wsilverio/tcc/cad/arquivos-maristela/mesa bolinhas_final1.pdf

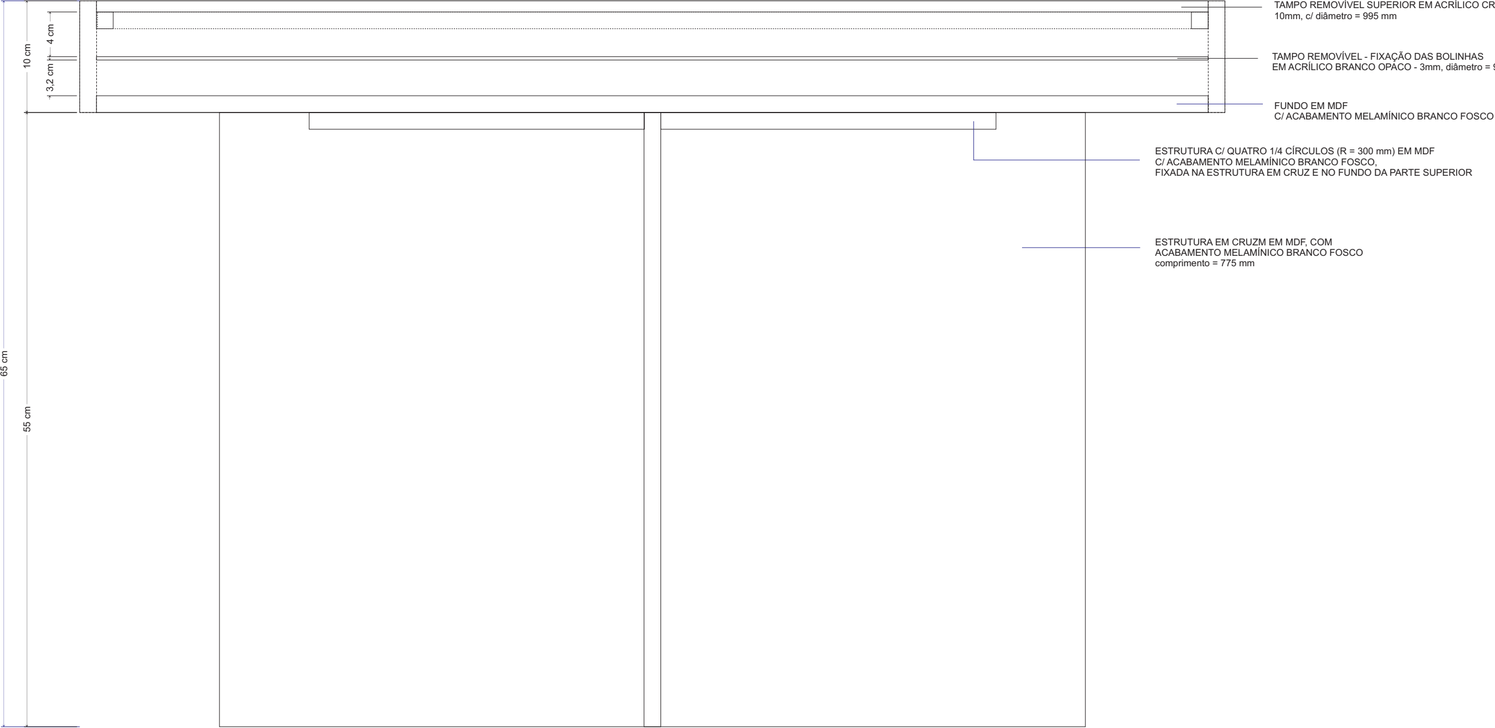
[picture p51: figure]
FUNDO EM MDF C/ ACABAMENTO MELAMÍNICO BRANCO FOSCO; C/ ACABAMENTO MELAMÍNICO BRANCO FOSCO,; ESTRUTURA EM CRUZM EM MDF, COM ACABAMENTO MELAMÍNICO BRANCO FOSCO comprimento = 775 mm; 10mm, c/ diâmetro = 995 mm; TAMPO REMOVÍVEL - FIXAÇÃO DAS BOLINHAS
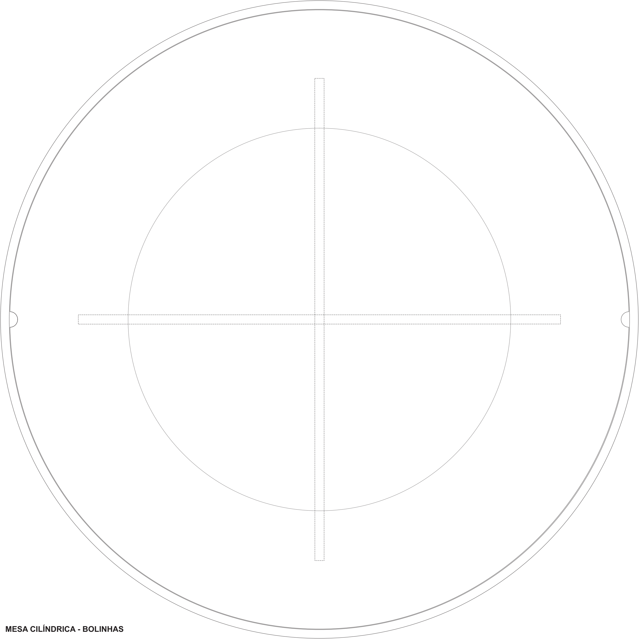
[picture p52: figure]
MESA CILÍNDRICA - BOLINHAS

quantidade = 1

Obs.:
1) Sem cantos vivos (raios não especificados = 1mm)
2) Desenho esquemático. VERIFICAR ESTRUTURA E DETALHES DE ENCAIXES E FIXAÇÕES.

ESTRUTURA C/ QUATRO 1/4 CÍRCULOS (R = 300 mm) EM MDF

FIXADA NA ESTRUTURA EM CRUZ E NO FUNDO DA PARTE SUPERIOR

TAMPO REMOVÍVEL SUPERIOR EM ACRÍLICO CRISTAL

EM ACRÍLICO BRANCO OPACO - 3mm, diâmetro = 995 mm
