wsilverio/tcc/cad/arquivos-maristela/mesa bolinhas_final2.pdf

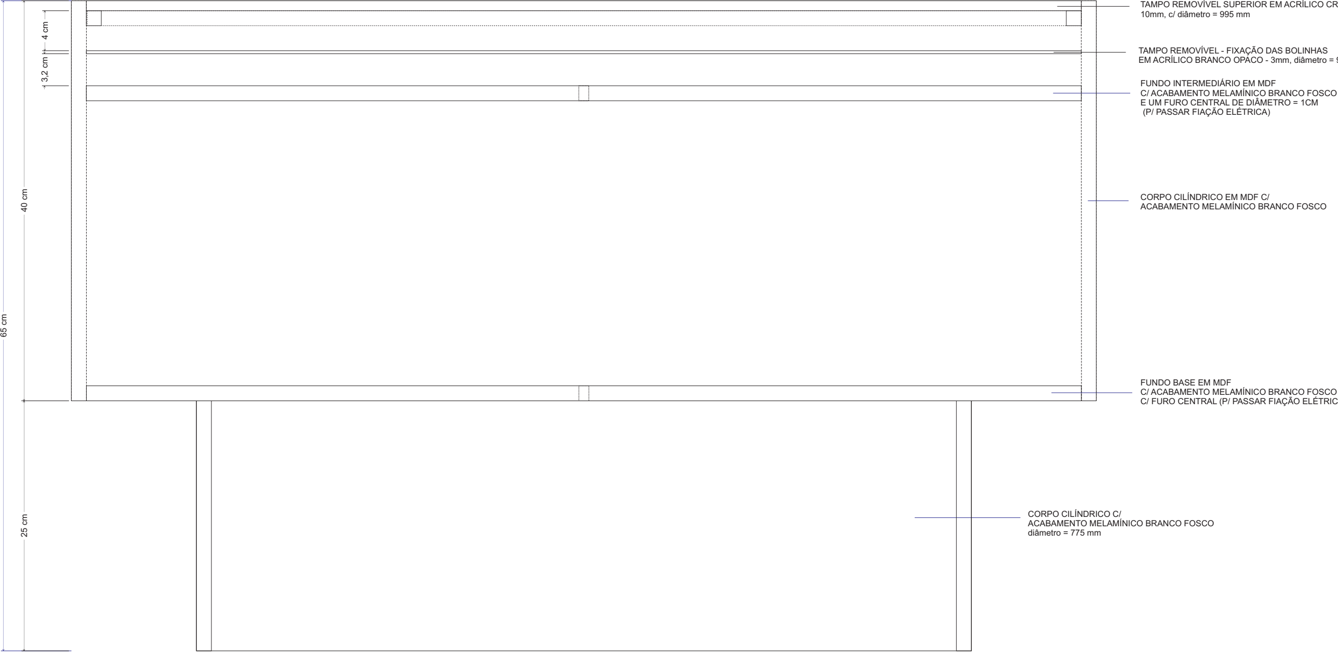
[picture p53: figure]
FUNDO INTERMEDIÁRIO EM MDF C/ ACABAMENTO MELAMÍNICO BRANCO FOSCO E UM FURO CENTRAL DE DIÂMETRO = 1CM (P/ PASSAR FIAÇÃO ELÉTRICA); 10mm, c/ diâmetro = 995 mm; TAMPO REMOVÍVEL - FIXAÇÃO DAS BOLINHAS; FUNDO BASE EM MDF C/ ACABAMENTO MELAMÍNICO BRANCO FOSCO; CORPO CILÍNDRICO EM MDF C/ ACABAMENTO MELAMÍNICO BRANCO FOSCO; CORPO CILÍNDRICO C/ ACABAMENTO MELAMÍNICO BRANCO FOSCO diâmetro = 775 mm
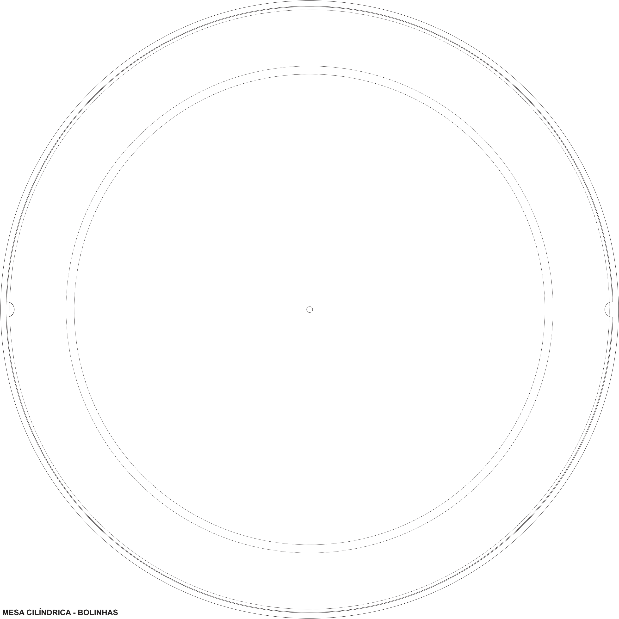
[picture p54: figure]
MESA CILÍNDRICA - BOLINHAS

quantidade = 1

Obs.:
1) Sem cantos vivos (raios não especificados = 1mm)
2) Desenho esquemático. VERIFICAR ESTRUTURA E DETALHES DE ENCAIXES E FIXAÇÕES.

TAMPO REMOVÍVEL SUPERIOR EM ACRÍLICO CRISTAL

EM ACRÍLICO BRANCO OPACO - 3mm, diâmetro = 995 mm

C/ FURO CENTRAL (P/ PASSAR FIAÇÃO ELÉTRICA)
