wsilverio/tcc/cad/arquivos-maristela/mesa-de-luz-cilindrica_final.pdf

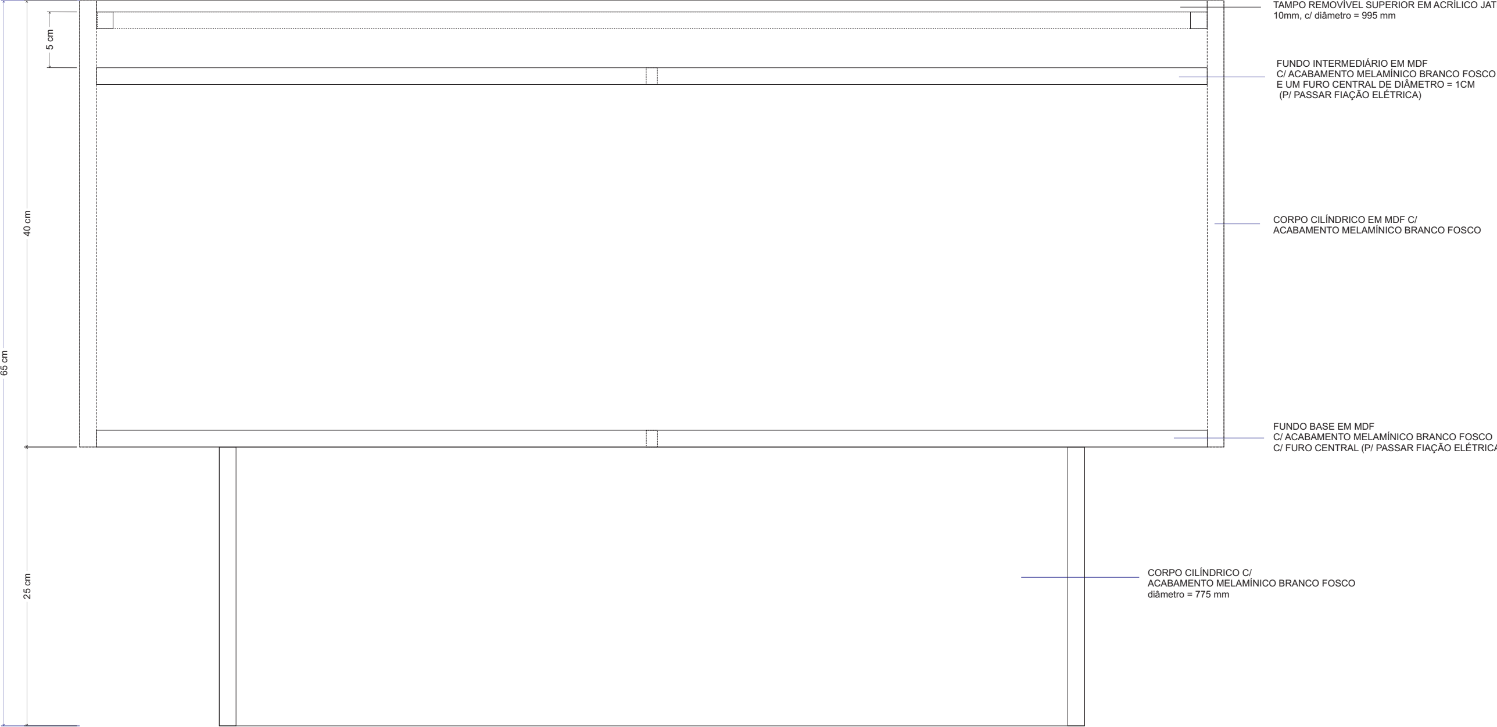
[picture p55: figure]
FUNDO INTERMEDIÁRIO EM MDF C/ ACABAMENTO MELAMÍNICO BRANCO FOSCO E UM FURO CENTRAL DE DIÂMETRO = 1CM (P/ PASSAR FIAÇÃO ELÉTRICA); 10mm, c/ diâmetro = 995 mm; FUNDO BASE EM MDF C/ ACABAMENTO MELAMÍNICO BRANCO FOSCO; CORPO CILÍNDRICO EM MDF C/ ACABAMENTO MELAMÍNICO BRANCO FOSCO; CORPO CILÍNDRICO C/ ACABAMENTO MELAMÍNICO BRANCO FOSCO diâmetro = 775 mm
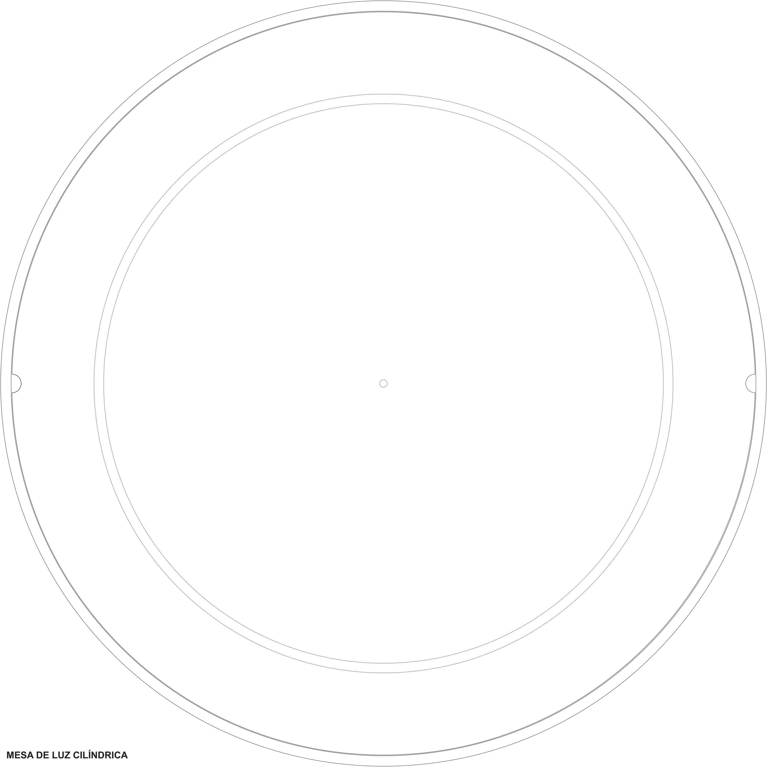
[picture p56: figure]
MESA DE LUZ CILÍNDRICA

quantidade = 1

Obs.:
1) Sem cantos vivos (raios não especificados = 1mm)
2) Desenho esquemático. VERIFICAR ESTRUTURA E DETALHES DE ENCAIXES E FIXAÇÕES.

TAMPO REMOVÍVEL SUPERIOR EM ACRÍLICO JATEADO

C/ FURO CENTRAL (P/ PASSAR FIAÇÃO ELÉTRICA)
