wsilverio/tcc/cad/arquivos-maristela/mesa-de-luz-cruz_final.pdf

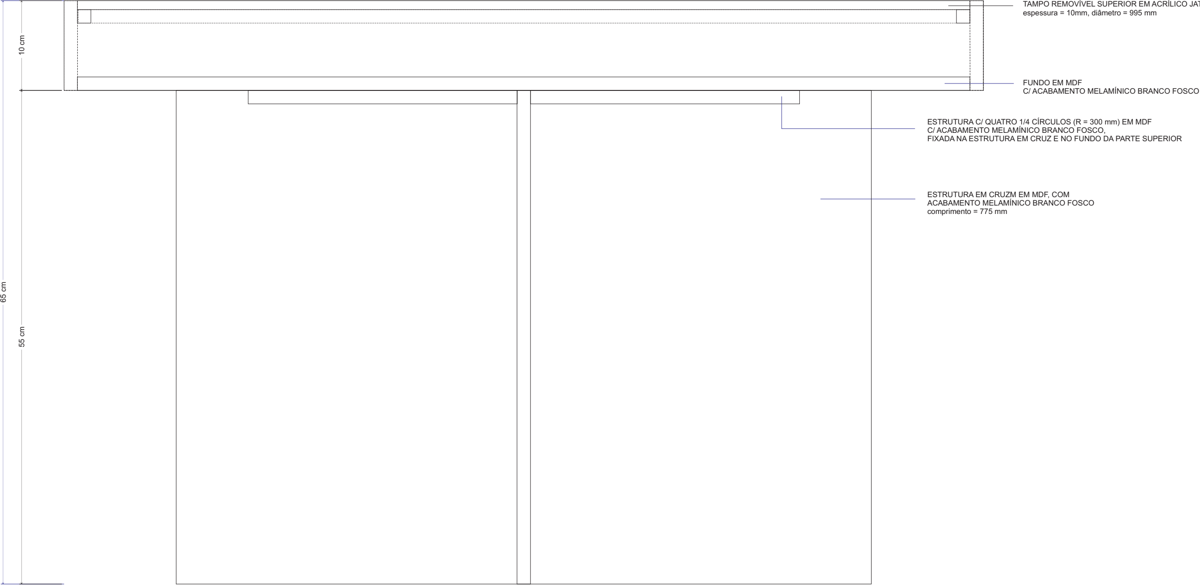
[picture p57: figure]
FUNDO EM MDF C/ ACABAMENTO MELAMÍNICO BRANCO FOSCO; espessura = 10mm, diâmetro = 995 mm; C/ ACABAMENTO MELAMÍNICO BRANCO FOSCO,; ESTRUTURA EM CRUZM EM MDF, COM ACABAMENTO MELAMÍNICO BRANCO FOSCO comprimento = 775 mm
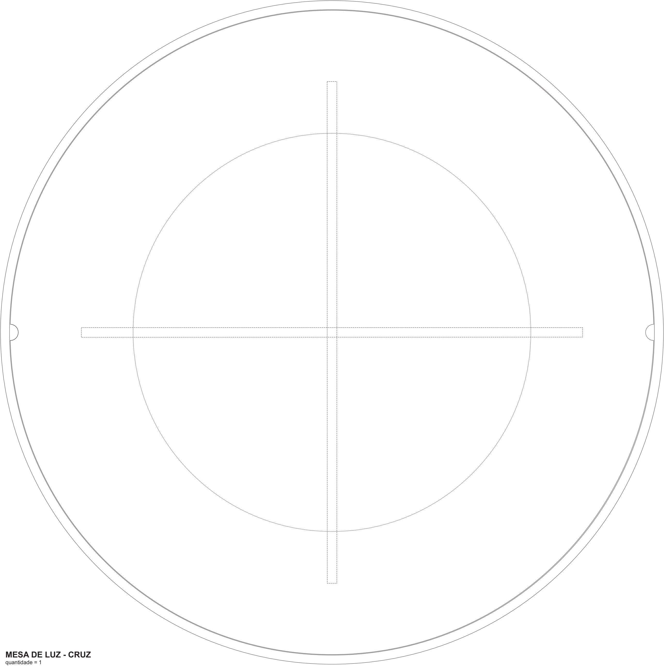
[picture p58: figure]
MESA DE LUZ - CRUZ; quantidade = 1

Obs.:
1) Sem cantos vivos (raios não especificados = 1mm)
2) Desenho esquemático. VERIFICAR ESTRUTURA E DETALHES DE ENCAIXES E FIXAÇÕES.

TAMPO REMOVÍVEL SUPERIOR EM ACRÍLICO JATEADO

ESTRUTURA C/ QUATRO 1/4 CÍRCULOS (R = 300 mm) EM MDF

FIXADA NA ESTRUTURA EM CRUZ E NO FUNDO DA PARTE SUPERIOR
