wsilverio/tcc/cad/arquivos-maristela/tampos_final.pdf

## TAMPO REMOVÍVEL DA MESA DE LUZ

Acrílico jateado - espessura = 10 mm - diâmetro 995 mm

quantidade = 1

Obs.:
1) Sem cantos vivos (raios não especificados = 1mm)

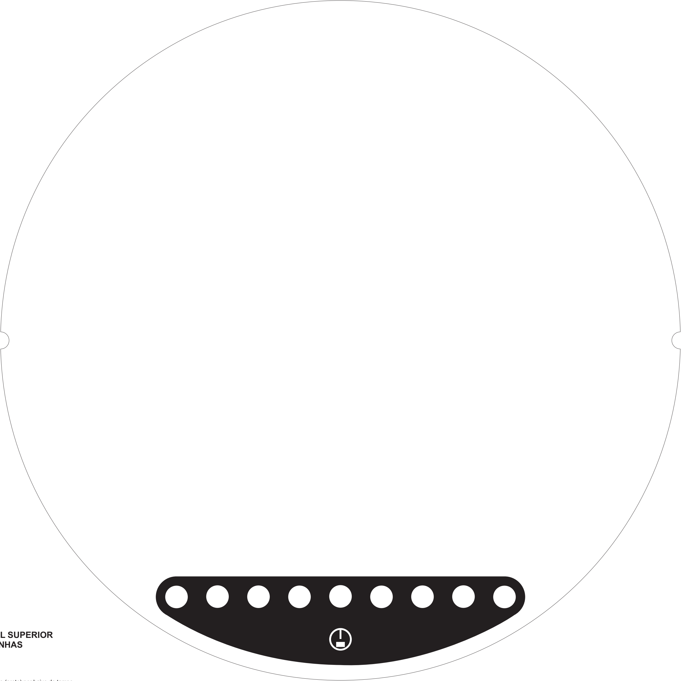
[picture p59: figure]

## TAMPO REMOVÍVEL SUPERIOR DA MESA DE BOLINHAS

acrílico cristal - 10 mm
diâmetro do tampo = 995 mm

Aplicação localizada de adesivo (preto) por baixo do tampo,
com recortes (áreas transparentes, indicadas em branco no desenho)

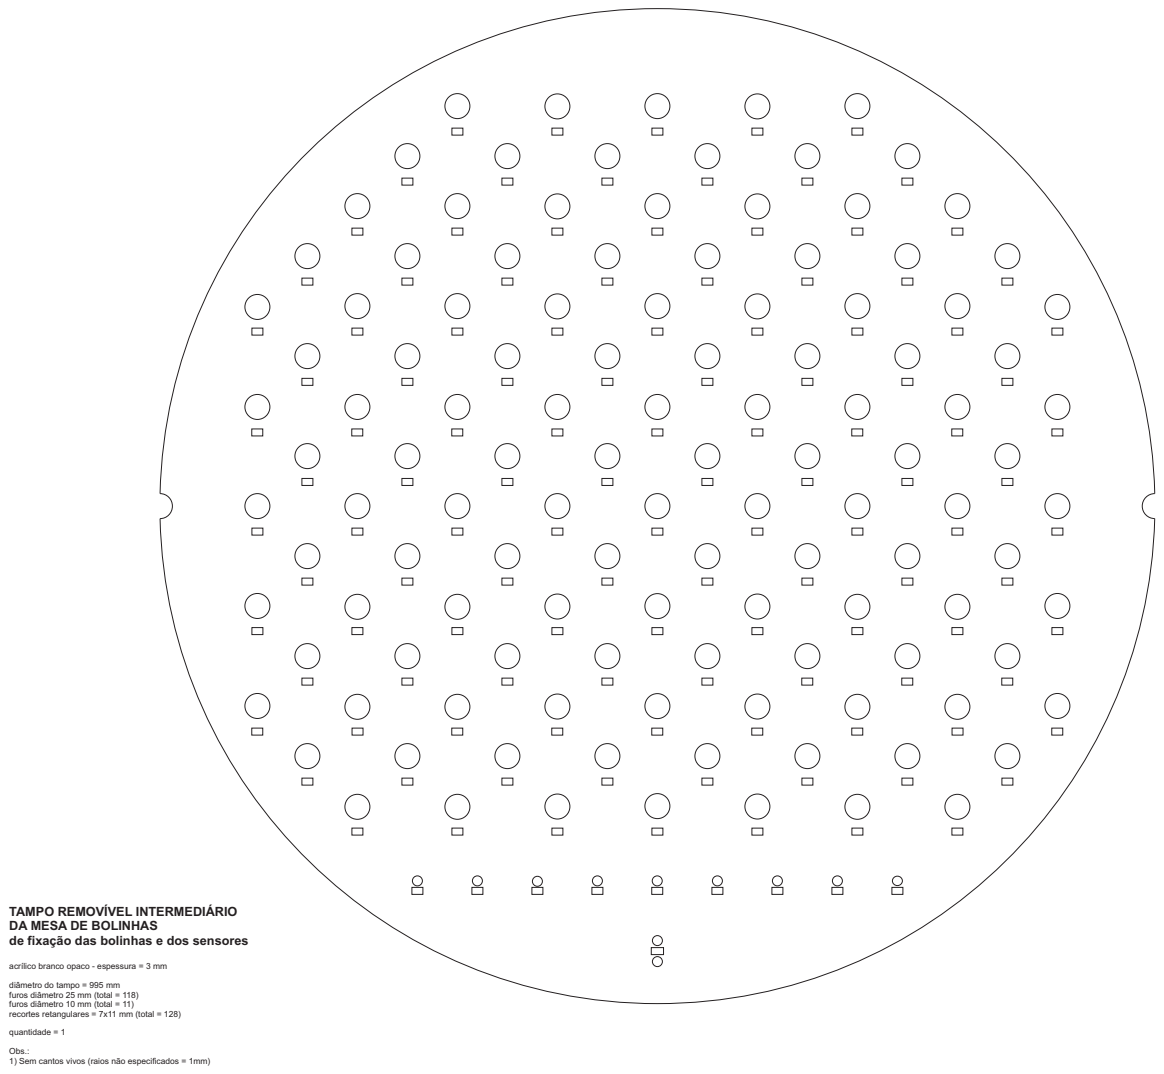
[picture p60: page 3]

TAMPO REMOVÍVEL INTERMEDIÁRIO
DA MESA DE BOLINHAS
de fixação das bolinhas e dos sensores

acrílico branco opaco - espessura = 3 mm

diâmetro do tampo = 995 mm
furos diâmetro 25 mm (total = 118)
furos diâmetro 10 mm (total = 11)
recortes retangulares = 7x11 mm (total = 128)
