wsilverio/tcc/documentos/proposta/build/relatorio-parcial.pdf

MINISTERIO DA EDUCAÇ ´ | AÕ
UNIVERSIDADE FEDERAL DO PARANÁ
PRO-REITORIA DE PESQUISA E P ´ | OS-GRADUAÇ ´ | AÕ
COORDENADORIA DE INICIAÇ AO CIENT ˜ | ÍFICA E INTEGRAÇ AO ACAD ˜ | EMICA ˆ
PROGRAMA DE INICIAÇ AO CIENT ˜ | ÍFICA E EM DESENVOLVIMENTO
TECNOLOGICO E INOVAÇ ´ | AÕ

## Wendeurick Emerick Silverio

### RELATORIO PARCIAL ´

INICIAÇ AO CIENT ˜ | ÍFICA:
PIBIC CNPq ( ), PIBIC CNPq Açoes Afirmativas ( ), PIBIC UFPR TN (x), PIBIC Fundaç ˜ | aõ
Araucaria ( ), PIBIC Volunt ´ | aria ( ), PIBIC Aç ´ | oes Afirmativas Volunt ˜ | aria ( ) ou PIBIC EM. ´

08/2015 a 07/2016

Simulaçao e projeto de amplificadores de pot ˜ | encia RF em ˆ

## tecnologia CMOS

Relatorio apresentado ´ | a Coordenado- `
| | ria de Iniciaçao Cient ˜ | ífica e Integraçaõ

### Academica da Universidade Federal ˆ

do Parana por ocasi ´ | ao da conclus ˜ | aõ
das atividades de Iniciaçao Cient ˜ | ífica
- Edital 2015/2016.

Orientador: Bernardo Rego Barros de Almeida Leite / Departamento de Engenharia Eletrica ´

Projeto de pesquisa: Projeto de circuitos integrados e componentes passivos para sistemas de comunicaçao sem fio / 2012006108 ˜

CURITIBA
2017

## Sumario ´

1 RESUMO | | 2
2 INTRODUÇ AO | 3 ˜
3 REVISAO DA LITERATURA | 4 ˜
3.1 Metricas para amplificadores de pot ´ | encia | ˆ | 4
3.2 Amplificadores de potencia program ˆ | aveis | ´ | 4
4 MATERIAIS E METODOS | 7 ´
5 REFERENCIAS | 8 ˆ

## 1 RESUMO

O projeto de pesquisa tem por objetivo uma compreensao e concepç ˜ | ao de sistemas ˜
de circuitos integrados de radiofrequencia, aprendizagem do uso de ferramentas compu- ˆ
tacionais de circuitos integrados e a utilizaçao desses conhecimentos em simulaç ˜ | oes e ˜
projetos de amplificadores de potencia (PAs). As etapas seguintes ter ˆ | ao como base dois ˜
circuitos previamente projetados e testados, ambos apresentados para o Programa de Pos- ´
Graduaçao em Engenharia El ˜ | etrica da UFPR na dissertaç ´ | ao de mestrado de Edson Leo- ˜
nardo dos Santos e Favero Guilherme Santos. Os dois apresentam est ´ | agios com reconfi- ´
gurabilidade, sendo um no estagio de ganho e outro no estagio de pot ´ | encia. ˆ
O projeto de iniciaçao cient ˜ | ífica começou com um estudo bibliografico e em seguida ´
teve um período de familiarizaçao e adaptaç ˜ | ao com as ferramentas necess ˜ | arias para o ini- ´
cio da fase de simulaçoes. Foram utilizados o ambiente ADE XL e o simulador Spectre RF ˜
na plataforma de Cadence Virtuoso. O proximo passo foi realizar simulaç ´ | oes com fontes ˜
de sinal modulado na entrada do amplificador. Foram consideradas para os sinais modulados normas de redes WPAN (Zigbee), WLAN (IEEE 802.11n - WiFi), e telefonia celular
(LTE). Nesta analise, traçaram-se o espectro de sa ´ | ída do PA, permitindo a obtençao da ˜
razao de pot ˜ | encia no canal adjacente (ACPR), e tamb ˆ | em a constelaç ´ | ao de sa ˜ | ída, permi-
tindo a obtençao da magnitude do erro vetorial (EVM) associada a cada uma das normas. ˜
Com base nestes resultados, foi elaborada documentaçao descrevendo a configuraç ˜ | ao re- ˜
comendada do simulador para estas analises na simulaç ´ | ao de amplificadores de pot ˜ | encia ˆ
de radiofrequencia. ˆ

## 2 INTRODUÇ AÕ

O mundo de hoje e conectado por um grande n ´ | umero de sistemas de comunicaç ´ | ao, ˜
em sua grande maioria sem fio. Muitas deles operam na regiao de 2.4 GHz, como IEEE ˜ 802.15.4, IEEE 802.11n e LTE.
Zigbee (IEEE 802.15.4) define um conjunto de protocolos de comunicaçao adaptado a ˜
redes de sensores com baixa taxa de transmissao de dados, dist ˜ | ancias curtas de trans- ˆ
missao e baixo consumo de energia. Dispositivos baseados em Zigbee operam nas bandas ˜
de 868 MHz, 915 MHz e 2,4 GHz. A taxa maxima de transmiss ´ | aõ e de 250 kbit/s. Zigbee ´ | é
usado principalmente para aplicaçoes alimentadas por bateria onde baixa transfer ˜ | encia de ˆ
dados, baixo custo e longa duraçao de bateria s ˜ | ao caracter ˜ | ísticas desejadas. Em muitas
aplicaçoes, o tempo total do dispositivo usado para efetivamente fazer alguma transmiss ˜ | aõ
ou recepçaõ e muito curto, gastando a maior parte do tempo em modo de espera. Como ´ resultado, a bateria de dispositivos que utilizam esse protocolo podem durar anos [z]. Como a camada de controle de acesso ao meio (MAC) e a camada física (PHY) sao definida pelas ˜
normas IEEE 802.15.4, a modulaçao em 2,4 GHz ˜ | e definida como QPSK. ´
Uma rede local sem fio baseada nas normas da IEEE 802.11 leva o nome de Wi-Fi. As
normas da IEEE 802.11 sao um conjunto de especificaç ˜ | oes para as camadas MAC e PHY ˜
para implementaçao de WLANs para comunicaç ˜ | ao em frequ ˜ | encias de 2,4 GHz, 3,6 GHz, 5 ˆ
GHz e 60 GHz. Umas das atualizaçoes da norma, a qual recebeu o nome de IEEE 802.11n, ˜
trabalha com frequencias de 2,4 GHz e 5 GHz, tem como principal caracter ˆ | ística um pro-
cesso que permite uso de mais de uma antena para transmitir e receber dados (MIMO) o
que aumenta a taxa de transmissao. O padr ˜ | ao 802.11n ˜ | e capaz de fazer transmiss ´ | oes na ˜
faixa de 300 Mb/s e, teoricamente, pode atingir taxas de ate 600 Mb/s. No modo de trans- ´
missao mais simples, com uma via de transmiss ˜ | ao, o 802.11n pode chegar ˜ | a casa dos 150 `
Mb/s. Os modos de modulaçao definido pela norma s ˜ | ao BPSK, QPSK,16-QAM e 64-QAM ˜
[wlan].
Long Term Evolution (LTE), e uma norma de comunicaç ´ | ao m ˜ | ovel de alta taxa de trans- ´
missao de dados. As frequ ˜ | encias de operaç ˆ | ao v ˜ | ao de 700 MHz at ˜ | e 2600 MHz. Um dos ´
objetivos para a criaçao de tal norma foi para recriar e simplificar a arquitetura de redes para ˜
sistemas baseados em IP, com notavel reduç ´ | ao de lat ˜ | encia comparada a arquitetura 3G. O ˆ
esquema de modulaçao para transmiss ˜ | oes de terminais m ˜ | oveis para estaç ´ | oes r ˜ | adio-base ´
sao QPSK e 16QAM, enquanto que para transmiss ˜ | oes a partir das estaç ˜ | oes r ˜ | adio-base ´
tambem´ | e inclu ´ | ído 64QAM[lte].
Um fator determinante para um dispositivo movel ´ | e a duraç ´ | ao de sua bateria. Esta ca- ˜
racterística e determinada pelos seus componentes que mais consomem pot ´ | encia e afetam ˆ
diretamente a satisfaçao dos consumidores [ ˜ | fav]. Em um receptor de radiofrequencia, um ˆ
dos componentes mais importantes e um dos que consomem mais potencia ˆ | e o amplifica- ´
dor de potencia (PA). A funç ˆ | ao de um PA ˜ | e tornar um sinal fraco em forte, sem acrescentar ´
distorçoes significativas para uma larga faixa de valores de pot ˜ | encias [ ˆ | leo]. Para que ele
tenha um comportamento adequado deve-se manter um compromisso entre a linearidade,
ganho de potencia, estabilidade e efici ˆ | encia. Um circuito amplificador ˆ | e constitu ´ | ído prin-
cipalmente por um estagio de ganho, um est ´ | agio de pot ´ | encia e redes de casamento de ˆ
impedancia. ˆ
Para conseguir um menor consumo em um PA e poss ´ | ível faze-lo program ˆ | avel, com ´
diversos modos de funcionamento. Assim, quando naõ e necess ´ | ario transmitir a m ´ | axima ´
potencia de sa ˆ | ída, o circuito pode operar em um modo de menor consumo de potencia. A ˆ
reconfigurabilidade pode estar presente em varias partes do circuito, incluindo o est ´ | agio de ´
ganho ou no estagio de pot ´ | encia ˆ

## 3 REVISAO DA LITERATURA ˜

3.1 Metricas para amplificadores de pot ´ | encia ˆ
Para um amplificador de potencia proposto para comunicaç ˆ | ao m ˜ | ovel ou sem fio, pot ´ | encia ˆ
de saída, eficiencia, ganho e linearidade s ˆ | ao algumas das mais importantes caracter ˜ | ísticas,
e estas podem ser facilmente quantificadas. Por outro lado custo e confiabilidade nao s ˜ | aõ
tao simples de se quantificar embora suas import ˜ | ancias n ˆ | ao devam ser subestimadas [ ˜ | pat].
A potencia de sa ˆ | ída, definida como a potencia ativa entregue pelo PA ˆ | a antena, ne- `
cessaria para um amplificador ´ | e determinada inteiramente pelas aplicaç ´ | oes a que se des- ˜
tinam. Estabilidade e um fator cr ´ | ítico em amplificadores de potencia RF, uma vez que os ˆ
dispositivos modernos RF sao potencialmente inst ˜ | aveis [ ´ | cripps]. O PA nao deve oscilar ˜
independente de qual fonte e carga estejam ligadas na entrada e na saída. A instabilidade
pode ocorrer devido a realimentaç ` | ao do sinal ou ganho excessivo em frequ ˜ | encias fora da ˆ
banda.
Usualmente os amplificadores de potencia s ˆ | ao divididos em v ˜ | arias classes. Em RF, es- ´
sas diferentes classes sao divididas basicamente em dois grupos: amplificadores lineares e ˜
nao-lineares. Os amplificadores lineares s ˜ | ao classificados em A, AB, B e C, no entanto, es- ˜
ses amplificadores apresentam uma eficiencia mais baixa. Os amplificadores n ˆ | ao-lineares ˜
sao classificados em D, E e F, entre outras, sendo capazes de alcançar efici ˜ | encias mais ˆ
altas. Nos amplificadores lineares, o transistor do PA opera como uma fonte de corrente controlada, enquanto que nos amplificadores nao-lineares, o transistor do PA opera como ˜ uma chave.
Um grande numero de m ´ | etricas s ´ | ao relevantes quando se quer avaliar a linearidade de ˜
um PA. Por exemplo, analise linear de pequenos sinais ´ | e feita utilizando par ´ | ametros-S a fim ˆ
de avaliar o coeficiente de reflexao, ganho direto, isolaç ˜ | ao e estabilidade. Caracterizaç ˜ | aõ
de grande sinais e tamb ´ | em muito ´ | util, pois permite observar o comportamento na sa ´ | ída do
PA conforme ocorre uma variaçao na entrada. Quando observado o m ˜ | odulo da pot ´ | encia ˆ
da saída em funçao da pot ˜ | encia de entrada (curva AM-AM), podemos tirar informaç ˆ | oes ˜
como ponto de compressao de 1dB e a pot ˜ | encia de sa ˆ | ída saturada. Entretanto, quando
avaliado a variaçao de fase de sa ˜ | ída conforme a entrada e variada (cuva AM-PM), podemos ´
observar que mesmo sendo um sinal de formato constante aplicado a entrada e observado ´
distorçoes na sa ˜ | ída. Para avaliar a eficiencia do circu ˆ | íto usa-se a metrica de efici ´ | encia de ˆ
potencia adicionada (PAE), que ˆ | e uma relaç ´ | ao entre a diferença da pot ˜ | encia de sa ˆ | ída com
a entrada em relaçao a pot ˜ | encia DC adicionada ao circu ˆ | íto.
Outra parte crucial na analise da linearidade de um PA ´ | e sua avaliaç ´ | ao com um sinal ˜
modulado na entrada. Como o PA introduz distorçoes, a constelaç ˜ | ao de sa ˜ | ída naõ e a ´
mesma que a constelaçao de entrada. Uma m ˜ | etrica para a medida deste tipo de distorç ´ | aõ
e a magnitude do vetor de erro (EVM). Essa m ´ | etrica consiste em fazer a raiz da m ´ | edia ´
da distancia entre o ponto da constelaç ˆ | ao em sua entrada e sa ˜ | ída. O impacto da nao- ˜
linearidade naõ e visto somente no canal de transmiss ´ | ao, ˜ | e necess ´ | ario ent ´ | ao quantizar o ˜
valor de potencia que ˆ | e dissipado nas bandas adjacentes, e isso ´ | e feito pela m ´ | etrica raz ´ | aõ
de potencia do canal adjacente (ACPR), esta ˆ | e uma relaç ´ | ao da pot ˜ | encia dissipada na banda ˆ
de transmissao pela pot ˜ | encia nas bandas laterais, tanto superior quanto inferior. ˆ
3.2 Amplificadores de potencia program ˆ | aveis ´

A transcondutancia de um MOSFET depende diretamente do seu comprimento de canal. ˆ
Entao, transistores com maiores tamanhos de canal alcançam maiores valores de pot ˜ | encia ˆ

de saída a um custo maior de potencia DC. Ent ˆ | aõ e poss ´ | ível habilitar ou desabilitar transis-
tores de diferentes tamanhos dentro do circuito visando a potencia de sa ˆ | ída desejada[fav].
Este trabalho tera como base dois amplificadores de pot ´ | | encia que utilizam essa arquite- ˆ
tura, sendo que em um a reconfigurabilidade se encontra no estagio de potencia e o outro ˆ se encontra no estagio de ganho.
Primeiramente o amplificador de [leo] com controle de ganho e apresentado para aplicaç ´ | oes ˜
em 2,4 GHz, o esquematico do circuito pode ser vista na figura 1 juntamente com uma mi- ´ crografia do chip fabricado.

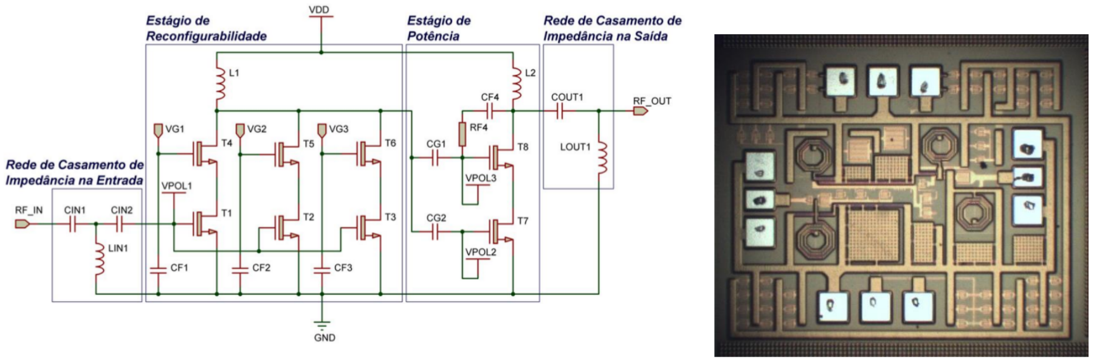
[picture p64: figure]

Figura 1: (a) Esquematico e (b) micrografia de [ ´ | leo].
O ganho de potencia pode ser controlado digitalmente em seis modos atrav ˆ | es da combi- ´
naçao de tr ˜ | es bits. Esta t ˆ | ecnica foi utilizada para alcançar uma melhora na efici ´ | encia em ˆ
potencias de recuo. O projeto foi implementado usando uma tecnologia CMOS 0,13 µm ˆ
e e capaz de fornecer um ganho de pot ´ | encia vari ˆ | avel entre 22,4 dB e 31 dB, os modos ´
intermediarios podem ser vistos na figura 2, uma efici ´ | encia m ˆ | axima de 19%, com uma fonte ´
de alimentaçao de 1,8 V. A pot ˜ | encia consumida pelo amplificador ˆ | e reduzida de 196,2 mW ´
no modo de maior ganho para 171 mW no modo de menor ganho, permitindo uma eficiencia ˆ
melhor quando o ganho maximo n ´ | aõ e necess ´ | ario para a transmiss ´ | ao[ ˜ leo].

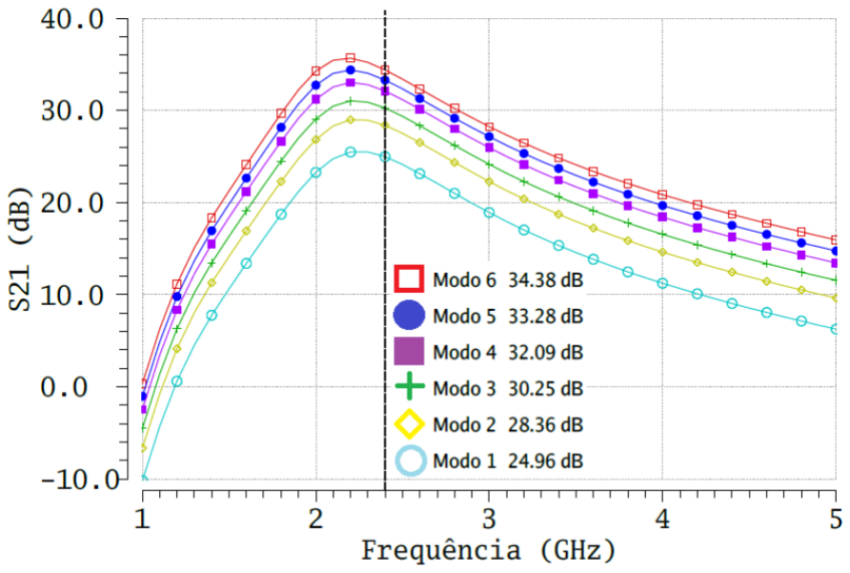
[picture p65: figure]

Figura 2: Ganhos de [leo].

O proximo circuito ´ | e apresentado em [ ´ | fav], o qual o PA apresentado possui o estagio de

potencia reconfigur ˆ | avel o seu esquem ´ | atico pode ser visto na figura 3 juntamente com o seu ´
leiaute.

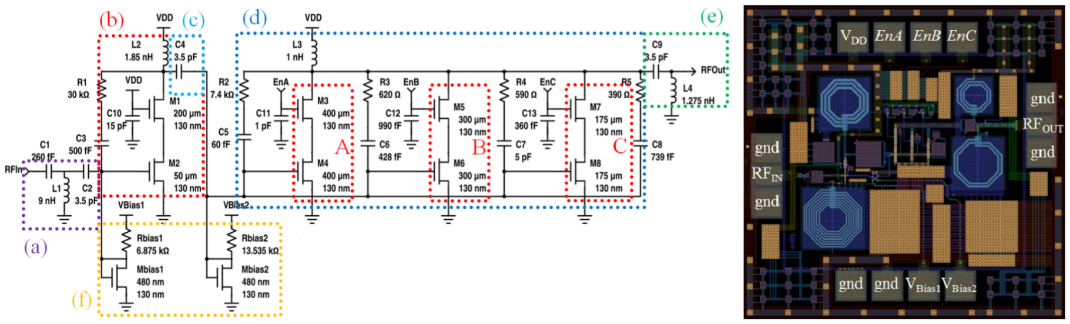
[picture p66: figure]

Figura 3: Esquematico: casamento de imped ´ | ancia de entrada (a), est ˆ | agio de ganho (b), ´
componente de casamento (c), estagio de ganho reconfigur ´ | avel (d), casamento de im- ´
pedancia de sa ˆ | ída (e), e circuitos de referencia de tens ˆ | ao para polarizaç ˜ | ao. A figura ao ˜
lado e o leiaute de [ ´ | leo].
Este PA tem 7 modos de operaçao para alcançar uma grande faixa de pot ˜ | encia de sa ˆ | ída
e reduzir a potencia DC.O PA foi implementado usando tecnologia CMOS 0,13 µm. Trabalha ˆ na faixa de 2,4GHz com alimentaçao de 1,8V. O modo de menor ganho possui 8.1 dBm de ˜
potencia saturada, 13.5 dB de ganho de pot ˆ | encia e consome 171 mW de pot ˆ | encia DC. No ˆ
modo de maior ganho a potencia saturada de sa ˆ | ída e de 18.9 dBm com ganho de pot ´ | encia ˆ
de 21.1 dB consumindo 415 mW de potencia DC. Um gr ˆ | afico dos ganhos apresentados nos ´
outros modos pode ser visto na figura 4.

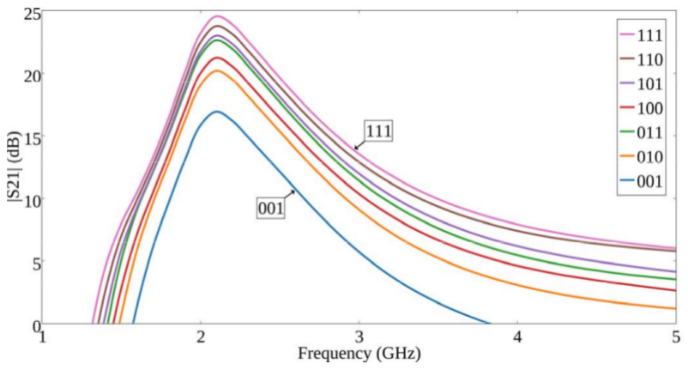
[picture p67: figure]

Figura 4: Ganhos de [leo].

## 4 MATERIAIS E METODOS ´

As simulaçoes ser ˜ | ao todas realizadas no software Cadence Virtuoso, sendo utilizado o ˜
ambiente ADE XL e o simulador Spectre RF. Para as analises de linearidade com sinais ´
modulados, sera utilizada uma an ´ | alise do tipo Envelope pois esta an ´ | alise tem um melhor ´
desempenho do que uma simulaçao transiente quando processos r ˜ | apidos e lentos ocorrem ´
ao mesmo tempo no circuito. O termo para este tipo de simulaçaõ e simulaç ´ | ao multitaxa. ˜
Na simulaçao transiente, um grande n ˜ | umero de ciclos de um sinal r ´ | apido deve ser simulado ´
para adquirir um comportamento lento do circuito. Logo, ao inves de se simular todo o ´
processo,a analise envelope pula v ´ | arios ciclos do sinal r ´ | apido para avaliar as mudanças ´
lentas. Todavia, mesmo pulando varios ciclos, o resultado ´ | e quase t ´ | ao preciso quanto ˜
analise de transiente.
Os dados procurados nessa simulaçao s ˜ | ao basicamente vetor de magnitude de erro ˜
(EVM - Error Vector Magnitude), que e uma indicaç ´ | ao da qualidade de transmiss ˜ | ao. Devido ˜
as n ` | ao-linearidades do amplificador, a posiç ˜ | ao dos s ˜ | ímbolos no diagrama I-Q pode ser
deslocada da posiçao ideal. Cada protocolo tem um valor m ˜ | aximo para EVM [ ´ | z]. Outra
informaçao desejada ˜ | e a relaç ´ | ao de pot ˜ | encia do canal adjacente. ˆ
Sera projetado um circuito combinando os PAs com reconfigurabilidade, o est ´ | agio de ´
ganho do PA em [leo] e o estagio de pot ´ | encia do PA em [ ˆ | fav] afim de ter um PA com dois
estagios de reconfigurabilidade podendo ter um controle ainda maior na pot ´ | encia de sa ˆ | ída
e eficiencia do PA. ˆ

## 5 REFERENCIAS ˆ
