wsilverio/tcc/cad/anotacoes_distancia.pdf

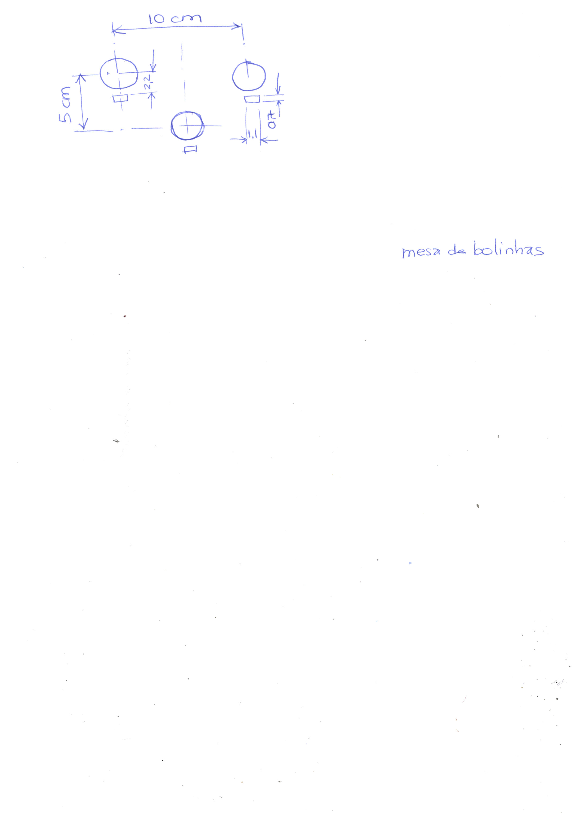
[picture p68: page 1]
