wsilverio/tcc/documentos/proposta/proposta-tcc.pdf

UNIVERSIDADE FEDERAL DO PARANÁ SETOR DE TECNOLOGIA
DEPARTAMENTO DE ENGENHARIA ELETRICA ´

WENDEURICK EMERICK SILVERIO GRR20134722

## Proposta do Projeto de Graduaçaõ

## Desenvolvimento de Mesa de Luz Interativa para Experimento de Ciencias para Crianç as ˆ

Plano do Trabalho de Conclusao de Curso, ˜ apresentado como requisito parcial para a obtençao do grau de Engenheiro Ele- ˜ tricista, no programa de graduaçao em ˜
Engenharia Eletrica ( ´ | enfase em Eletr ˆ | onica e ˆ
Telecomunicaçoes) da Universidade Federal ˜ do Parana.´
Orientador: Prof. | Dr. | James Alexandre
Baraniuk

CURITIBA
2018

## Sumario ´

1 Contextualizaçao e Resumo | 2 ˜
2 Proposta de Trabalho | 3
2.3 Publico Alvo | ´ | 3
2.6 Recursos necessarios | ´ | | 4
2.8 Contribuiçao esperada para a ˜ | enfase | ˆ | 4
2.9 Cronograma a ser seguido indicando os marcos para avaliaçao, seguindo o ˜
cronograma divulgado pela Comissao Permanente do TCC | ˜ | 4
2.10 Importancia do Projeto para a formaç ˆ | ao dos autores | ˜ | 5
3 Referencias | 6 ˆ

## 1 Contextualizaçao e Resumo ˜

A luz exerce um papel essencial no nosso cotidiano e esta presente das mais diversas ´
formas: iluminaçao, medicina, pesquisas cient ˜ | íficas, geraçao de energia, telecomunicaç ˜ | oes, ˜
educaçao, arte, cultura e etc. A Assembleia Geral das Naç ˜ | oes Unidas proclamou o ano de ˜
2015 como o Ano Internacional da Luz e das Tecnologias Baseadas na Luz [1], a fim de
reconhecer tal importancia para a vida dos cidad ˆ | aos e para o desenvolvimento futuro da ˜
sociedade mundial. No ano da celebraçao, a UNESCO promoveu uma s ˜ | erie de eventos ´
por varios pa ´ | íses [2], com o intuito de destacar que o aumento da consciencia mundial e ˆ
o fortalecimento do ensino da ciencia e das tecnologias da luz s ˆ | ao essenciais para abor- ˜
dar os desafios futuros e atuais, tais como o desenvolvimento sustentavel, a energia e as ´
comunicaçoes, assim como para melhorar a qualidade de vida dos pa ˜ | íses menos desenvol-
vidos e dos em desenvolvimento.
Baseada em tal iniciativa, a exposiçao “Luz, Ci ˜ | encia e Emoç ˆ | ao”, idealizada pela arqui- ˜
teta Dra. Maristela Mitsuko Ono e pelo engenheiro Dr. James Alexandre Baraniuk, traz experimentos envolvendo os conceitos de luz trabalhados nos ensinos pre-escolar e fun- ´
damental, cada um com seu grau de impressao aos sentidos. A exposiç ˜ | ao proporciona ˜
uma experiencia tang ˆ | ível-visual impactante aos observadores, causando deslumbramento
e entusiasmo atraves da arte e interaç ´ | ao. ˜
O trabalho aqui proposto trata-se do desenvolvimento do hardware e firmware embar-
cado de um dos mais de 20 experimentos dessa exposiçao. A ˜ | Mesa de Bolinhas, que
se enquadra na area art ´ | ística da mostra, e uma matriz de ´ | LEDs interativa, elaborada pela
arquiteta Dra. Maristela Mitsuko Ono, composta por mais de 100 bolinhas de ping-pong, cada uma correspondente a um par LED-sensor reflexivo. Ela permite que o visitante “pinte
com luz” ao passar a mao sobre a mesa. Sua vista superior do projeto ˜ | e apresentada na ´
Figura 1.

Figura 1: Vista superior da mesa

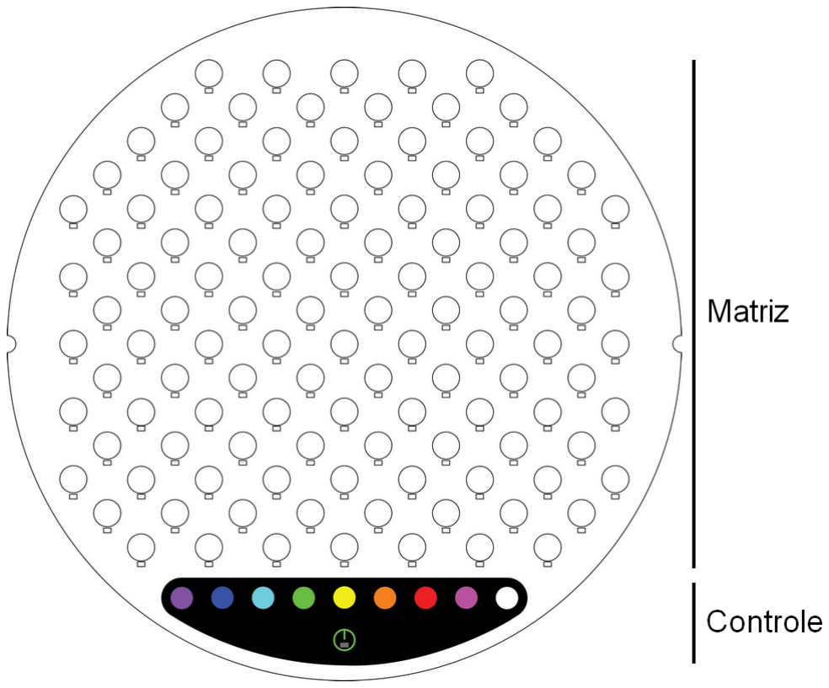
[picture p69: figure]

Fonte: (MITSUKO, 2016)

## 2 Proposta de Trabalho

### 2.1 Título

Desenvolvimento de Mesa de Luz Interativa para Experimento de Ciencias para Crianças ˆ | .

### 2.2 Objetivos

### 2.2.1 Objetivo Geral

Desenvolver o hardware e o firmware embarcado da “Mesa de Bolinhas”, apresentando
o prototipo funcional do projeto. Ser ´ | ao 128 LEDs program ˜ | aveis, controlados por seus res- ´
pectivos sensores de presença.

### 2.2.2 Objetivos Específicos

- Desenvolvimento de uma matriz mapeavel, onde cada ´ | LED possa ser controlado indi-
vidualmente;
- Desenvolvimento de uma matriz de entrada, onde cada sensor reflexivo possa ser lido individualmente;
- Software microcontrolado que gerencie a interface humano-maquina; ´
- Leiaute e montagem das Placas de Circuito Impresso (PCI);
- Integraçao da eletr ˜ | onica com a mec ˆ | anica do projeto. ˆ

### 2.3 P úblico Alvo

A serventia do projeto e destinada ao mesmo p ´ | ublico alvo da exposiç ´ | ao: crianças e ado- ˜
lescentes dos ensinos fundamental e medio. Al ´ | em disso, o projeto pode ser de interesse de ´
designers e artistas, uma vez que abrange areas de tecnologia, interaç ´ | ao e arte generativa. ˜

### 2.4 Diferencial do Projeto

Alem de ser uma matriz interativa aut ´ | onoma, a Mesa de Bolinhas ter ˆ | a uma interface ´
que possibilitara o controle atrav ´ | es de outros dispositivos (computador, por exemplo). Isso ´
possibilitara a integraç ´ | ao com programas de ˜ | led-mapping e geradores de visuais.
Tratando-se de uma proposta inovadora, pretende-se solicitar a patente do projeto.

### 2.5 Metodologia de desenvolvimento do estudo

A metodologia se dara por meio de prot ´ | otipos, servindo de prova de conceito. Logo ´
apos, passa-se ´ | a implementaç ` | ao e execuç ˜ | ao do projeto. ˜

### 2.6 Recursos necessarios ´

Os materiais (mesa, tampa acrílica e demais partes mecanicas) j ˆ | a foram adquiridos ´
pelo curso de Engenharia Eletrica, atrav ´ | es do prof. James Baraniuk, e est ´ | ao no Labo- ˜
ratorio de Efici ´ | encia Energ ˆ | etica. O projeto encontra-se sem o dispositivo eletr ´ | onico, cuja ˆ
proposta deste trabalho e de desenvolv ´ | e-lo e integr ˆ | a-lo ´ | a parte mec ` | anica. Para isso, ser ˆ | aõ
necessarios: ´
- Software CAD para o leiaute das placas;
- Material para fabricaçao dos prot ˜ | otipos (PCIs, LEDs program ´ | aveis (WS2812) e demais ´
componentes eletronicos); ˆ
- Plataforma de desenvolvimento (microcontrolador da família ESP8266);

### 2.7 Resultados fundamentais a serem atingidos

Prototipo funcional da Mesa de Bolinhas, montagem das PCIs e integraç ´ | ao com a mec ˜ | anica ˆ
do projeto.
2.8 Contribuiçao esperada para a ˜ | enfase ˆ
A nível geral, o projeto contribui no quesito integraçao com a ˜ | area art ´ | ística e de de-
sign. A nível tecnico, o projeto trar ´ | a recursos/implementaç ´ | oes de mapeamento de ˜ | pixels,
sistema de debouncing para varios sensores, implementaç ´ | ao de ˜ | software desenvolvido em
topologia de Maquina de Estados Finita e etc. ´

### 2.9 Cronograma a ser seguido indicando os marcos para avaliaçao, ˜ seguindo o cronograma divulgado pela Comissao Permanente do ˜ TCC

Atividade/Mesˆ | Agosto | Setembo | Outubro | Novembro
Atividade 1 | X | X
1ª Avaliaçaõ | | X
Atividade 2 | | X | X
Banca | | | X
Atividade 3 | | | X | X
Entrega do Relatorio ´ | | | | X
Apresentaçao Final ˜ | | | | X
- Atividade 1: desenvolvimento da seçao “Matriz” ˜
- Atividade 2: desenvolvimento da seçao “Controle” ˜
- Atividade 3: finalizaçao e integraç ˜ | ao com a mec ˜ | anica ˆ

2.10 Importancia do Projeto para a formaç ˆ | ao dos autores ˜
Para o aluno, o conhecimento aqui adquirido e de fundamental import ´ | | | ancia para sua ˆ
formaçao e interdisciplinaridade, uma vez que abrange resoluç ˜ | ao de problemas no campo ˜
da engenharia eletronica / sistemas embarcados e o interc ˆ | ambio com outras ˆ | areas. ´
Para os idealizadores, o projeto passara a ser parte da exposiç ´ | ao “Luz, Ci ˜ | encia e ˆ
Emoçao”, proporcionando uma experi ˜ | encia tang ˆ | ível-visual impactante aos observadores,
causando deslumbramento e entusiasmo atraves da arte e interaç ´ | ao, n ˜ | ao s ˜ | o das crianças e ´
adolescente, mas tambem de pessoas que se interessem pela integraç ´ | | ao entre tecnologia, ˜
arte e design.

### 2.11 Bibliografia a ser utilizada

- GAMMA, Erich et al. Design Patterns: Elements of Reusable Object-Oriented Software. 10. ed. Mountain View: Addison-Wesley Professional, 1994. 416 p.
- WAGNER, Ferdinand et al. Modeling Software with Finite State Machines. 1. ed. Boston: Auerbach Publications, 2006. 390 p.

## 3 Referencias ˆ

## Referencias ˆ

[1] United Nations. 68/221. International Year of Light and Light-based Technologies, 2015.
2014. URL: http://www.light2015.org/dam/About/Resources/Resolution/
Resolution_EN.pdf (acesso em 18/02/2017).
[2] UNESCO. International Year of Light. 2015. URL: http://www.light2015.org/
Home/Event-Programme.html (acesso em 18/02/2017).
