wsilverio/tcc/documentos/proposta/img/mesa-bloco-2.jpg

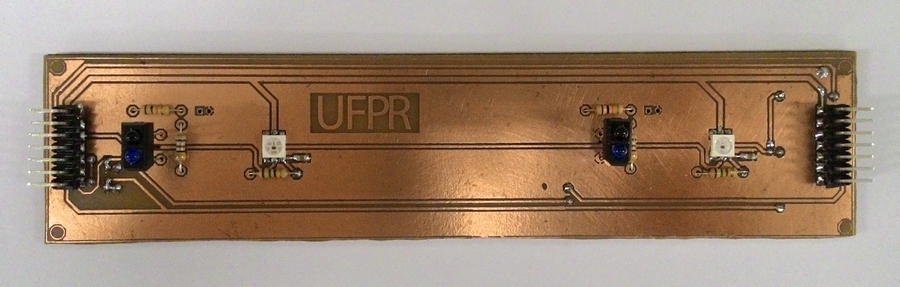
documentos/proposta/img/mesa-bloco-2.jpg
