wsilverio/tcc/documentos/proposta/img/mesa-blocos.jpg

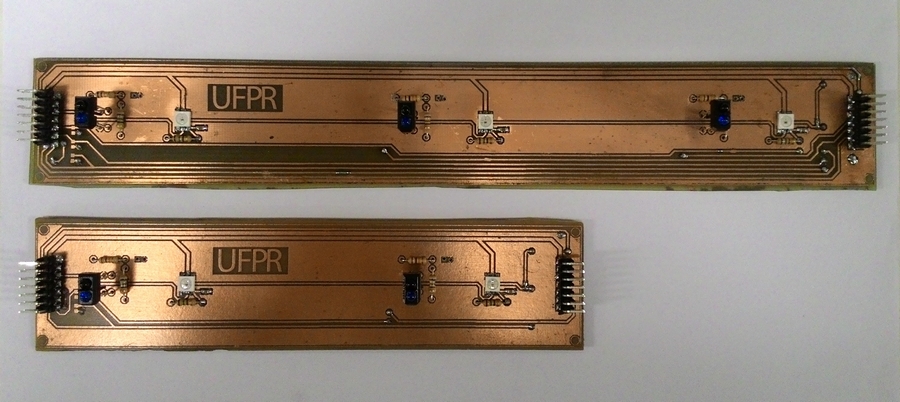
documentos/proposta/img/mesa-blocos.jpg
