wsilverio/tcc/documentos/proposta/img/mesa-conexao.jpg

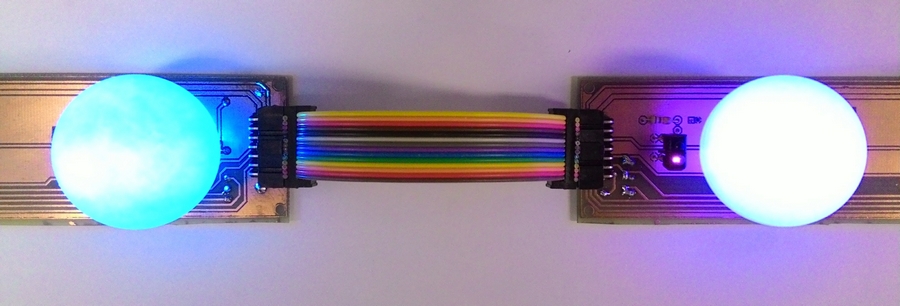
documentos/proposta/img/mesa-conexao.jpg
