wsilverio/tcc/documentos/tcc/dados/figuras/controlador-dir.jpeg

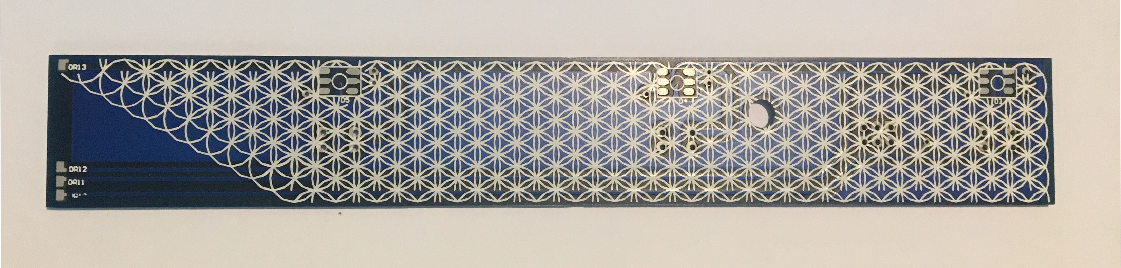
documentos/tcc/dados/figuras/controlador-dir.jpeg
