wsilverio/tcc/documentos/tcc/dados/figuras/controlador-esq.jpeg

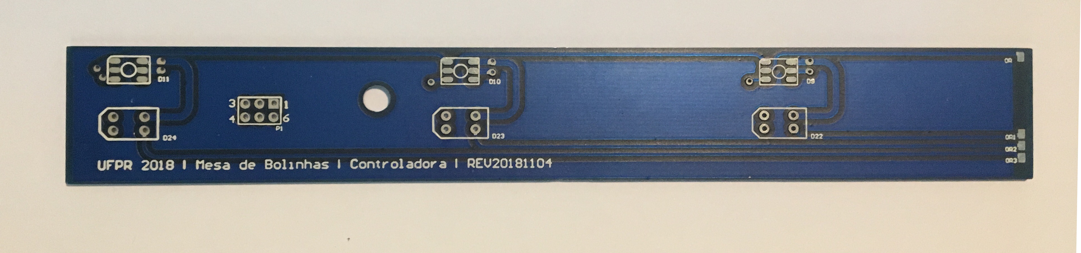
documentos/tcc/dados/figuras/controlador-esq.jpeg
