wsilverio/tcc/documentos/tcc/dados/figuras/pci-interface.jpeg

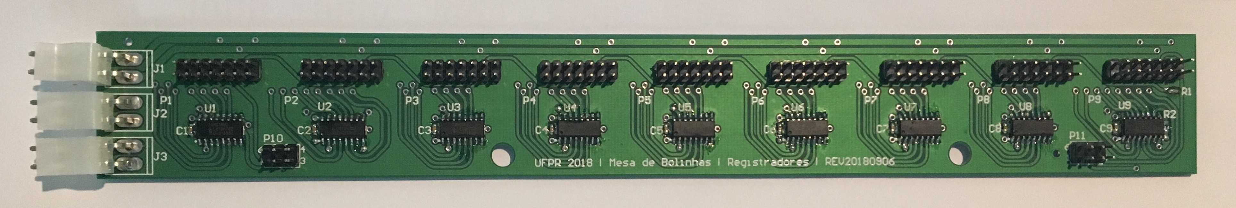
documentos/tcc/dados/figuras/pci-interface.jpeg
