wsilverio/tcc/hardware/registradores/docs/prints/conferencia-netlist.png

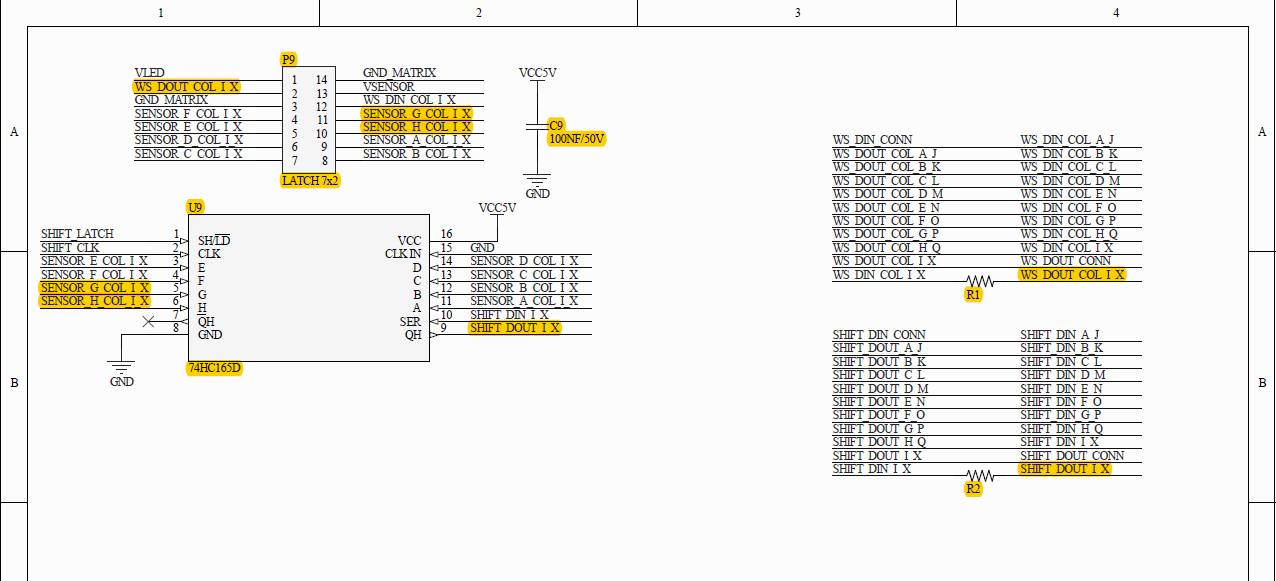
hardware/registradores/docs/prints/conferencia-netlist.png
