wsilverio/tcc/hardware/registradores/antigo/pdf/prototipo-eagle.pdf

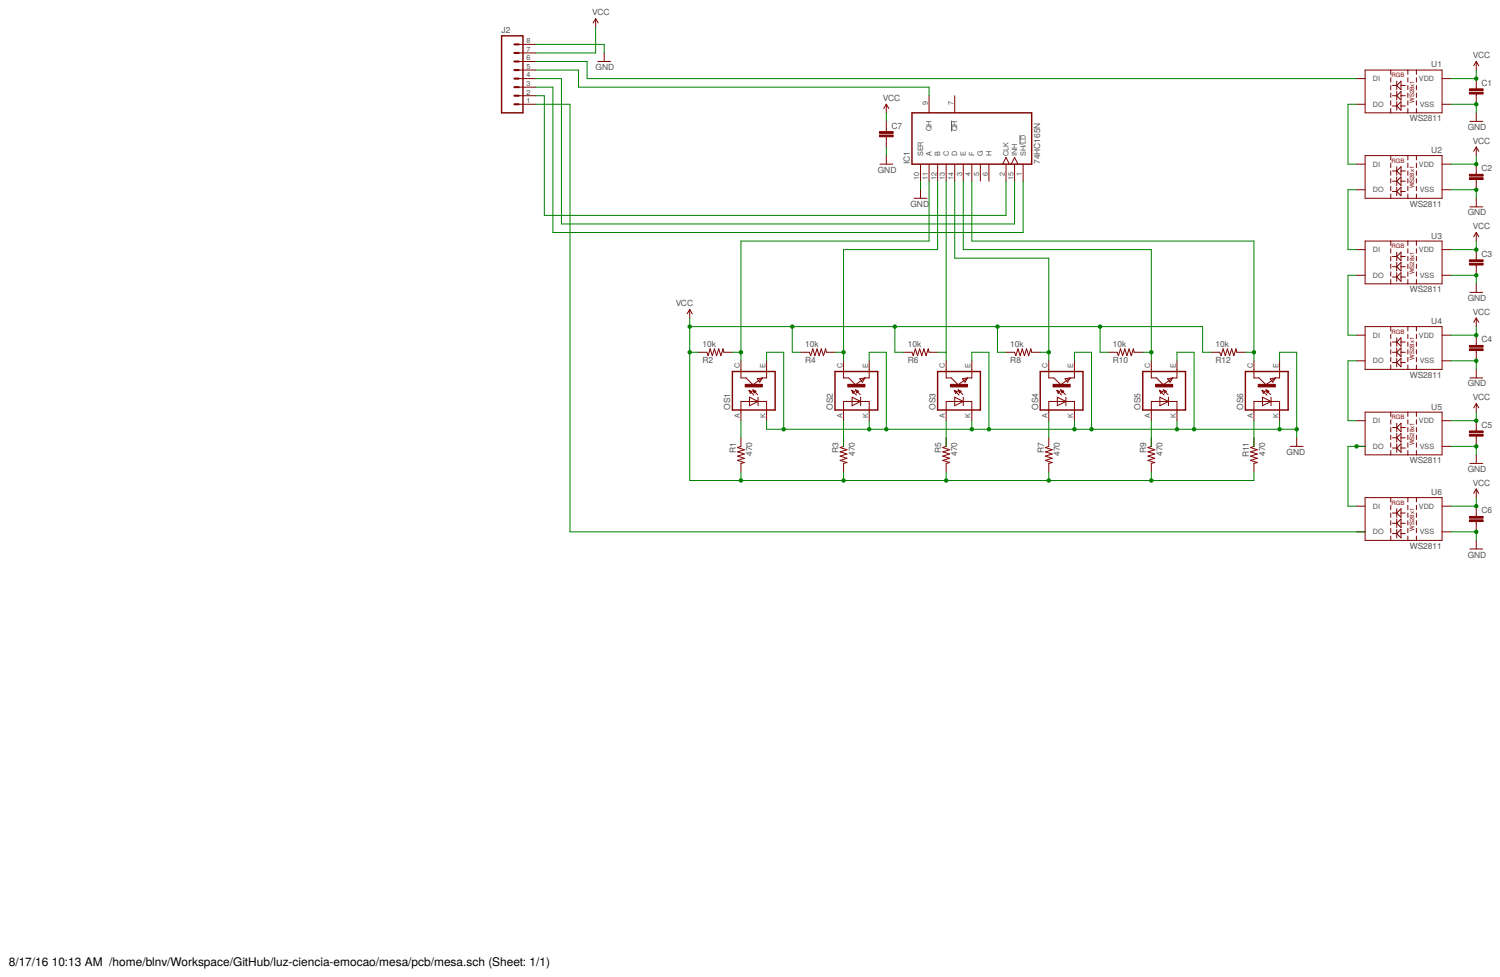
[picture p83: page 1]

RGB WS28x1 RGB WS28x1 RGB WS28x1
VDD

8/17/16 10:13 AM /home/blnv/Workspace/GitHub/luz-ciencia-emocao/mesa/pcb/mesa.sch (Sheet: 1/1)
