wsilverio/tcc/cad/mesa_placas.pdf

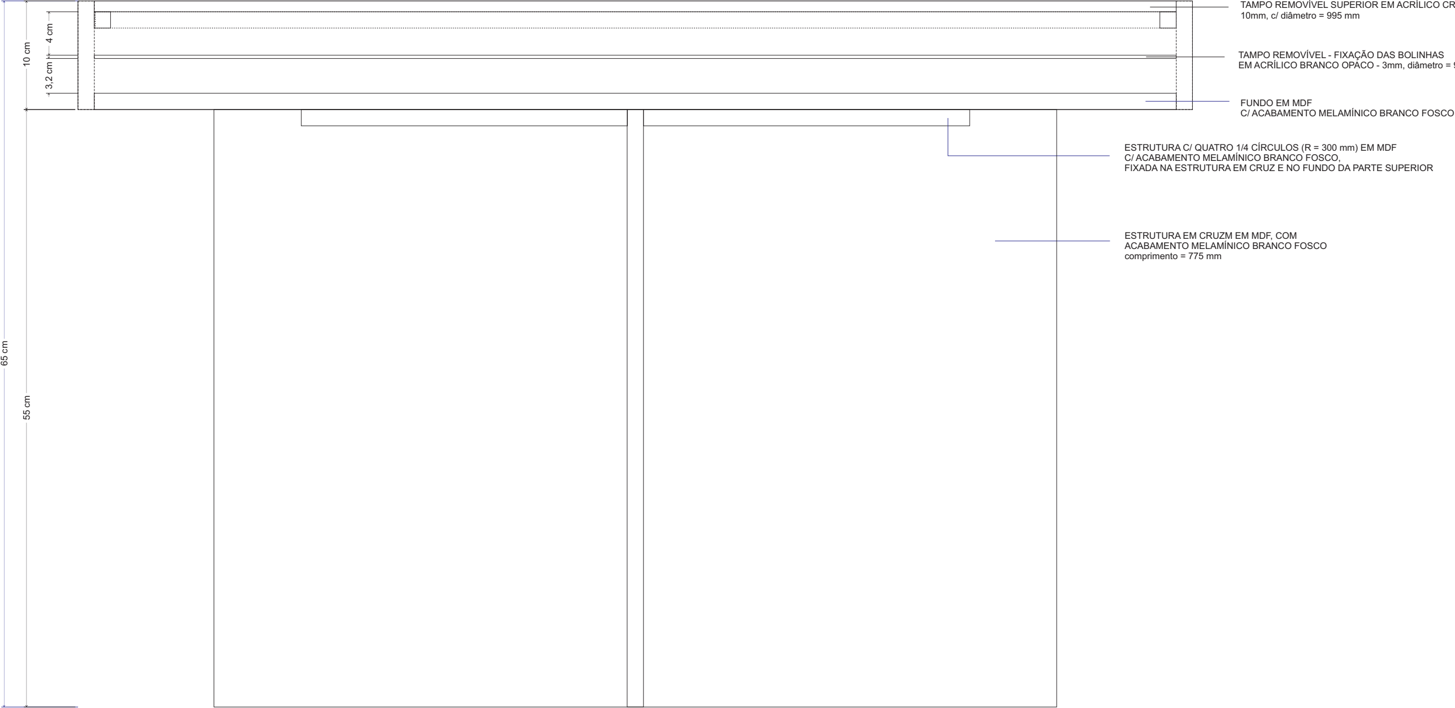
[picture p84: figure]
FUNDO EM MDF C/ ACABAMENTO MELAMÍNICO BRANCO FOSCO; C/ ACABAMENTO MELAMÍNICO BRANCO FOSCO,; ESTRUTURA EM CRUZM EM MDF, COM ACABAMENTO MELAMÍNICO BRANCO FOSCO comprimento = 775 mm; 10mm, c/ diâmetro = 995 mm; TAMPO REMOVÍVEL - FIXAÇÃO DAS BOLINHAS
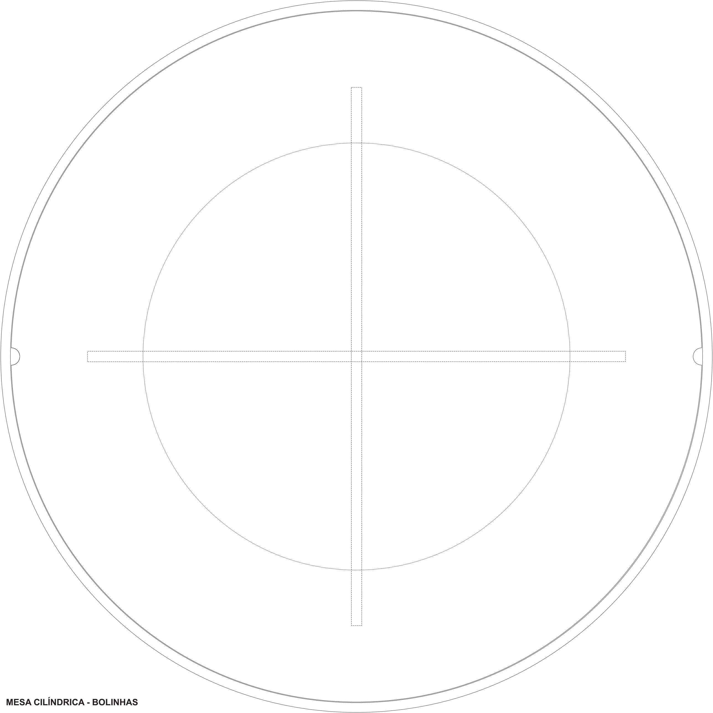
[picture p85: figure]
MESA CILÍNDRICA - BOLINHAS

quantidade = 1

Obs.:
1) Sem cantos vivos (raios não especificados = 1mm)
2) Desenho esquemático. VERIFICAR ESTRUTURA E DETALHES DE ENCAIXES E FIXAÇÕES.

ESTRUTURA C/ QUATRO 1/4 CÍRCULOS (R = 300 mm) EM MDF

FIXADA NA ESTRUTURA EM CRUZ E NO FUNDO DA PARTE SUPERIOR

TAMPO REMOVÍVEL SUPERIOR EM ACRÍLICO CRISTAL

EM ACRÍLICO BRANCO OPACO - 3mm, diâmetro = 995 mm

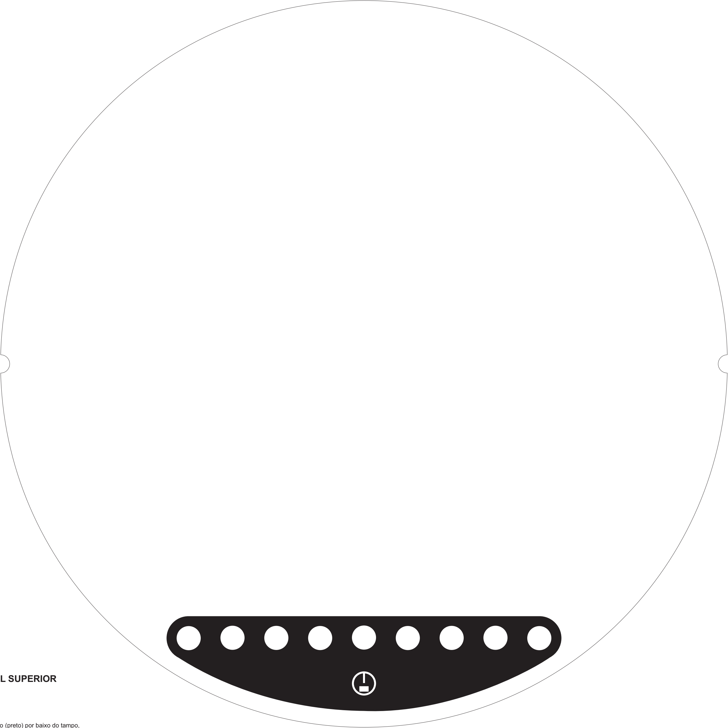
[picture p86: figure]

## TAMPO REMOVÍVEL SUPERIOR

escala = 1:1
acrílico cristal - 10 mm
diâmetro do tampo = 99,5 cm

Aplicação localizada de adesivo (preto) por baixo do tampo,
com recortes (áreas transparentes, indicadas em branco no desenho)

quantidade = 1

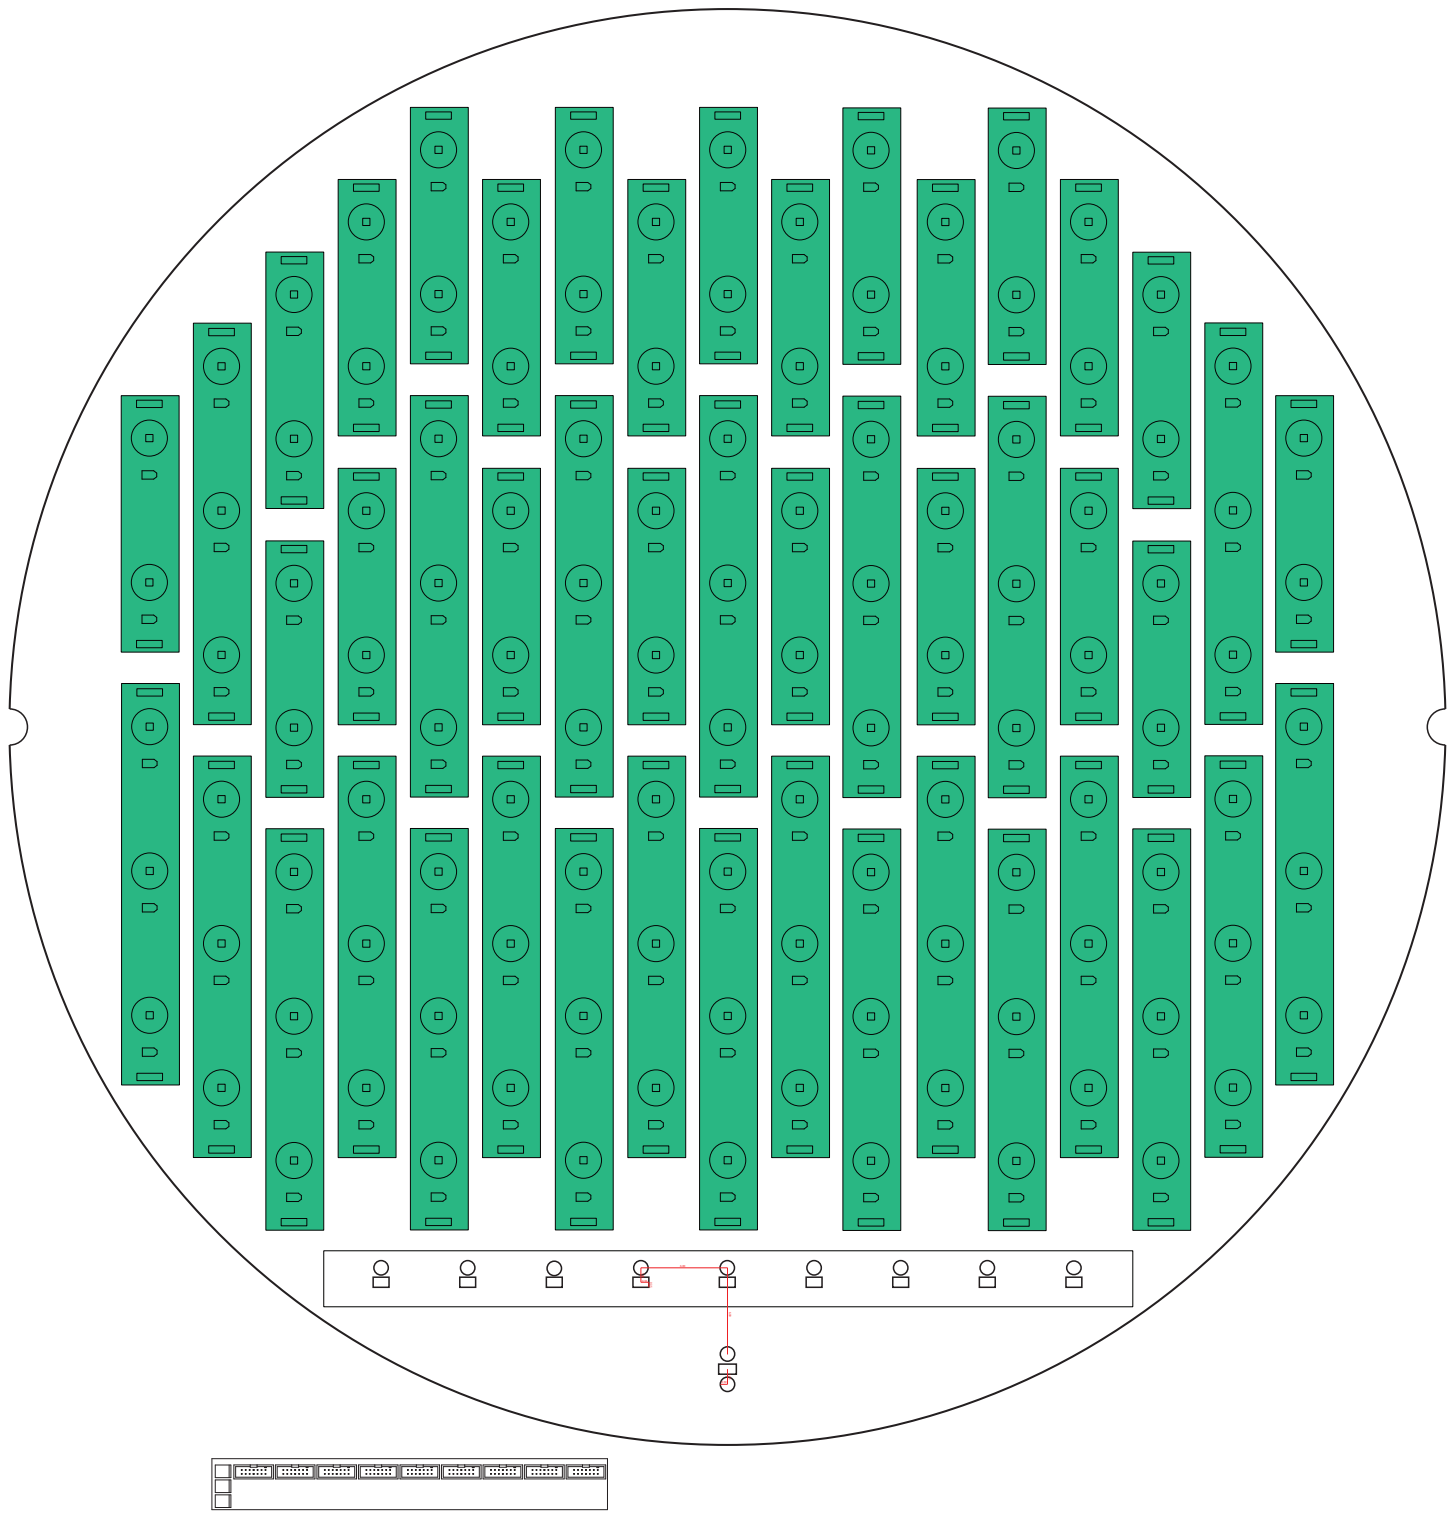
[picture p87: page 3]

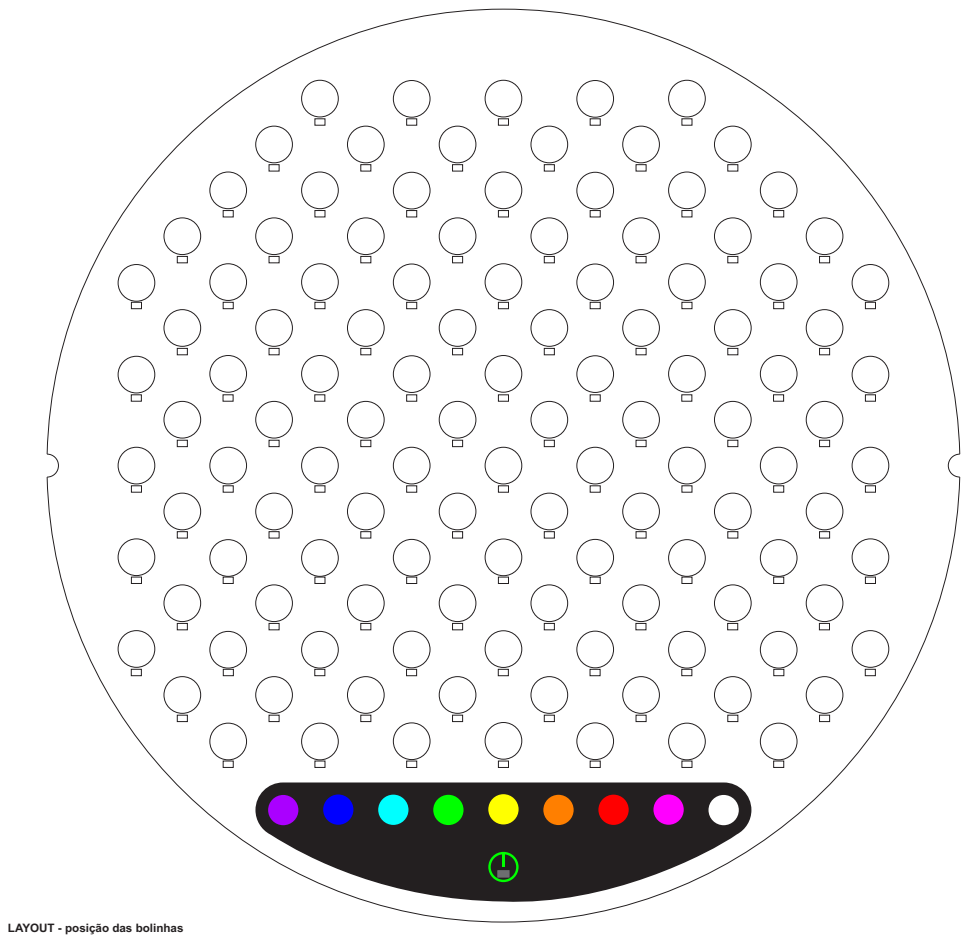
[picture p88: page 4]

LAYOUT - posição das bolinhas
