wsilverio/tcc/cad/mesa_de_bolinhas_final.pdf

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
MESA CILÍNDRICA - BOLINHAS

quantidade = 1

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

ESTRUTURA C/ QUATRO 1/4 CÍRCULOS (R = 300 mm) EM MDF

FIXADA NA ESTRUTURA EM CRUZ E NO FUNDO DA PARTE SUPERIOR

TAMPO REMOVÍVEL SUPERIOR EM ACRÍLICO CRISTAL

EM ACRÍLICO BRANCO OPACO - 3mm, diâmetro = 995 mm


## TAMPO REMOVÍVEL SUPERIOR

escala = 1:1
acrílico cristal - 10 mm
diâmetro do tampo = 99,5 cm

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

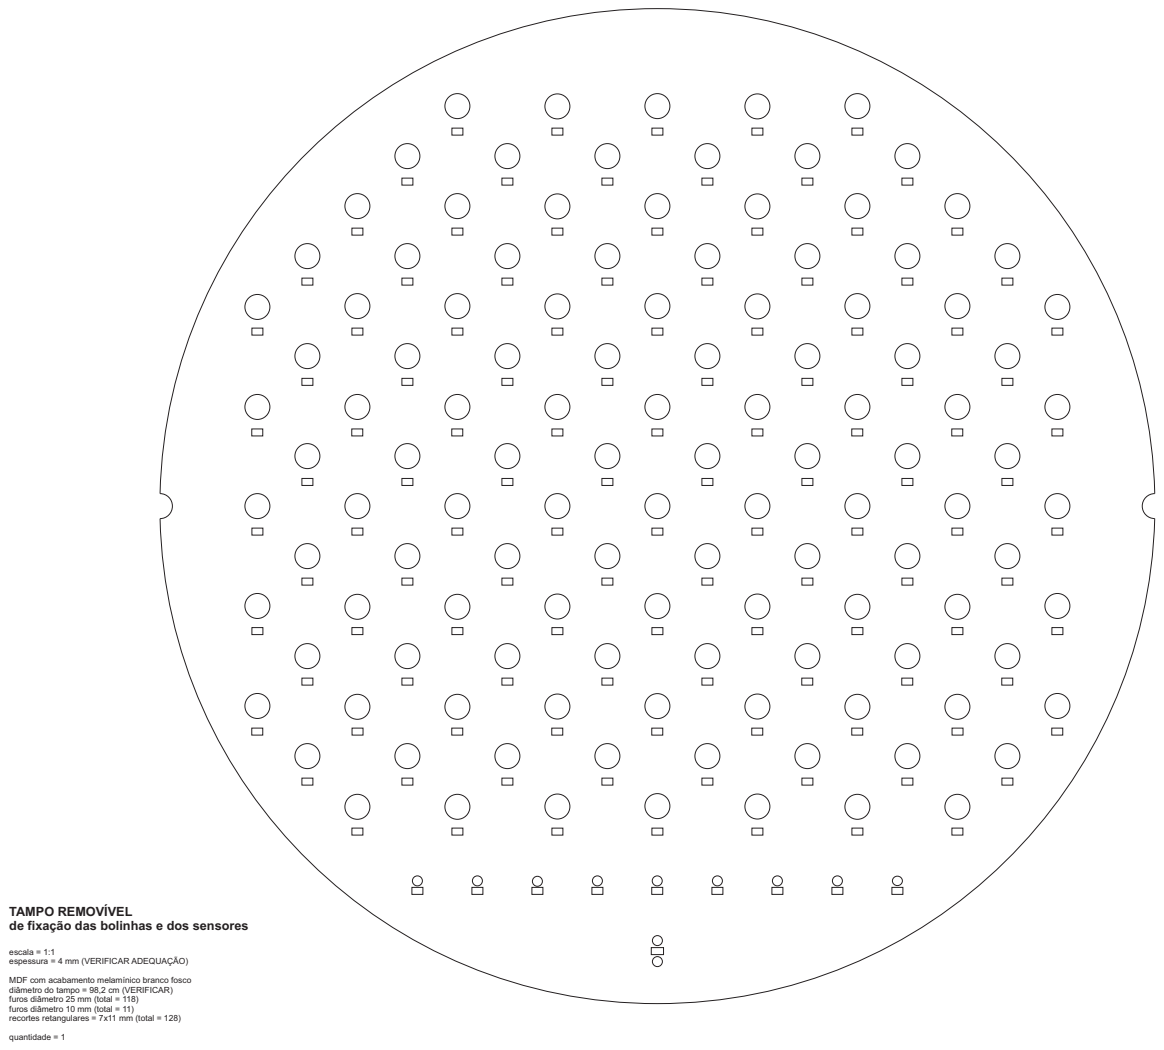
[picture p89: page 3]

TAMPO REMOVÍVEL
de fixação das bolinhas e dos sensores

escala = 1:1
espessura = 4 mm (VERIFICAR ADEQUAÇÃO)

MDF com acabamento melamínico branco fosco
diâmetro do tampo = 98,2 cm (VERIFICAR)
furos diâmetro 25 mm (total = 118)
furos diâmetro 10 mm (total = 11)
recortes retangulares = 7x11 mm (total = 128)


LAYOUT - posição das bolinhas
