wsilverio/tcc/hardware/mesa-bloco-2/pdf/pcb-mesa-2-top-prototipo.PDF

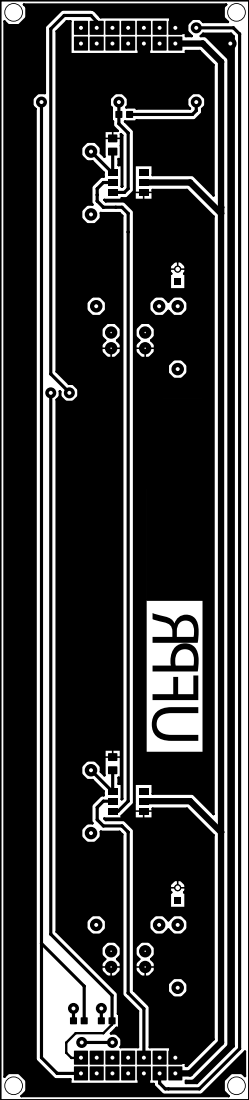
[picture p111: page 1]
