wsilverio/tcc/hardware/mesa-bloco-2/pdf/pcb-mesa-bloco-2-layers.PDF

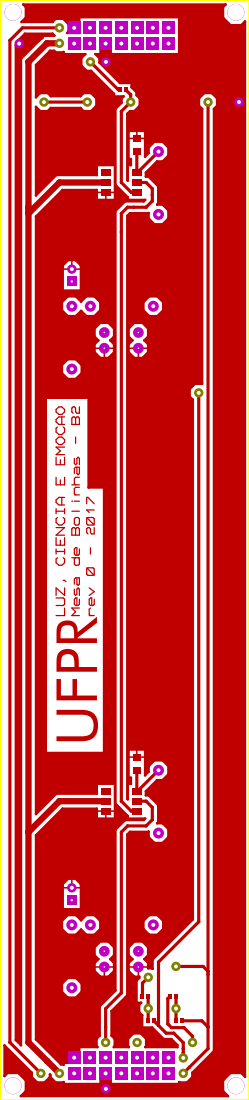
[picture p112: page 1]

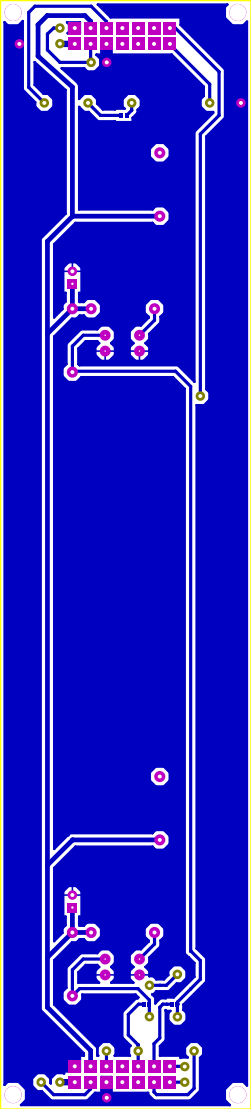
[picture p113: page 2]

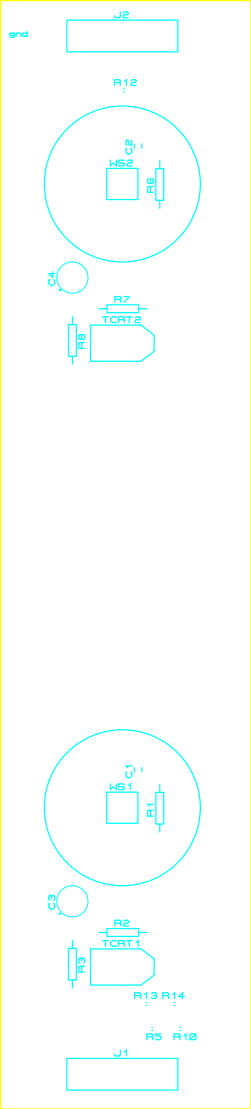
[picture p114: page 3]

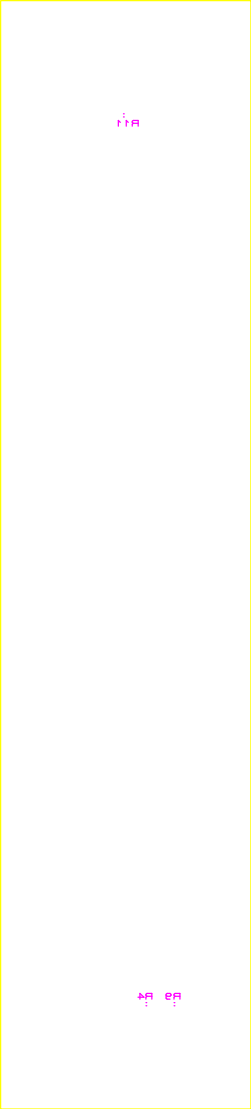
[picture p115: page 4]

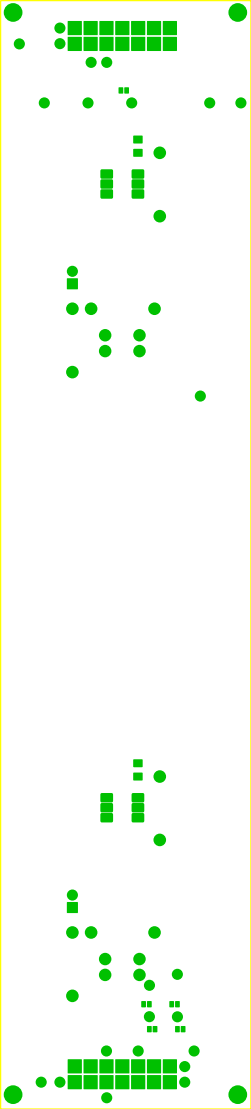
[picture p116: page 5]

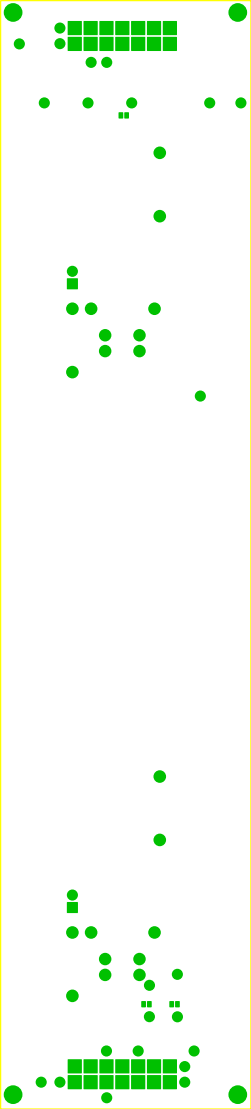
[picture p117: page 6]

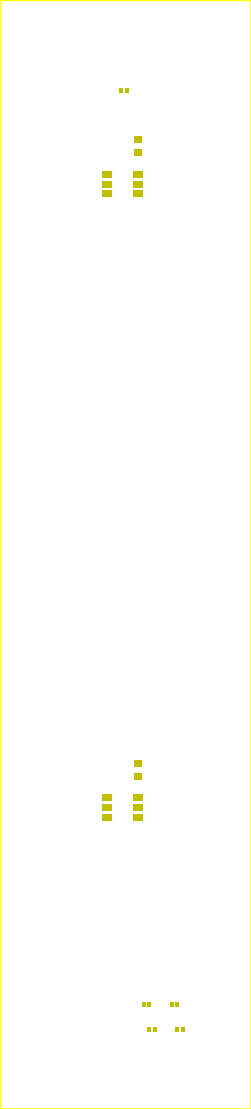
[picture p118: page 7]

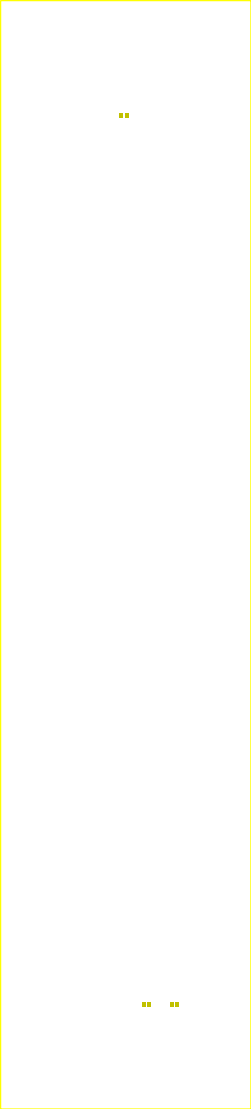
[picture p119: page 8]
