wsilverio/tcc/hardware/mesa-bloco-2/pdf/print-mesa-2.pdf

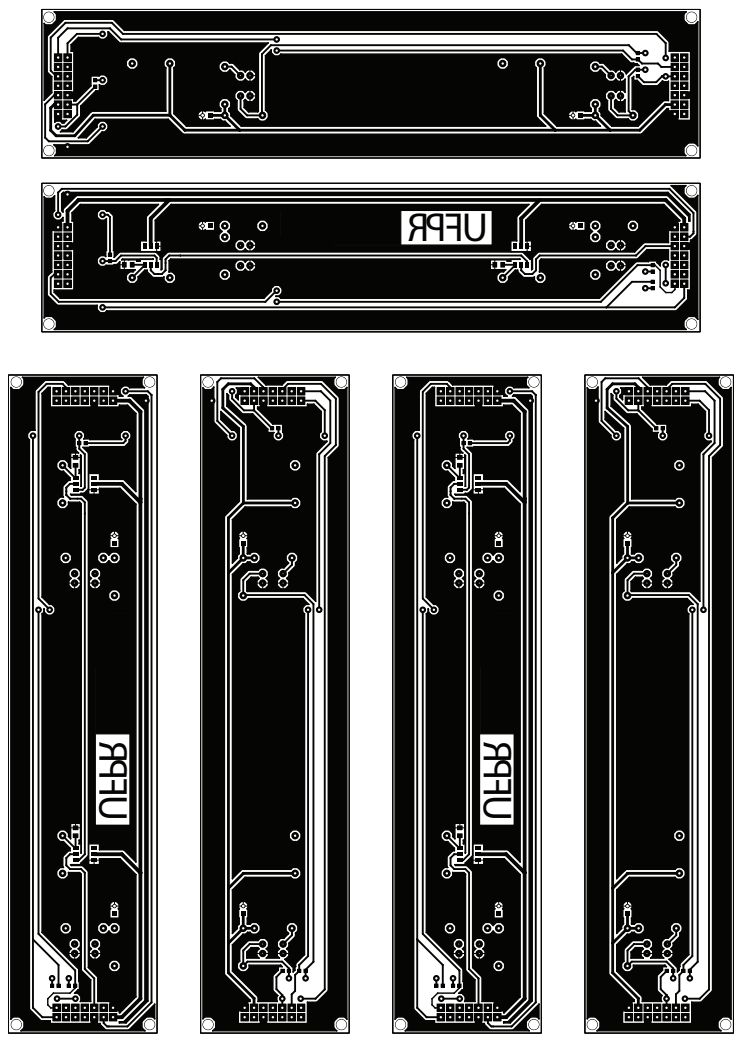
[picture p120: page 1]
