wsilverio/tcc/hardware/mesa-bloco-2/pdf/sch-mesa-bloco-2.PDF

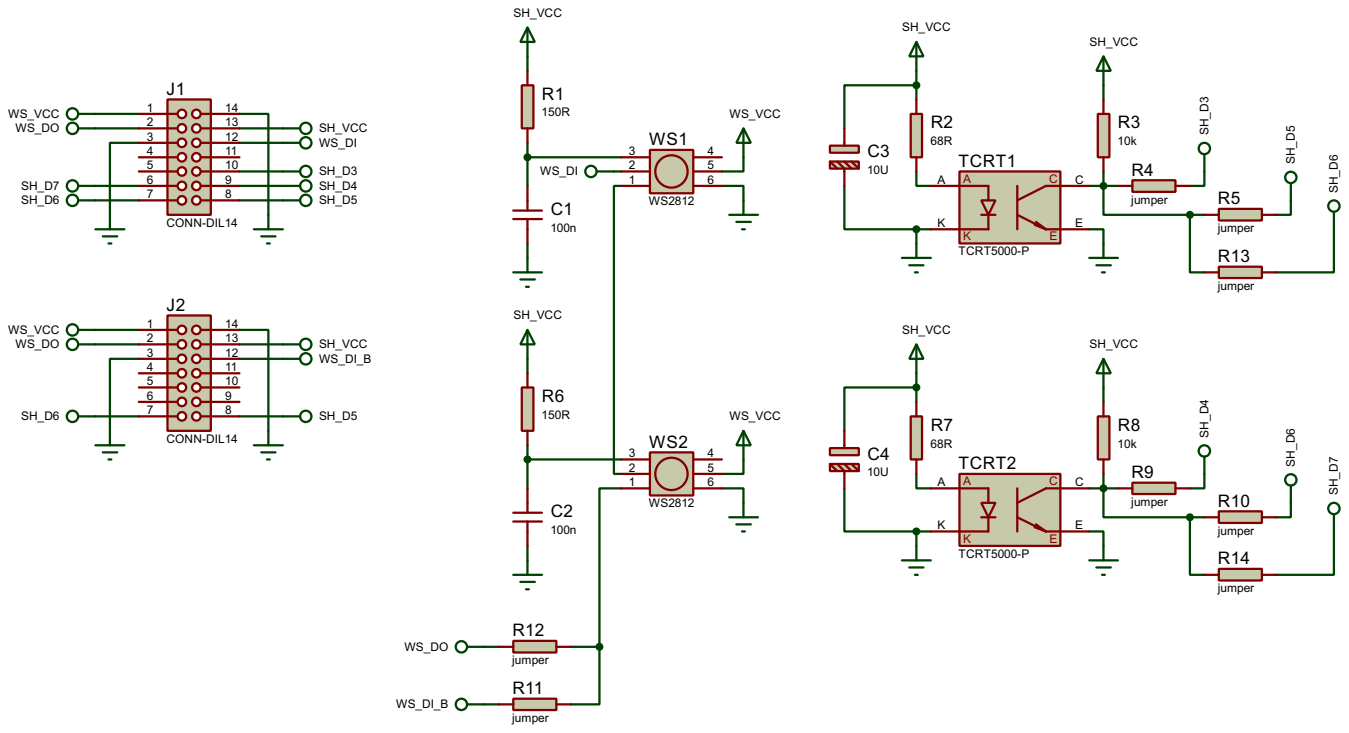
[picture p121: page 1]
