wsilverio/tcc/hardware/mesa-bloco-3/pdf/pcb-mesa-3-bottom-prototipo.PDF

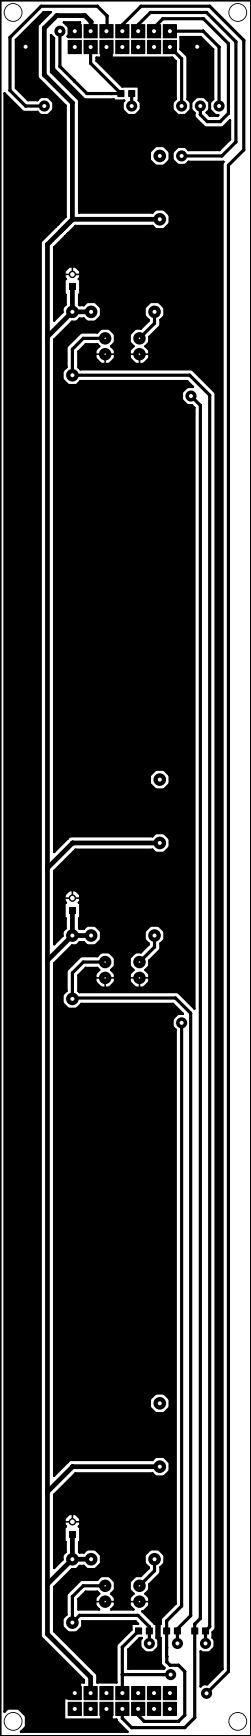
[picture p122: page 1]
