wsilverio/tcc/hardware/mesa-bloco-3/pdf/pcb-mesa-bloco-3-com-borda-tcr-distancias.pdf

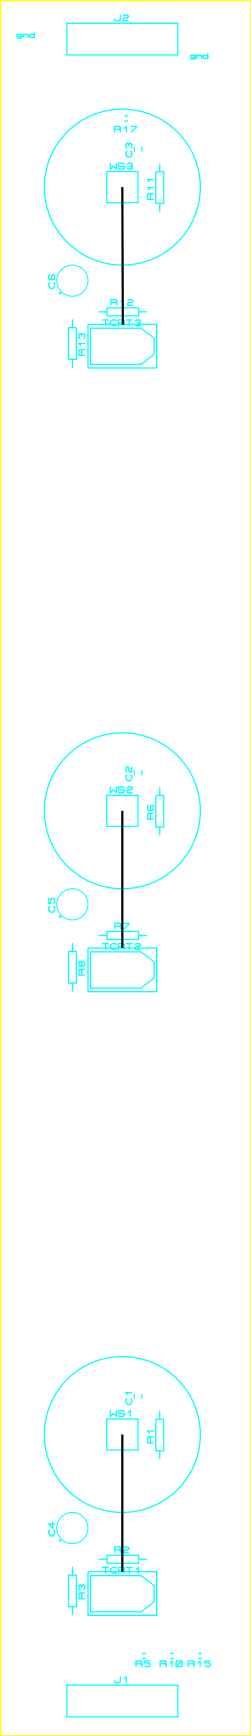
[picture p123: page 1]
