wsilverio/tcc/hardware/mesa-bloco-3/pdf/pcb-mesa-bloco-3-com-borda-tcr.PDF

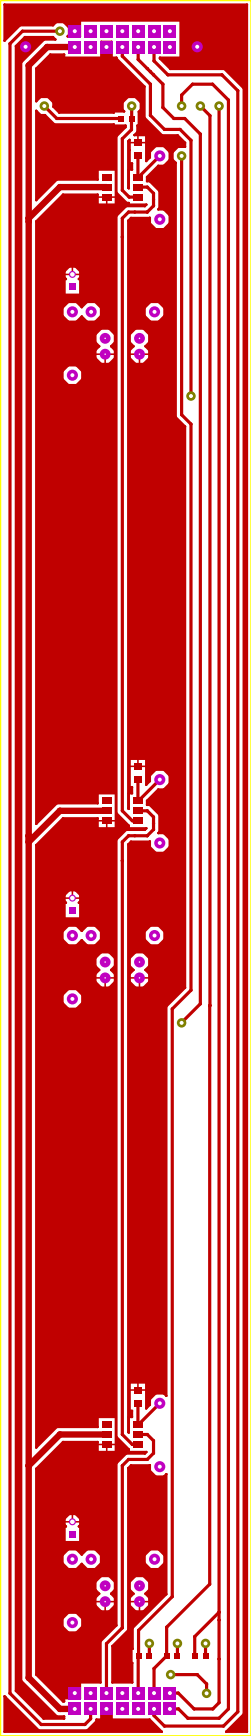
[picture p124: page 1]

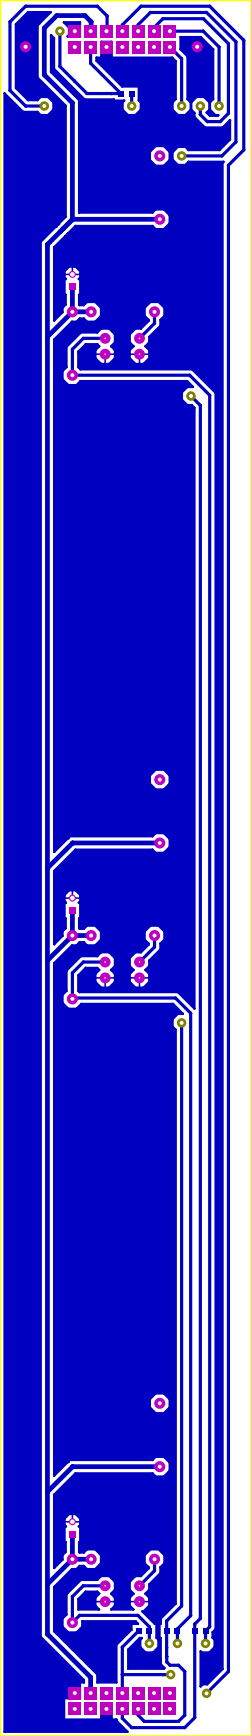
[picture p125: page 2]

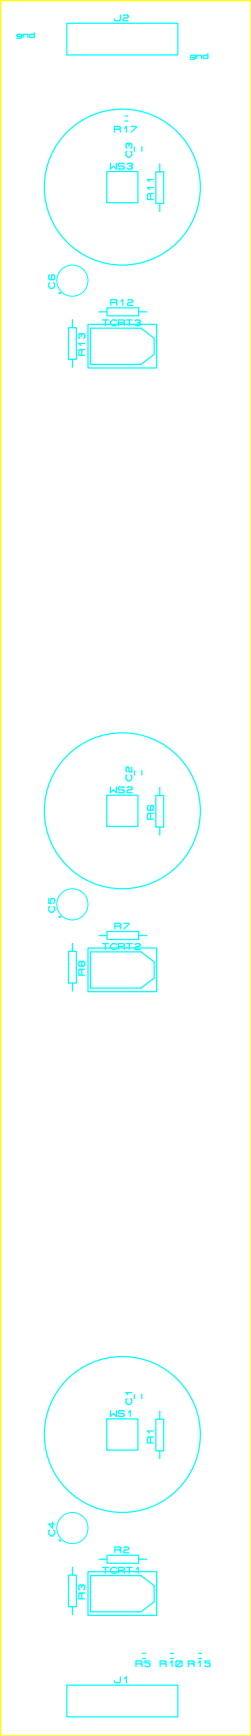
[picture p126: page 3]

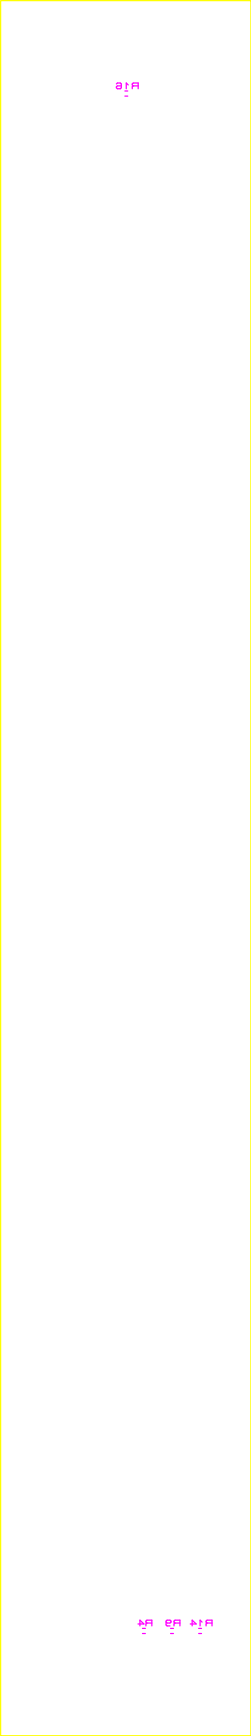
[picture p127: page 4]

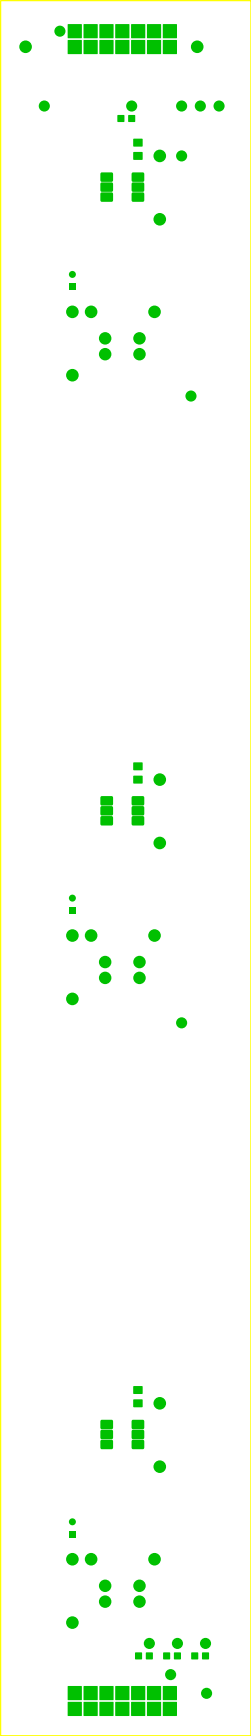
[picture p128: page 5]

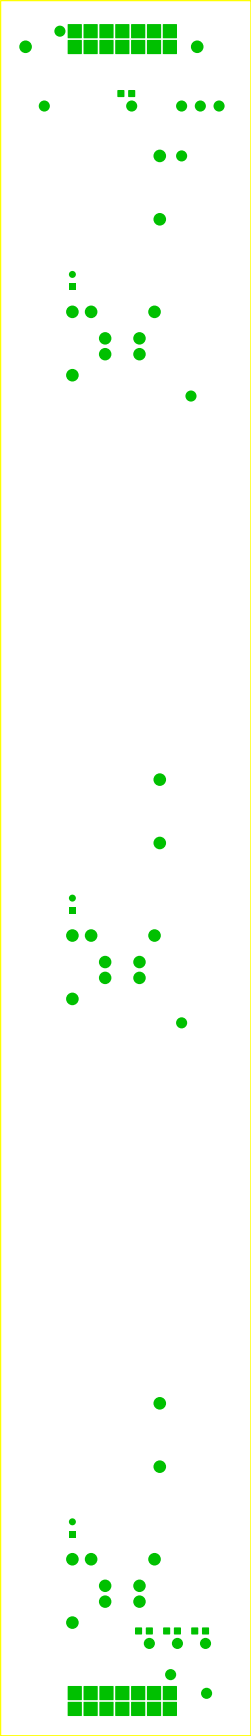
[picture p129: page 6]

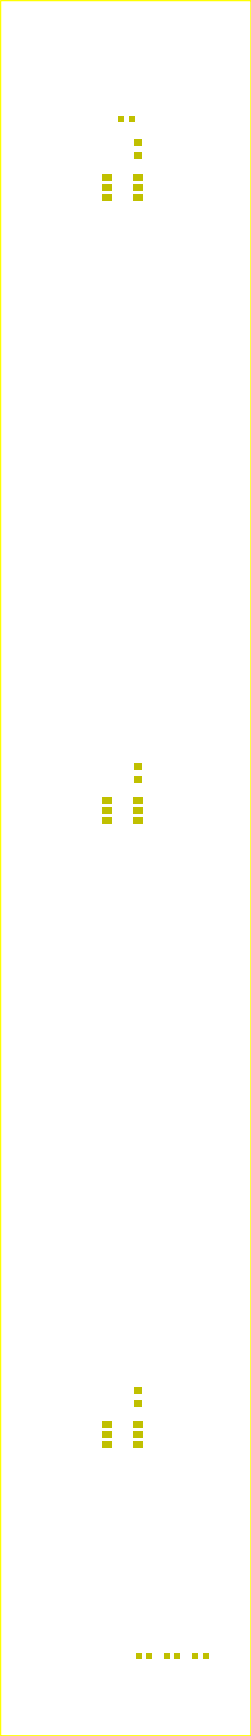
[picture p130: page 7]

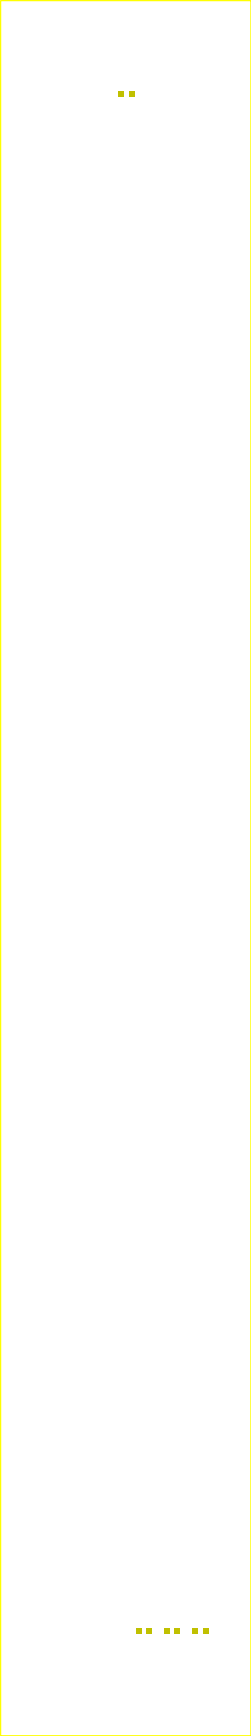
[picture p131: page 8]
