wsilverio/tcc/hardware/mesa-bloco-3/pdf/pcb-mesa-bloco-3-layers.PDF

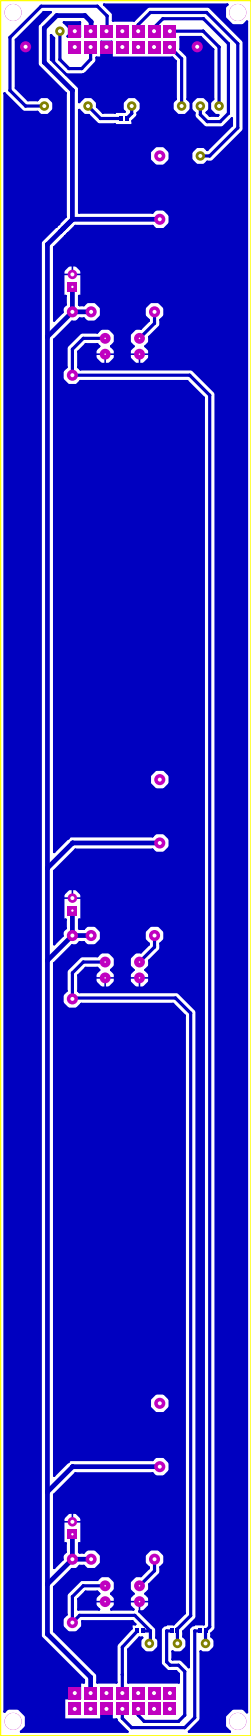
[picture p132: page 2]

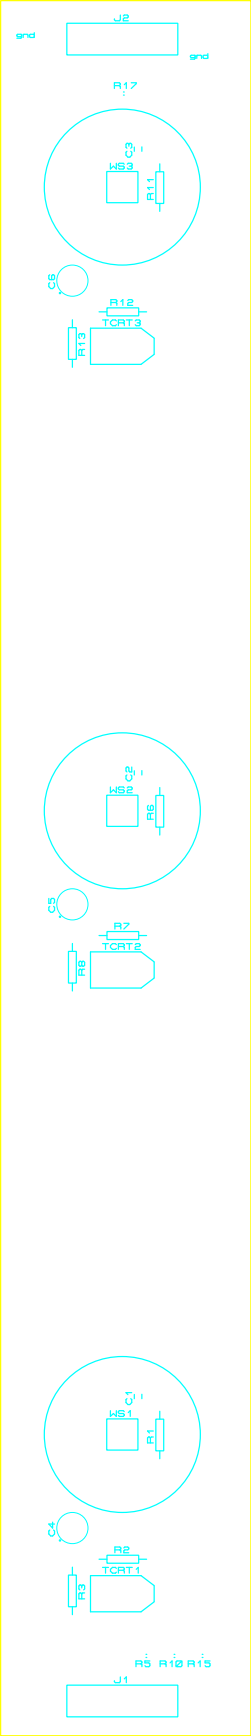
[picture p133: page 3]

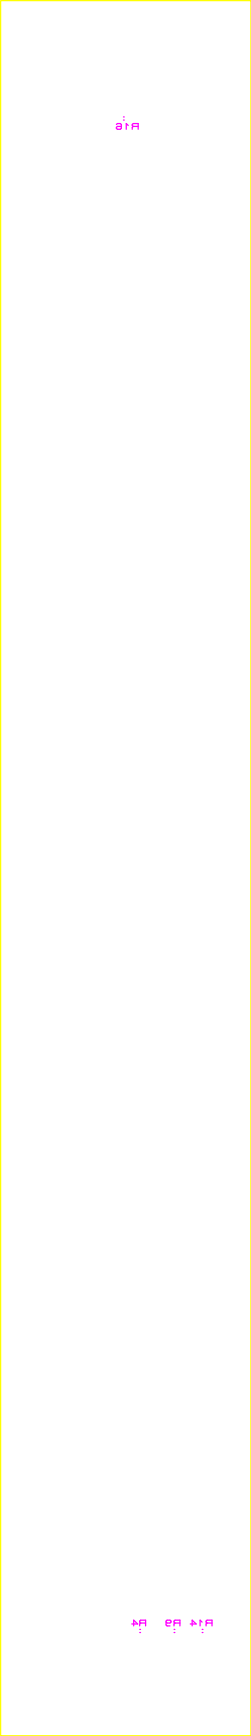
[picture p134: page 4]

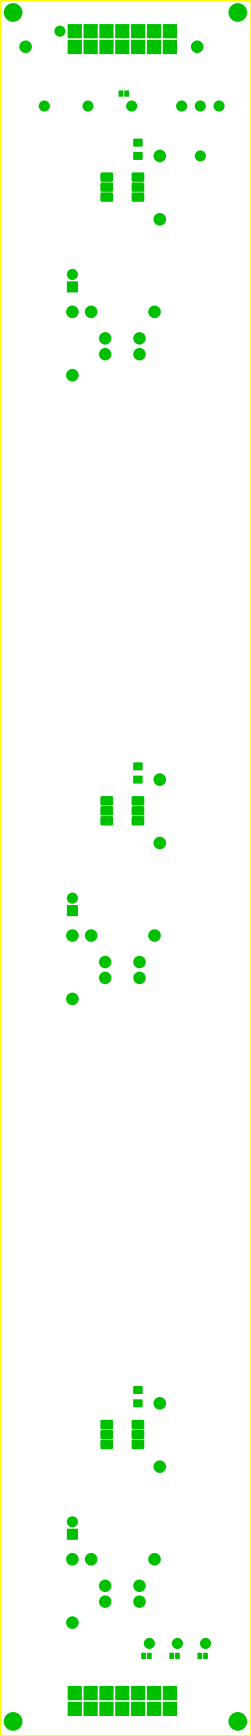
[picture p135: page 5]

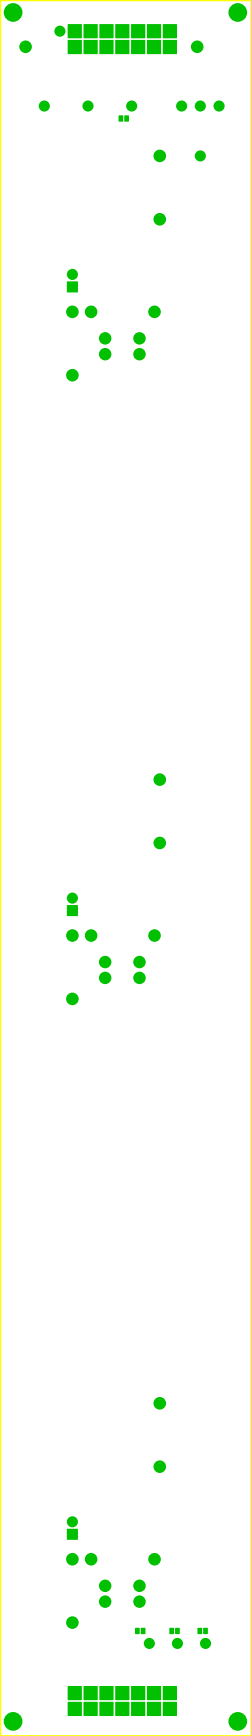
[picture p136: page 6]

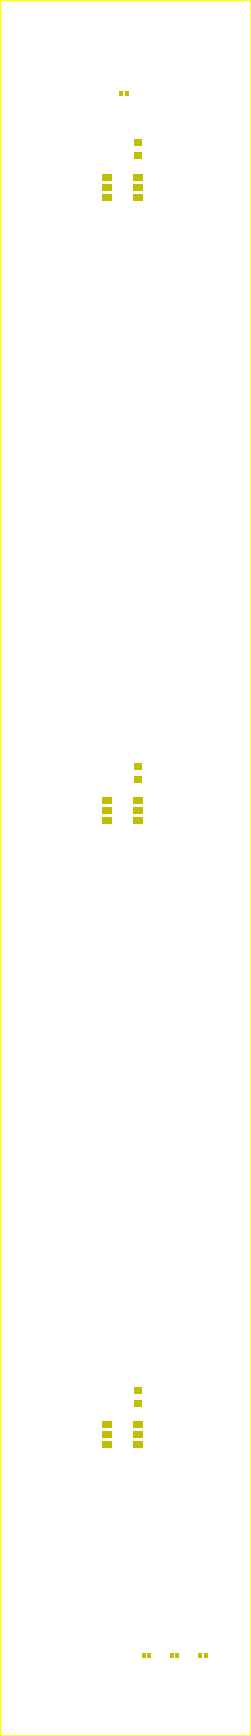
[picture p137: page 7]

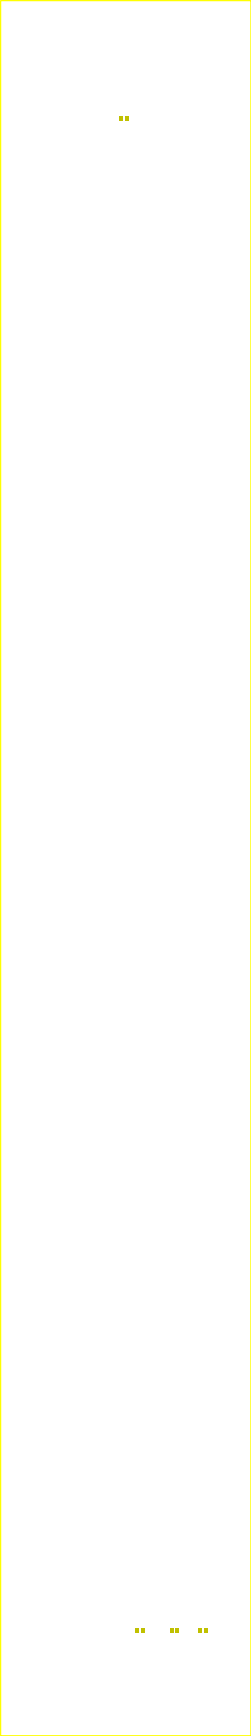
[picture p138: page 8]
