wsilverio/tcc/hardware/mesa-bloco-3/pdf/print-mesa-3-prototipo.pdf

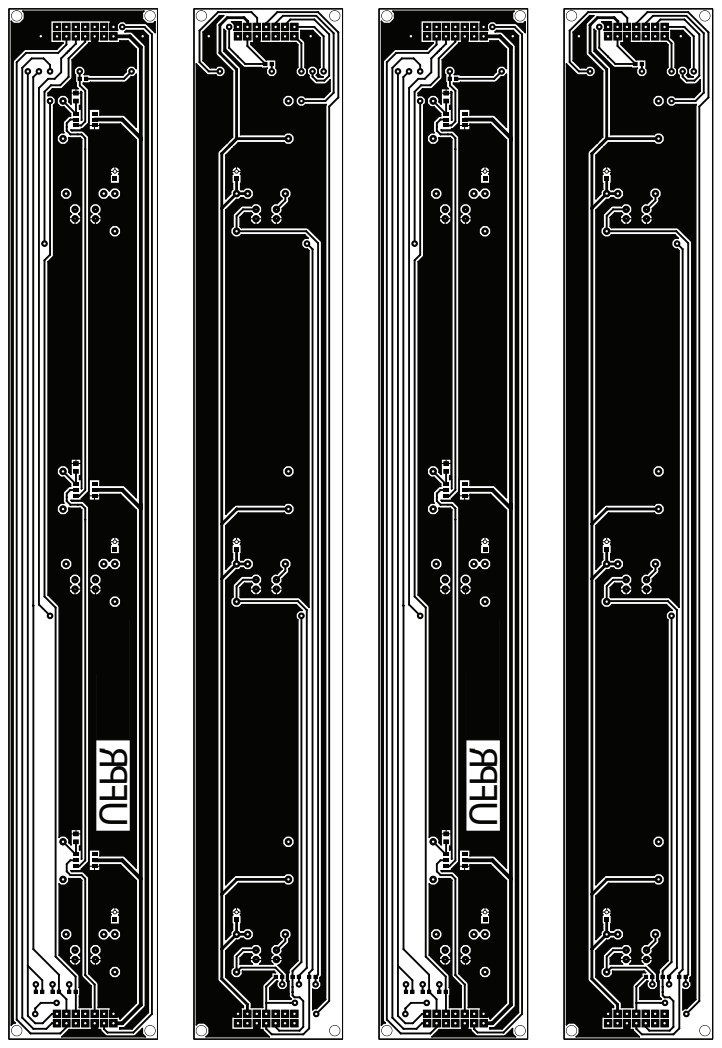
[picture p139: page 1]
UFPR
