wsilverio/tcc/hardware/mesa-bloco-3/pdf/sch-mesa-bloco-3.PDF

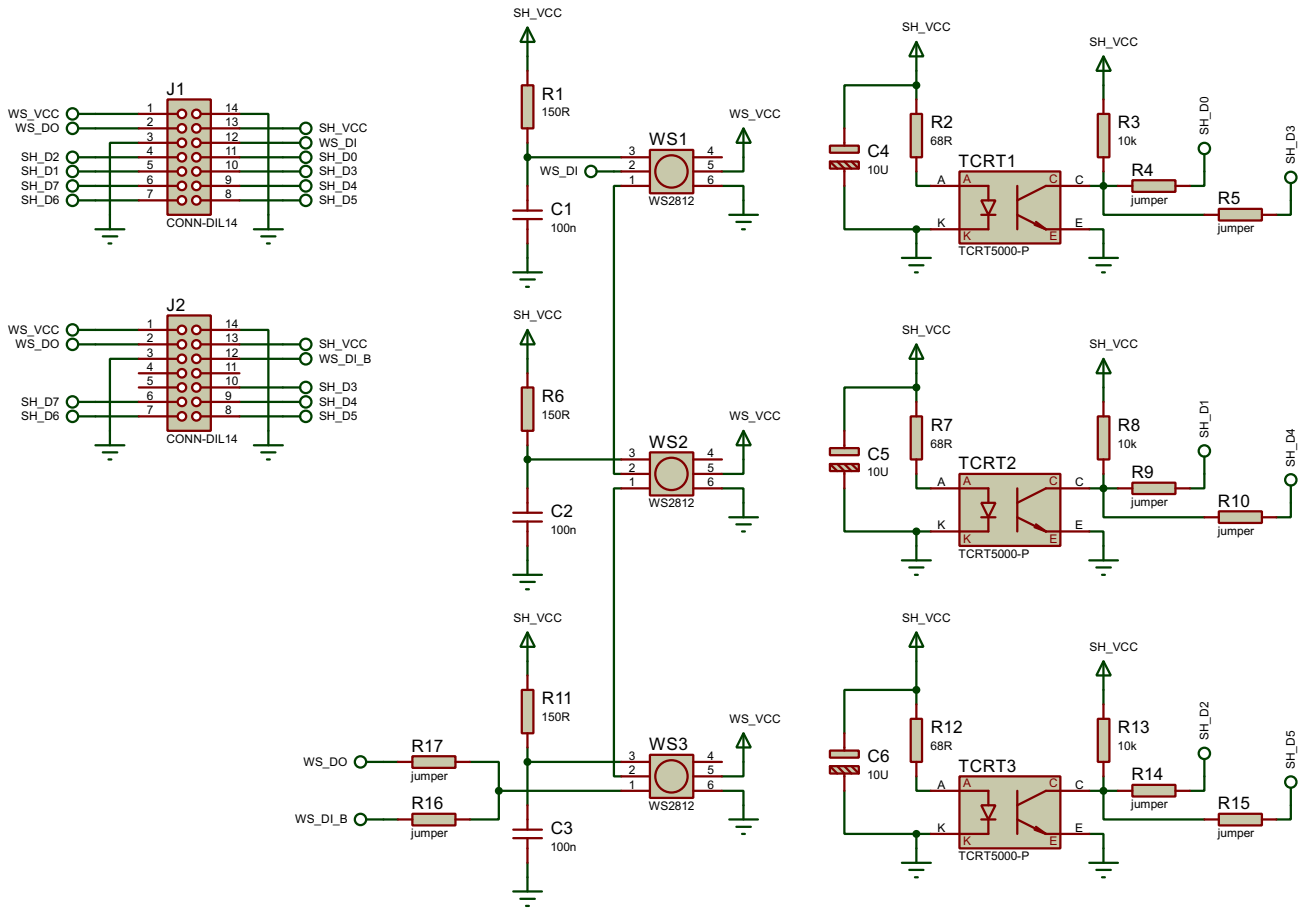
[picture p140: page 1]
