wsilverio/tcc/hardware/registradores/docs/netlist/registradores.pdf

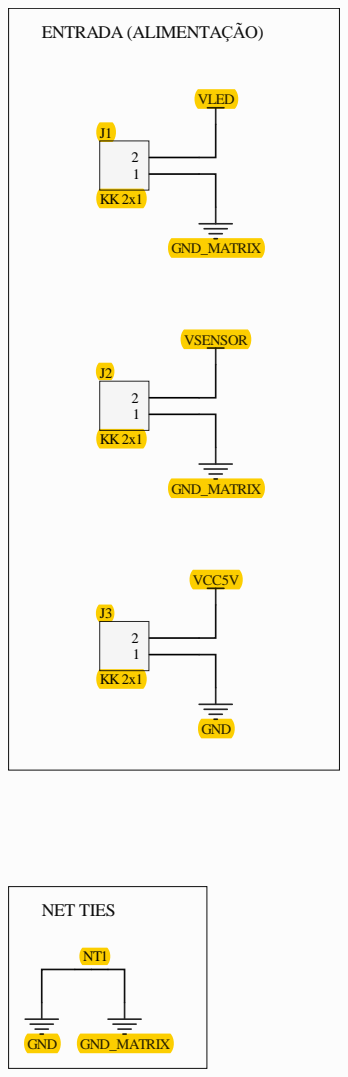
[picture p141: page 1]

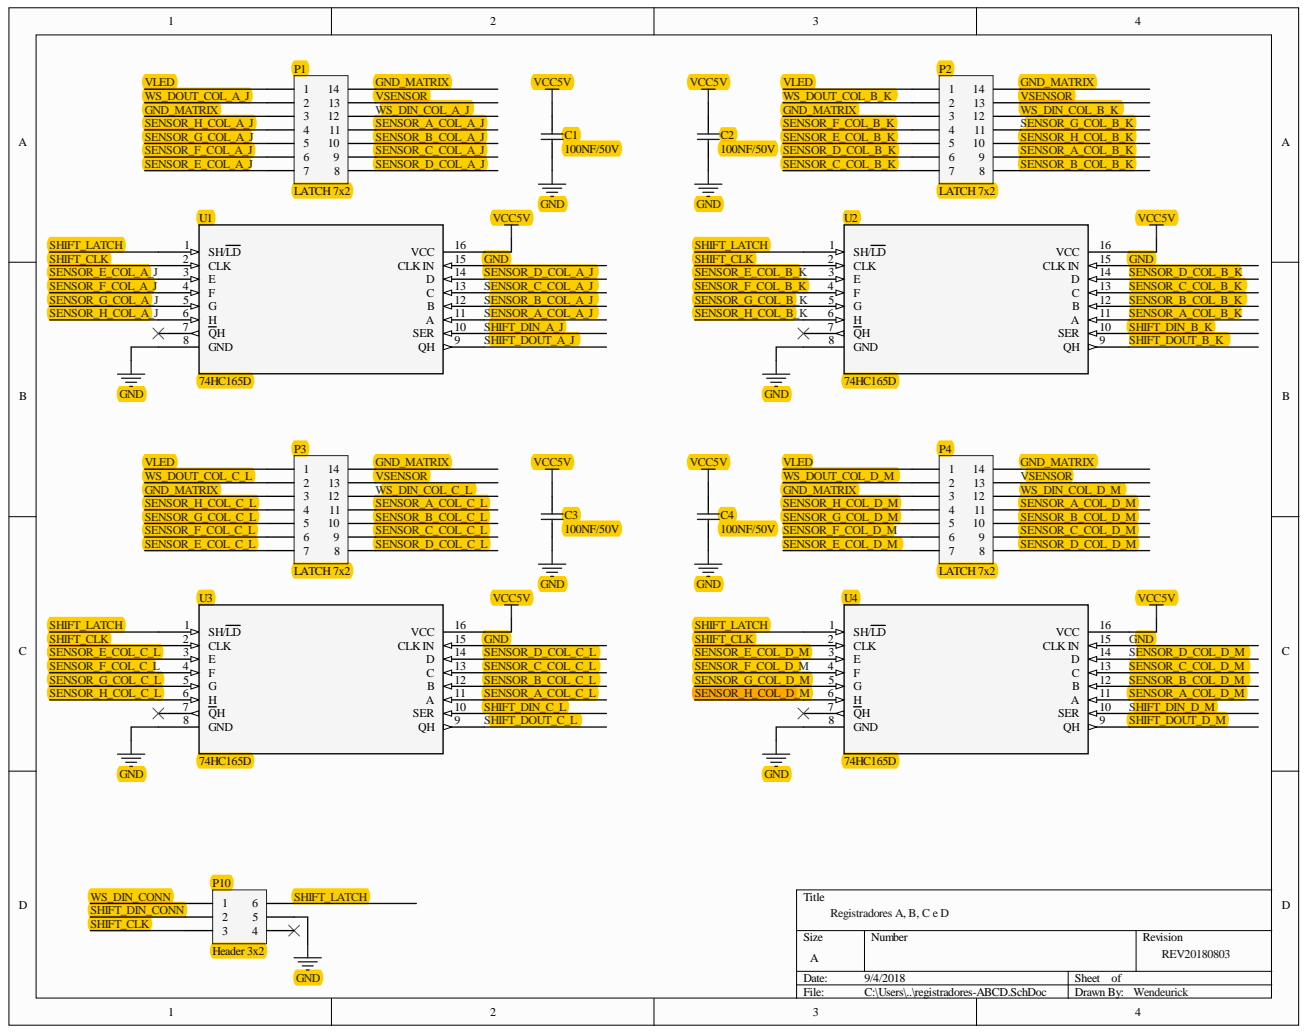
[picture p142: page 2]

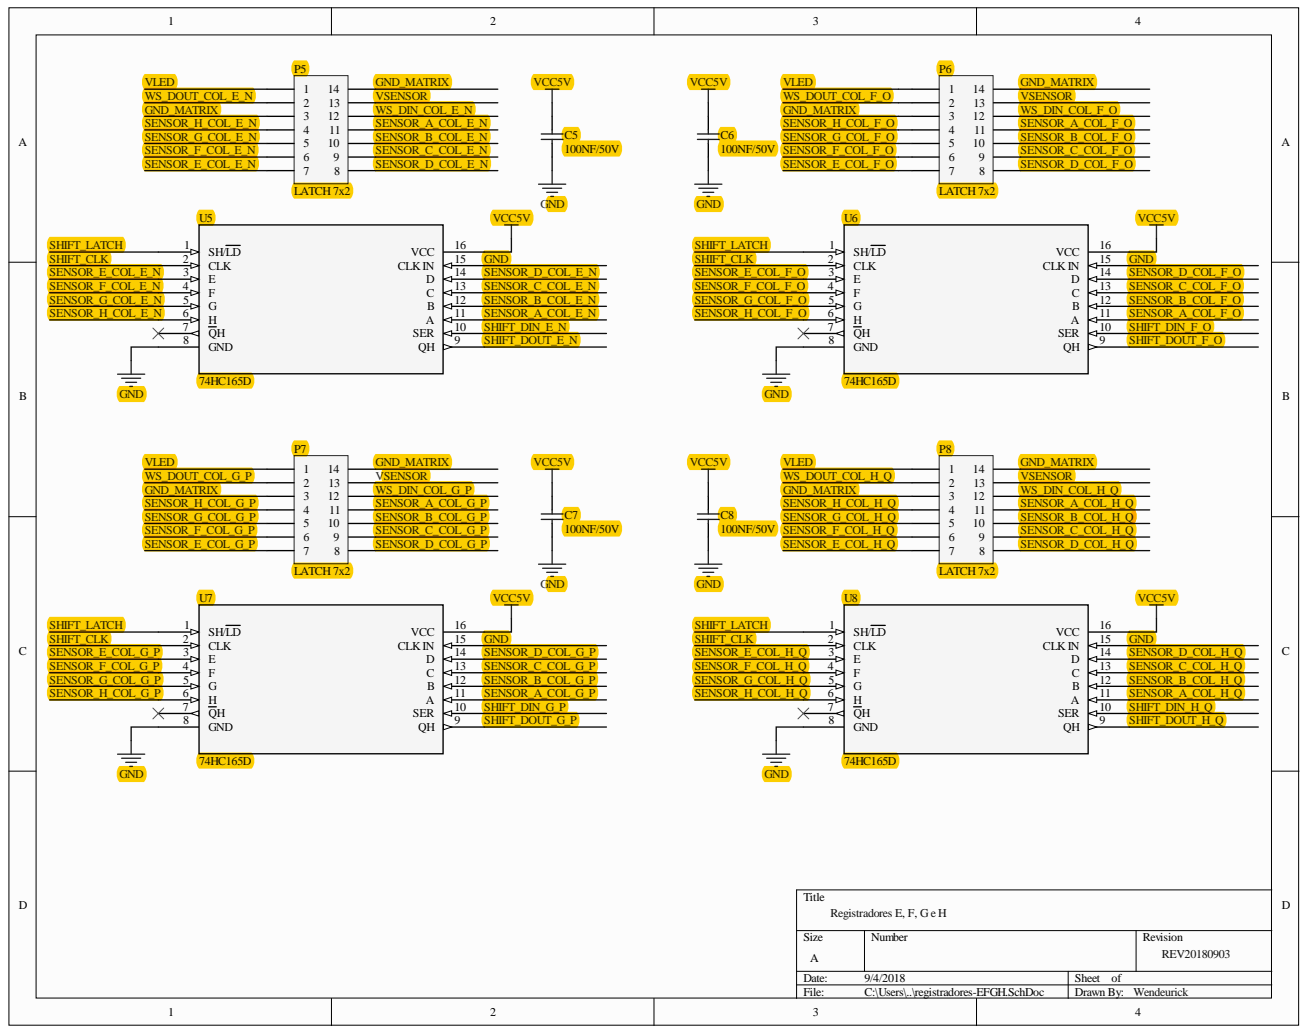
[picture p143: page 3]

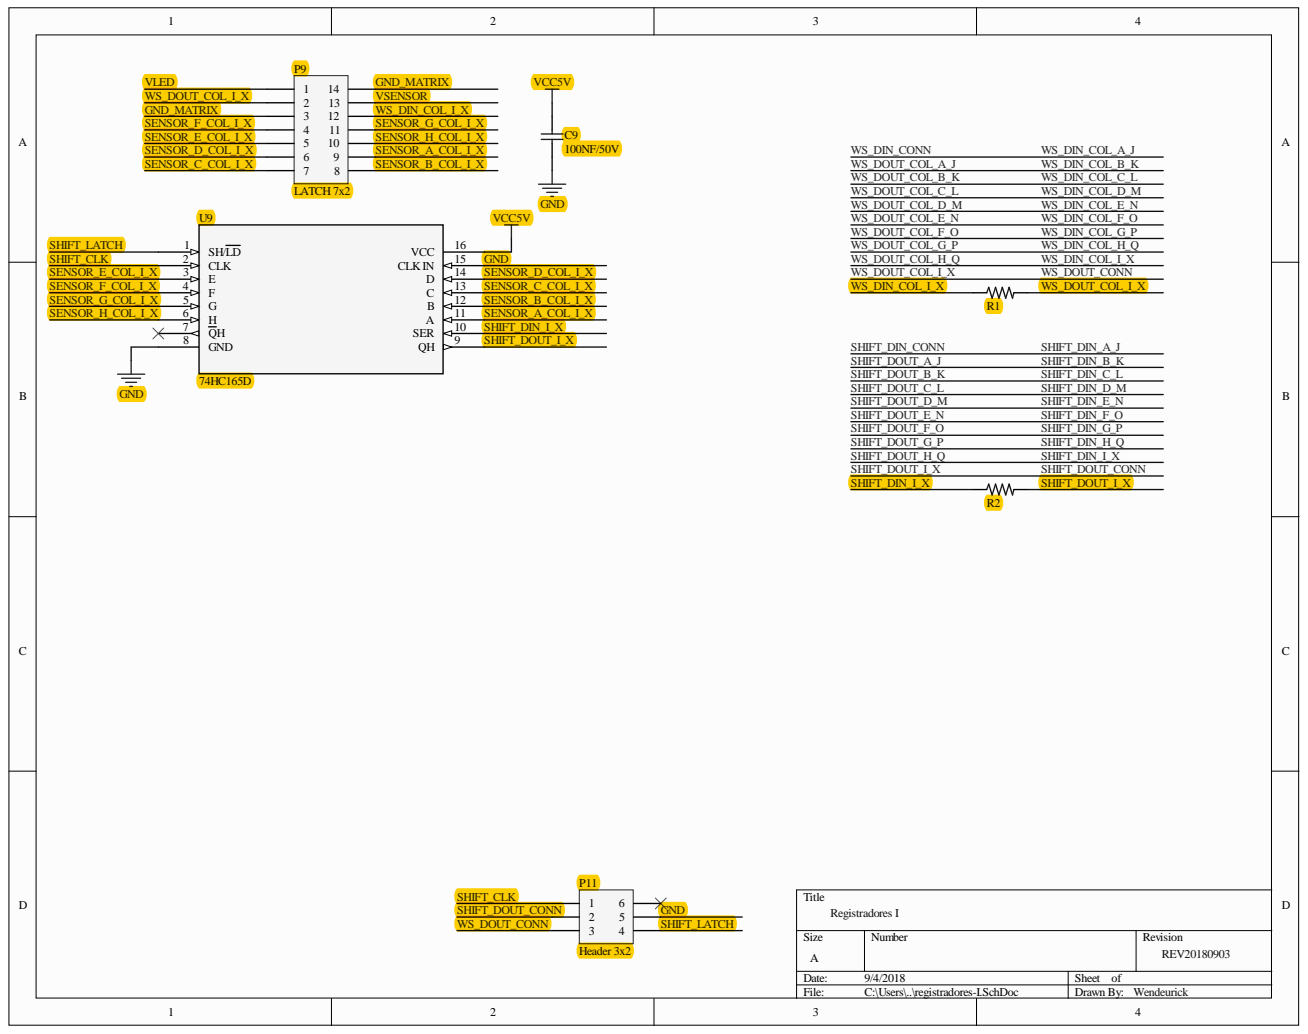
[picture p144: page 4]
