wsilverio/tcc/hardware/registradores/antigo/pdf/pcb-mesa.PDF

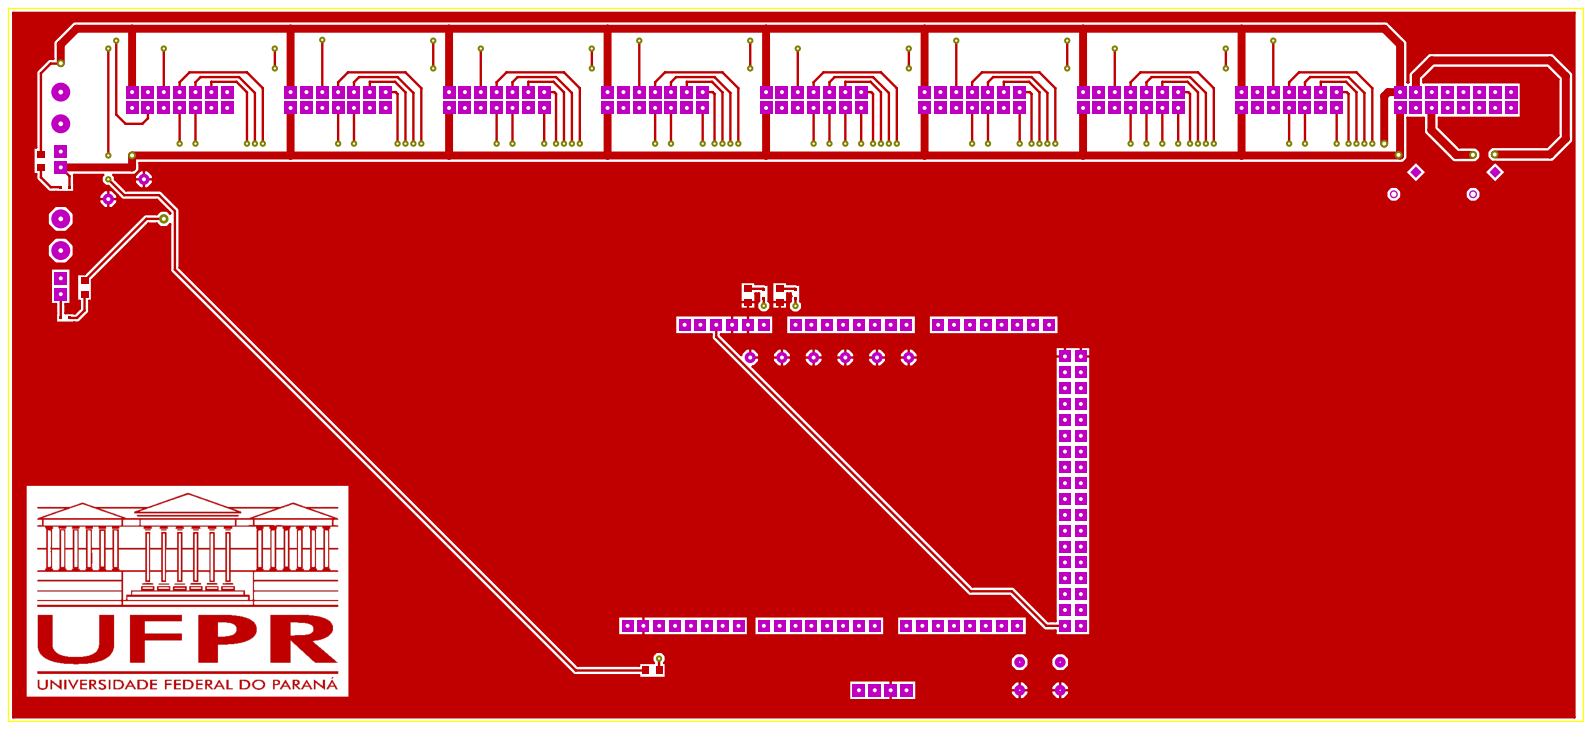
[picture p145: page 1]

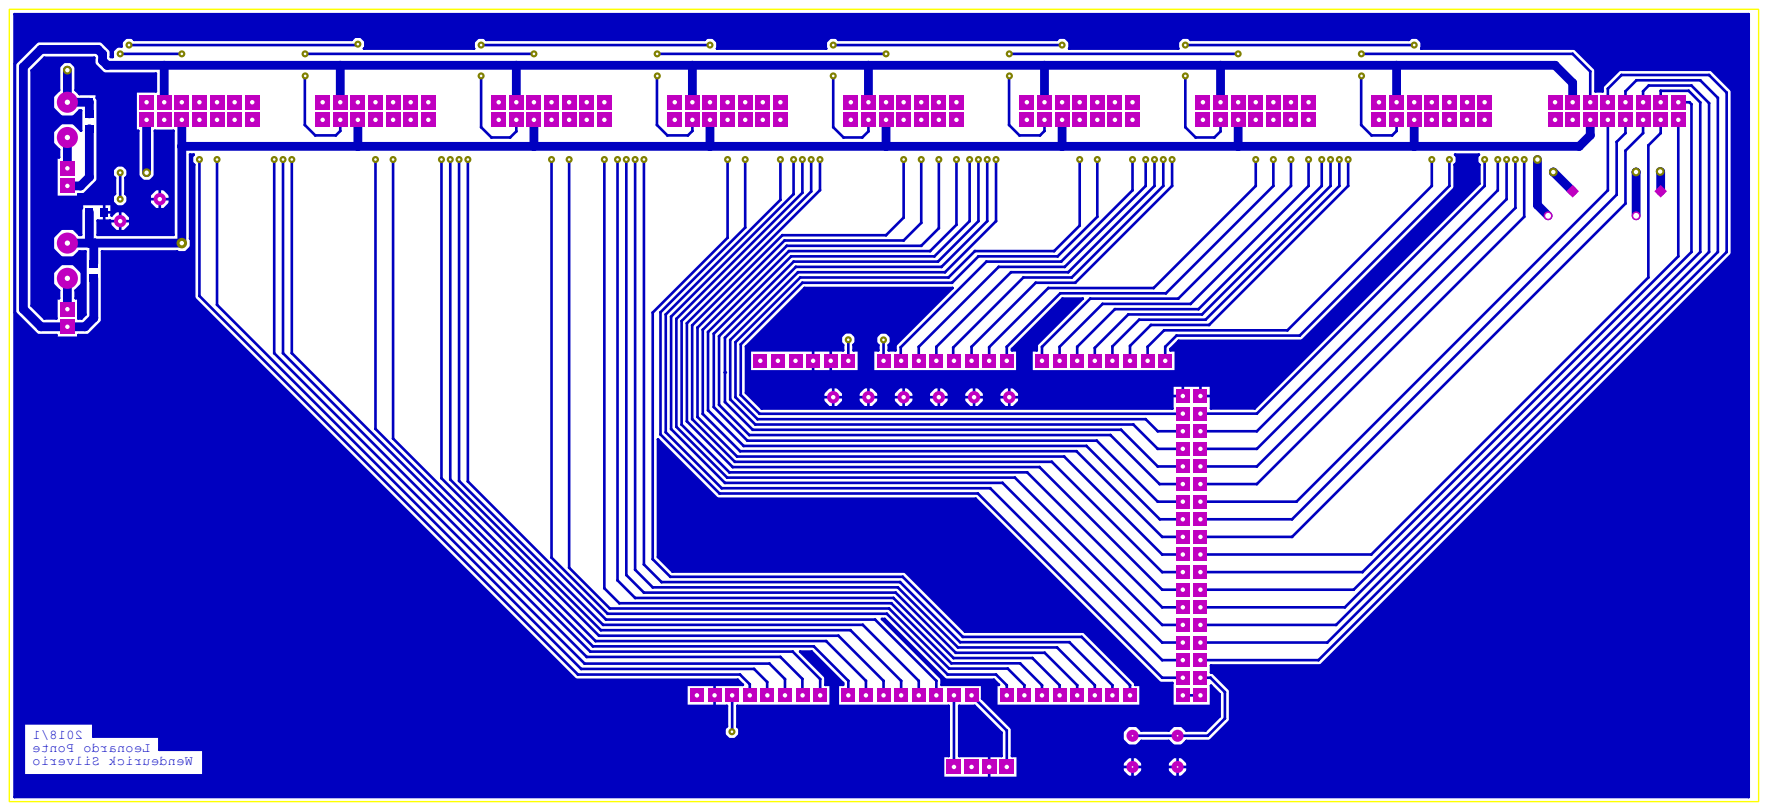
[picture p146: page 2]

etnoP odranoeL oirevliS kciruedneW 1/8102

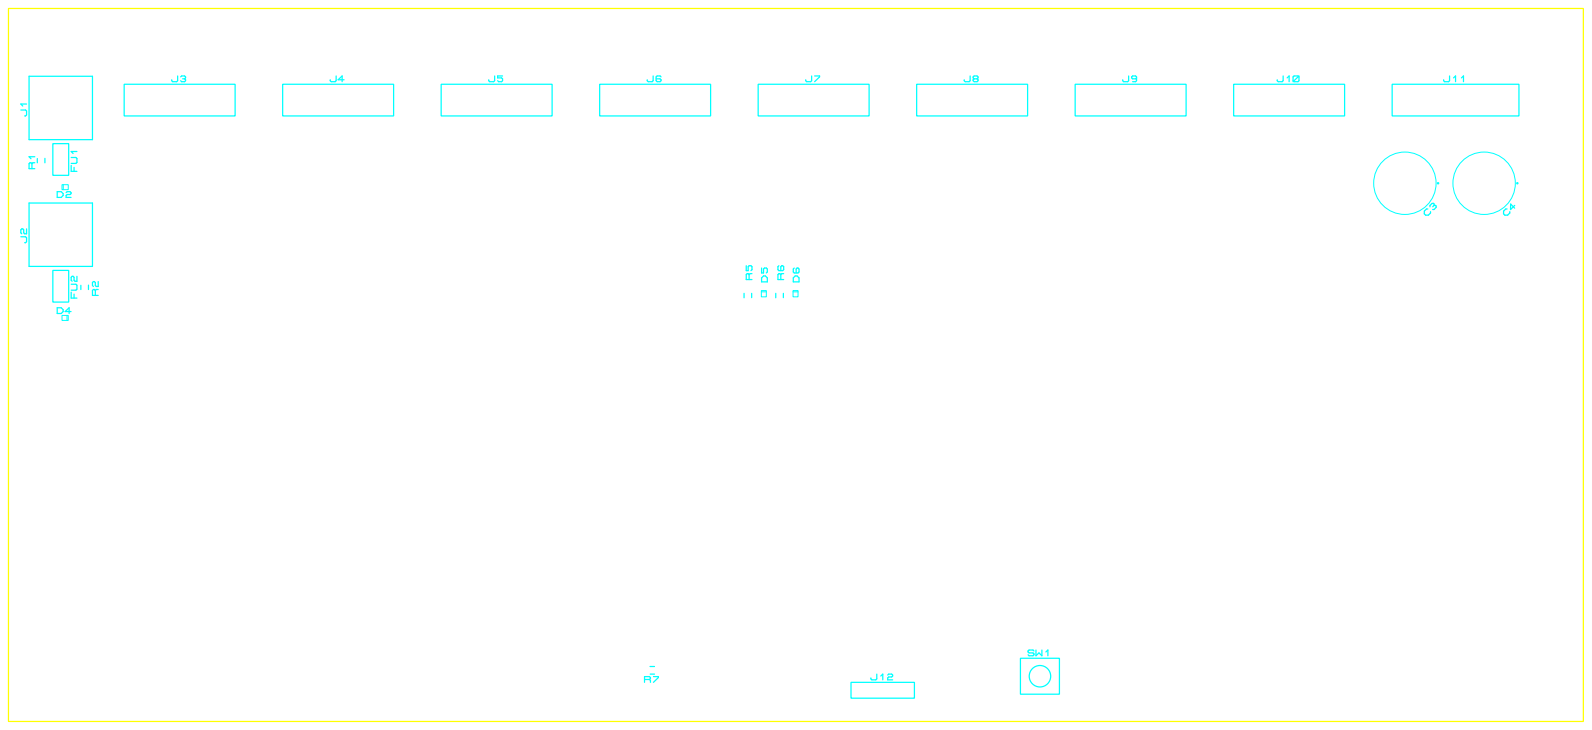
[picture p147: page 3]

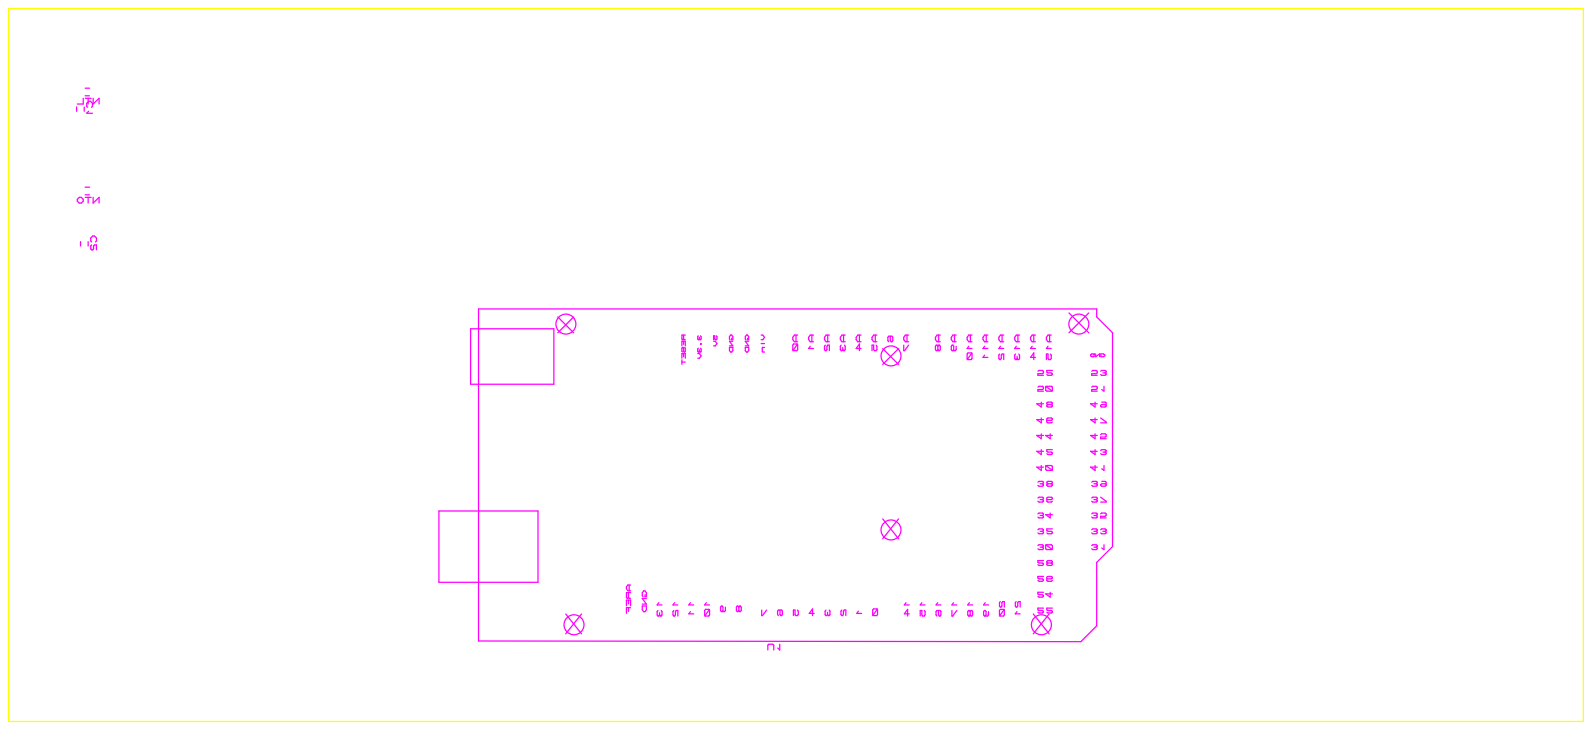
[picture p148: page 4]

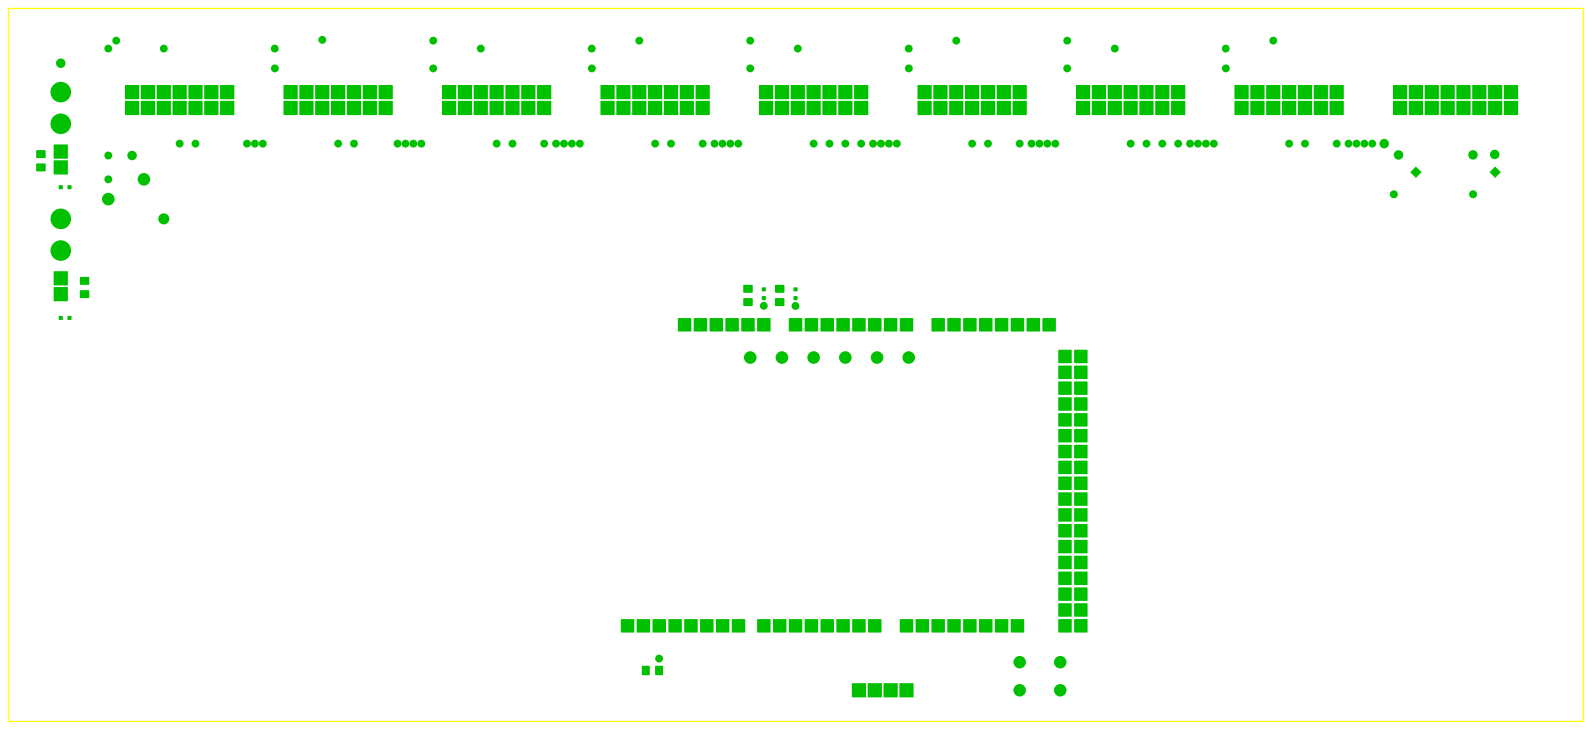
[picture p149: page 5]

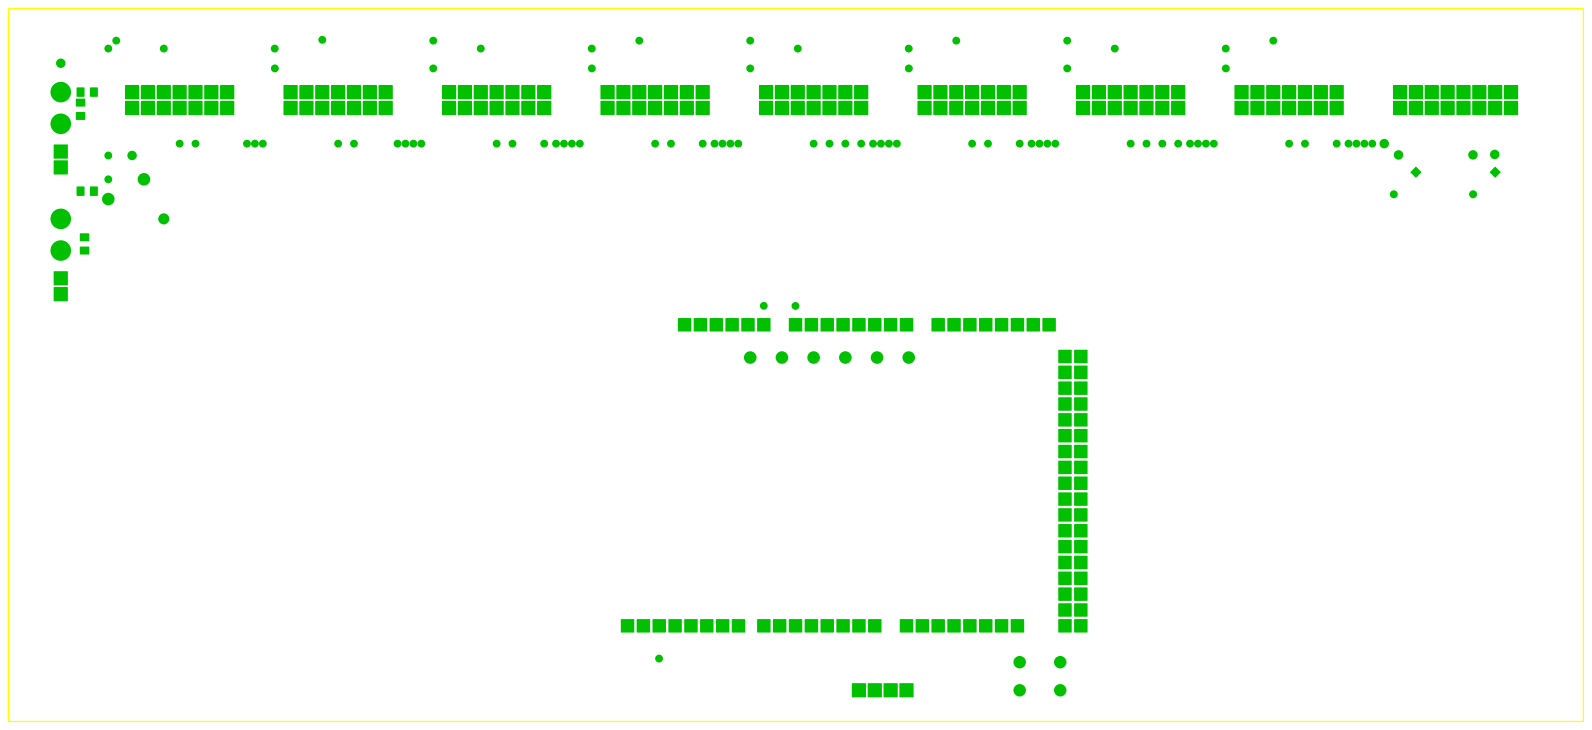
[picture p150: page 6]

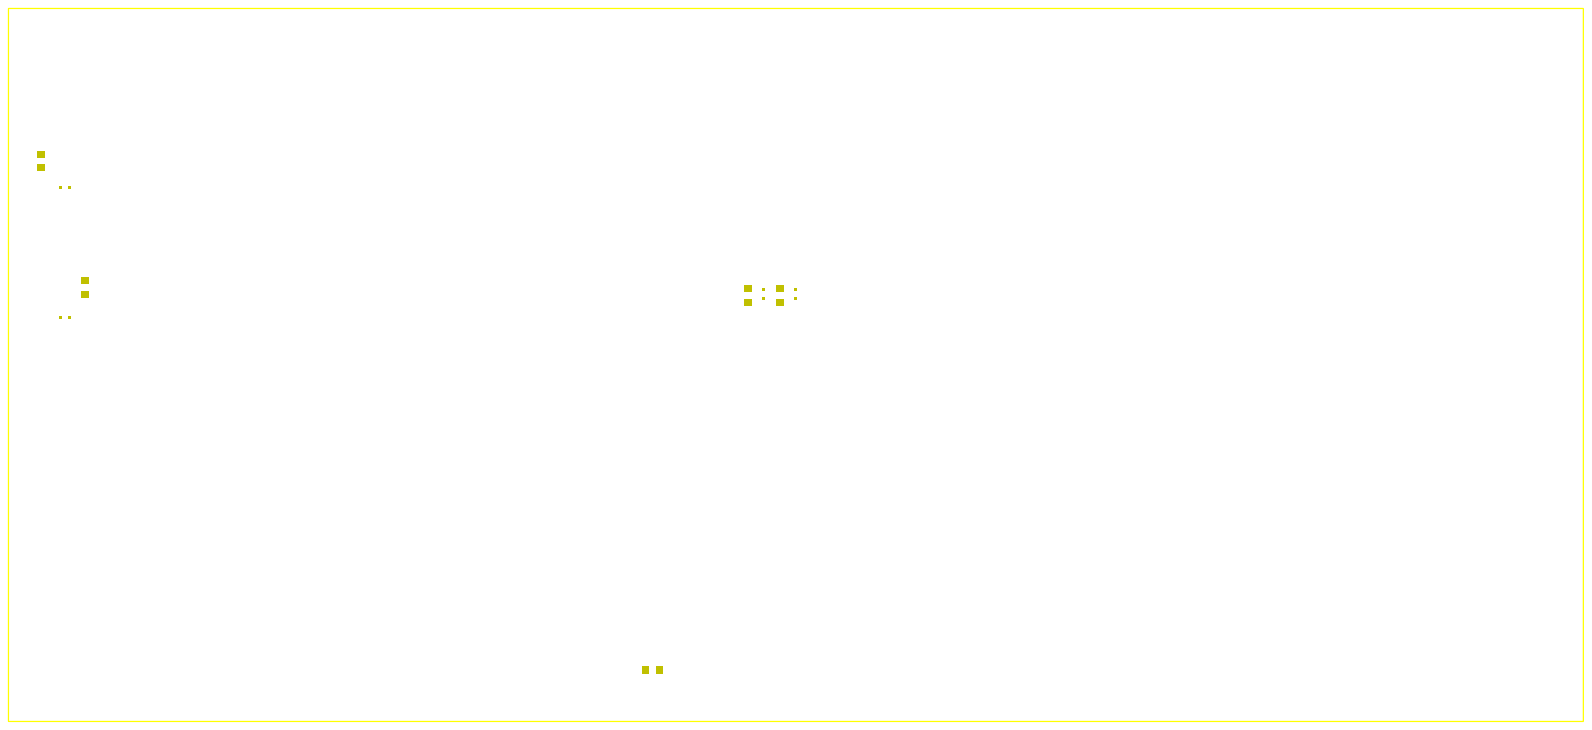
[picture p151: page 7]

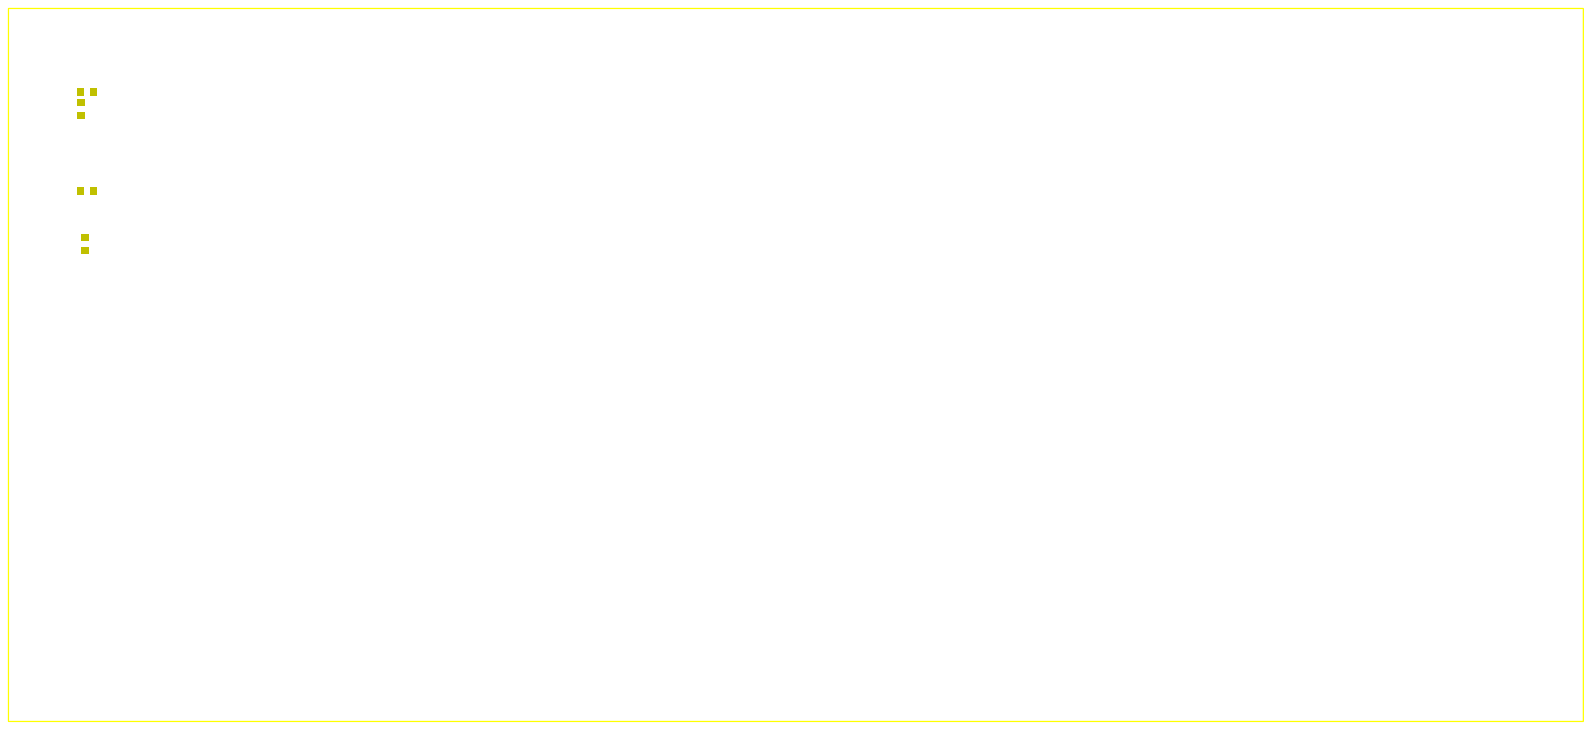
[picture p152: page 8]
