wsilverio/tcc/hardware/registradores/antigo/pdf/sch-mesa.PDF

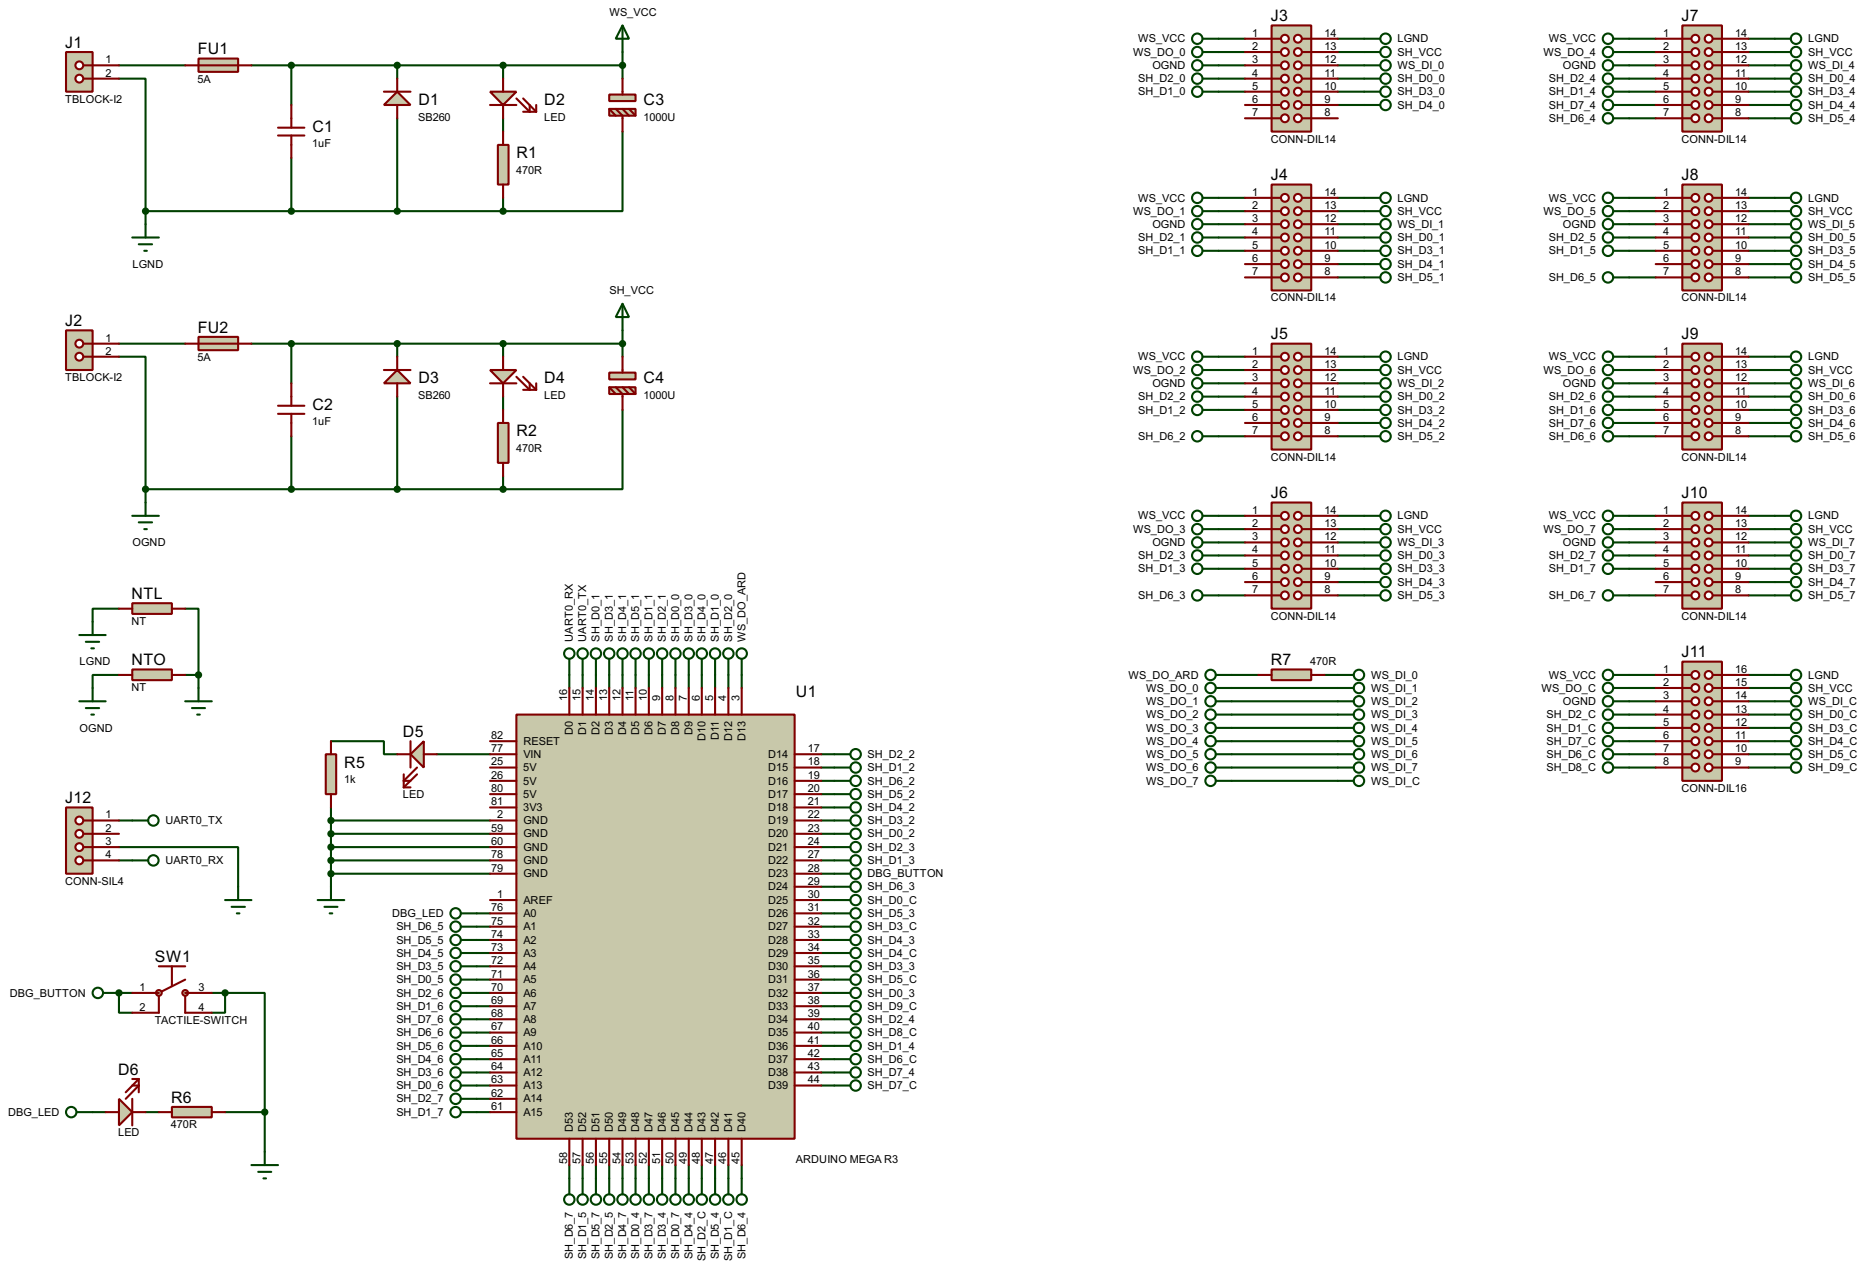
[picture p153: page 1]
