wsilverio/tcc/cad/colunas.pdf

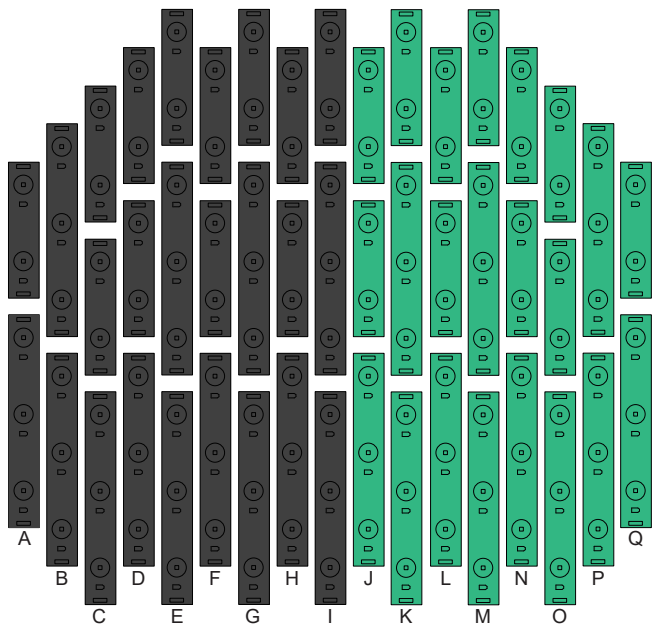
[picture p154: page 1]
