wsilverio/tcc/cad/placas_matriz.pdf

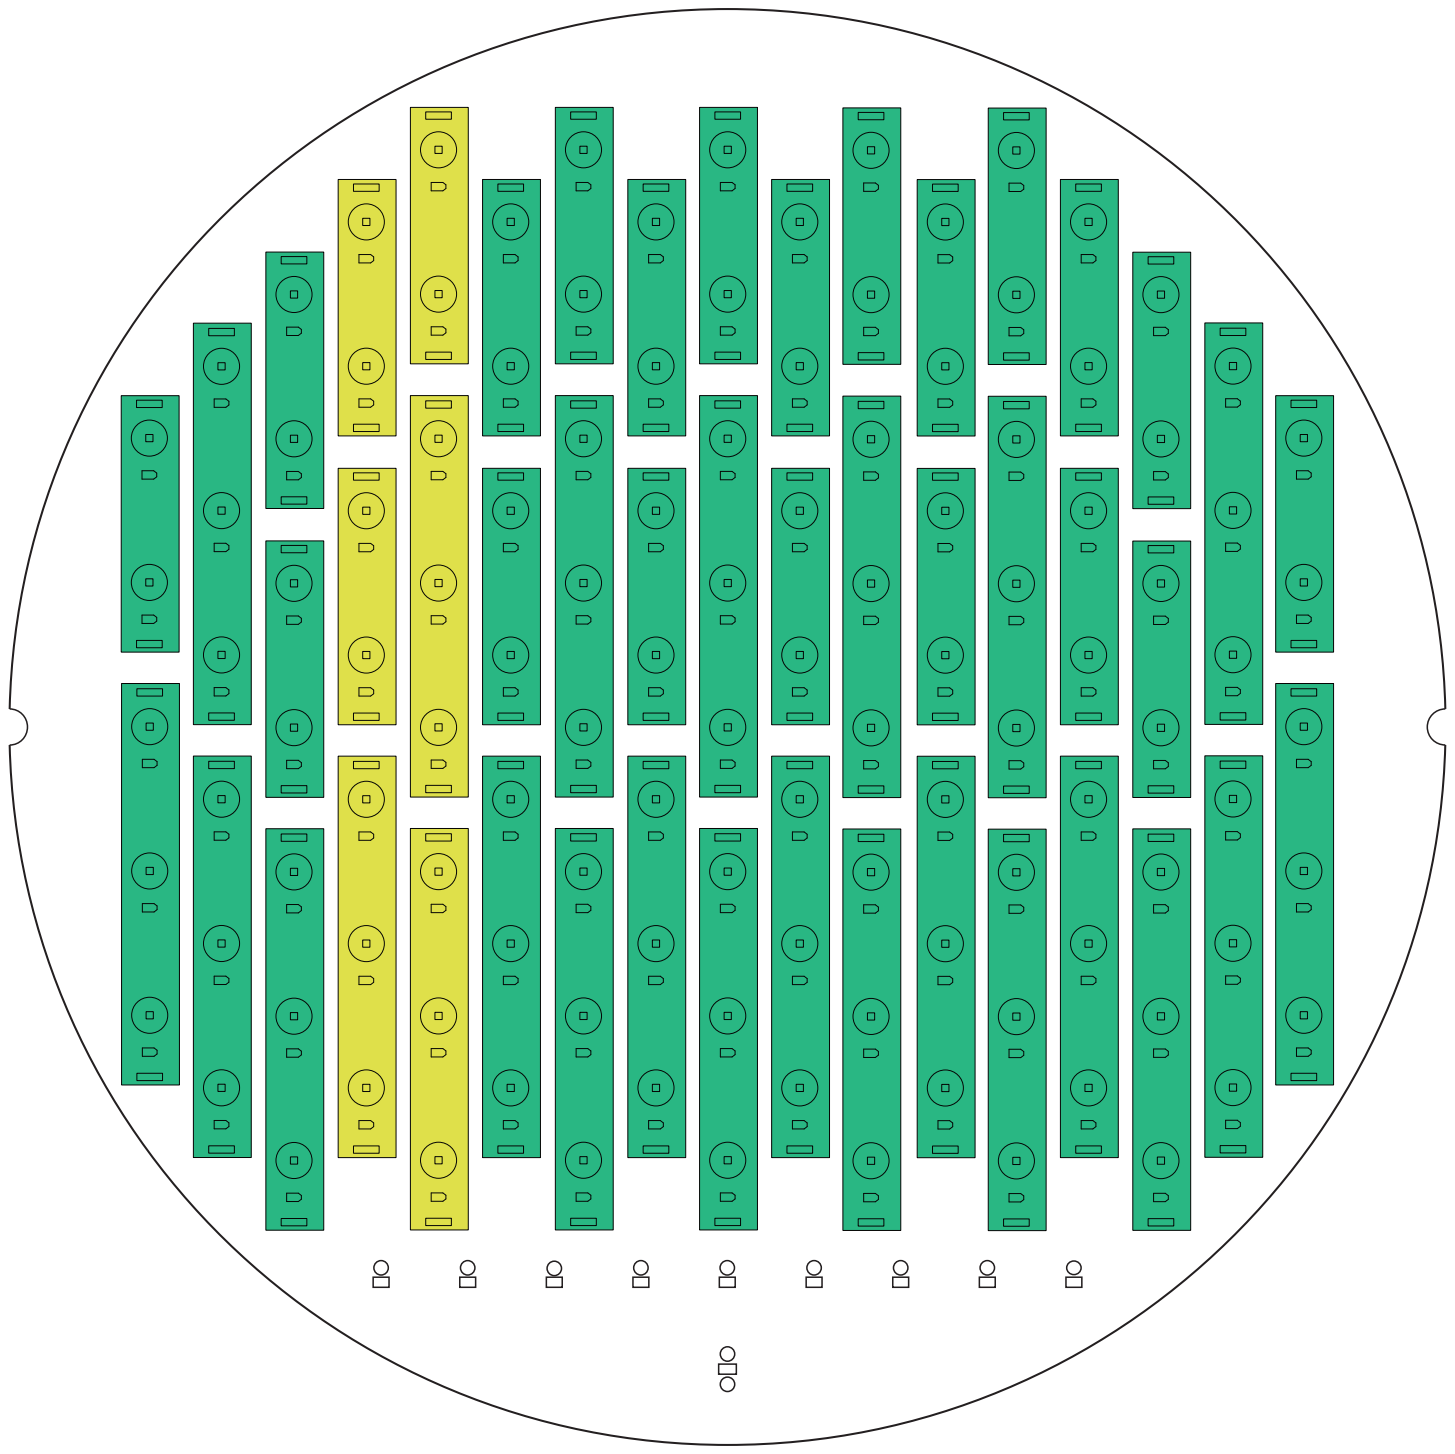
[picture p155: page 1]
