wsilverio/tcc/cad/sentido-leds.pdf

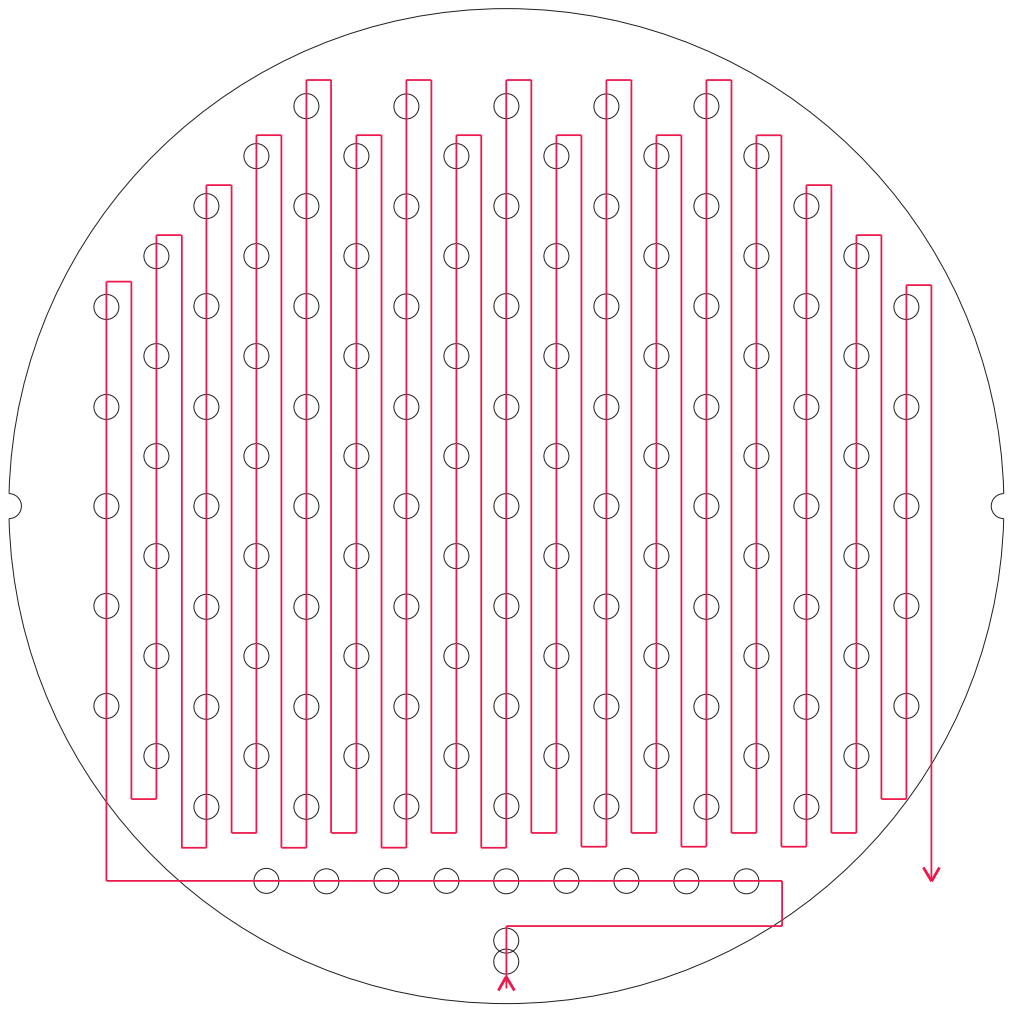
[picture p156: page 1]
