wsilverio/tcc/cad/distancia_bolinhas.pdf

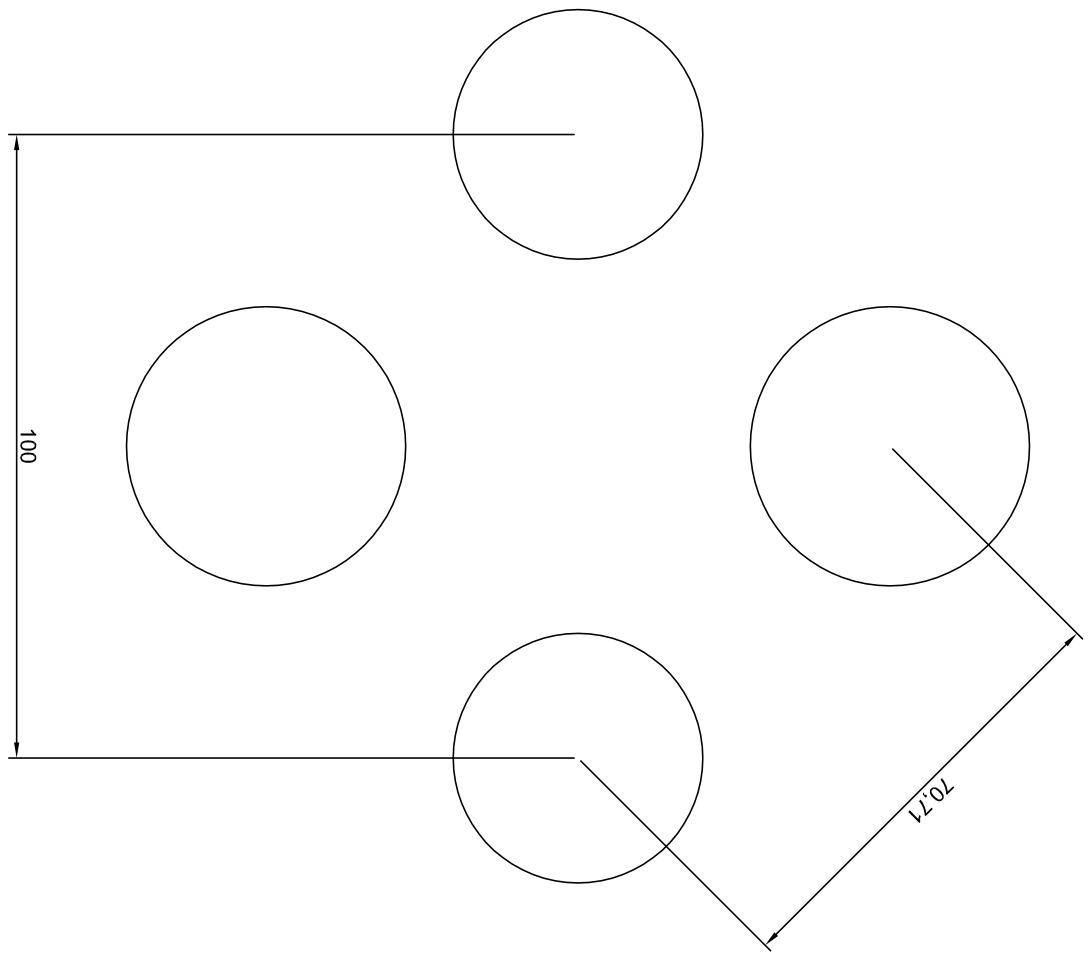
[picture p157: page 1]
