wsilverio/tcc/cad/mesa_diagonal_anotacoes.pdf

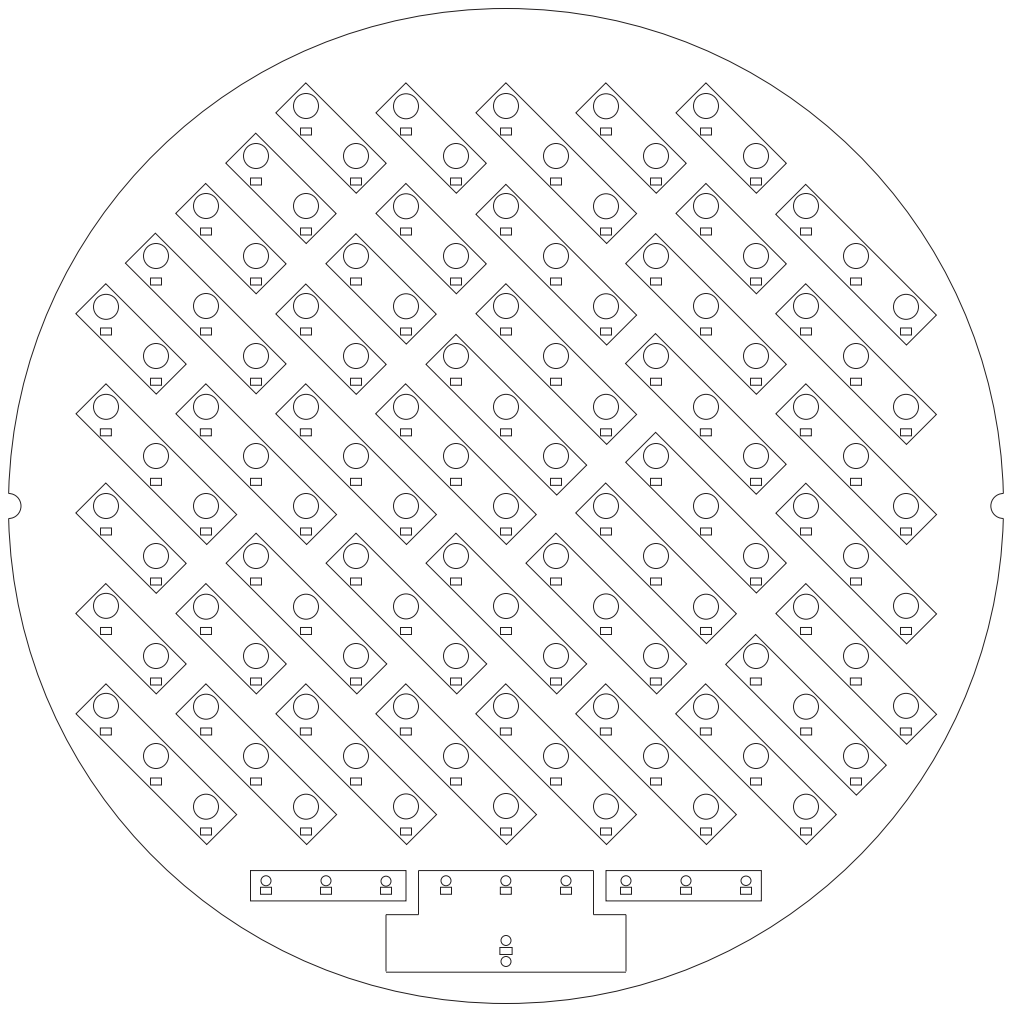
[picture p158: page 1]
