wsilverio/tcc/cad/mesa_vertical_anotacoes.pdf

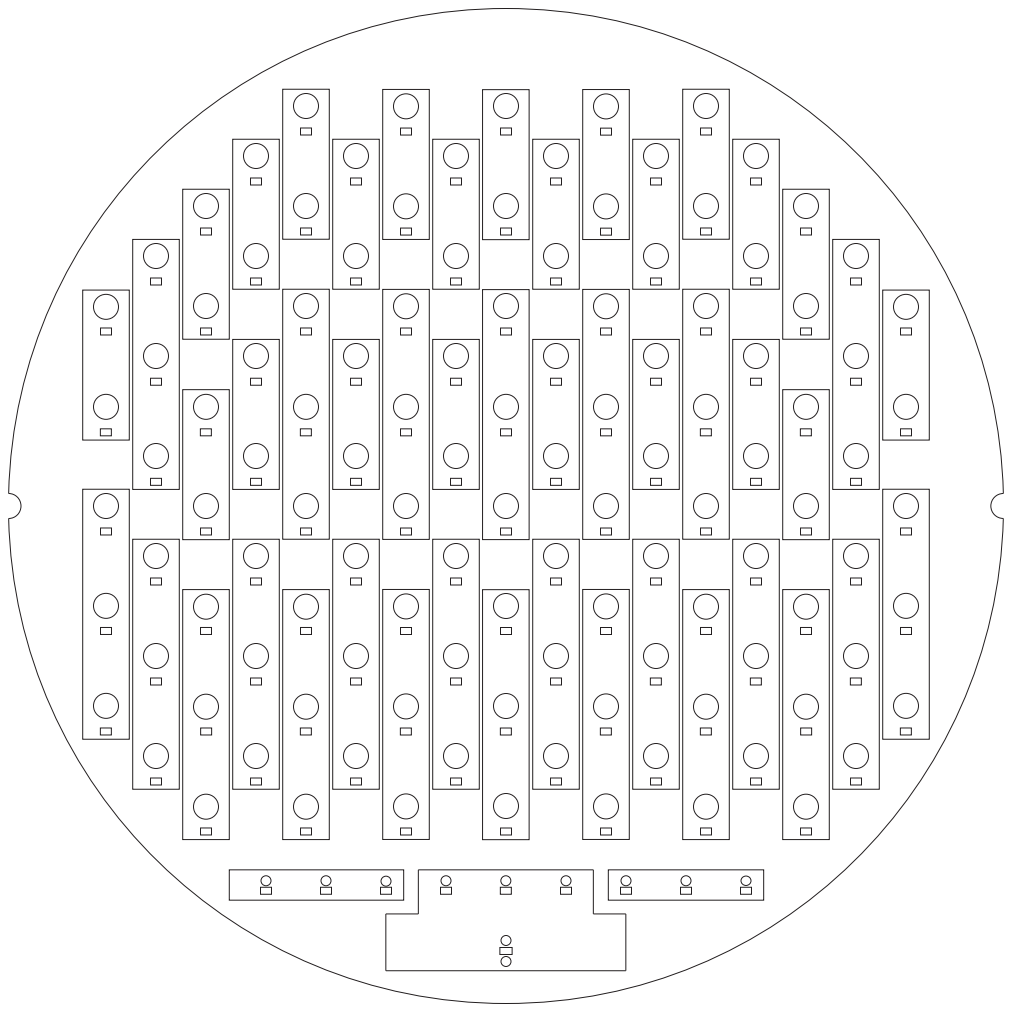
[picture p159: page 1]
