wsilverio/tcc/documentos/tcc/dados/algoritmos/sensors.h

#ifndef MESA_SENSORES_H
#define MESA_SENSORES_H
/////////////////////////////////////////////////////////////////
// bibliotecas
/////////////////////////////////////////////////////////////////
// nativas
// usuário
#include <plomodefs.h>
/////////////////////////////////////////////////////////////////
// definições
/////////////////////////////////////////////////////////////////
// Quantidade de sensores.
#define NUM_SENSORS (128)
// Período de chamada da tarefa: 10ms
#define SENSOR_TASK_TIME_IN_MS (10)
/////////////////////////////////////////////////////////////////
// dados personalizados, enumerações
/////////////////////////////////////////////////////////////////

/////////////////////////////////////////////////////////////////
// variáveis globais
/////////////////////////////////////////////////////////////////

/////////////////////////////////////////////////////////////////
// macros
/////////////////////////////////////////////////////////////////

/////////////////////////////////////////////////////////////////
// protótipo das funções públicas
/////////////////////////////////////////////////////////////////
void init_sensors();
void sensor_task();

#endif //MESA_SENSORES_H
