wsilverio/tcc/documentos/tcc/dados/algoritmos/plomotypes.h

#ifndef PLOMOTYPES_H
#define PLOMOTYPES_H

/////////////////////////////////////////////////////////////////
// definições
/////////////////////////////////////////////////////////////////

/////////////////////////////////////////////////////////////////
// dados personalizados, enumerações
/////////////////////////////////////////////////////////////////

typedef enum {ERROR = 0, SUCCESS = !ERROR} ErrorStatus;
typedef enum {RESET = 0, SET = !RESET} FlagStatus;
typedef enum {DISABLE = 0, ENABLE = !DISABLE} FunctionalState;

#endif // PLOMOTYPES_H
