wsilverio/tcc/documentos/tcc/dados/algoritmos/uart.cpp

/////////////////////////////////////////////////////////////////
// bibliotecas
/////////////////////////////////////////////////////////////////
// nativas
#include <SmingCore/SmingCore.h>
// usuário
#include <uart.h>
/////////////////////////////////////////////////////////////////
// definições
/////////////////////////////////////////////////////////////////
#define UART_BAUDRATE (115200)
/////////////////////////////////////////////////////////////////
// dados personalizados, enumerações
/////////////////////////////////////////////////////////////////

/////////////////////////////////////////////////////////////////
// variáveis globais
/////////////////////////////////////////////////////////////////

/////////////////////////////////////////////////////////////////
// variáveis privadas do módulo
/////////////////////////////////////////////////////////////////

/////////////////////////////////////////////////////////////////
// macros
/////////////////////////////////////////////////////////////////

/////////////////////////////////////////////////////////////////
// protótipo das funções privadas
/////////////////////////////////////////////////////////////////

/////////////////////////////////////////////////////////////////
// implementação do módulo
/////////////////////////////////////////////////////////////////

/**
 * @brief Inicialização da UART.
 * @param None.
 * @return None.
 */
void init_uart()
{
    Serial.begin(UART_BAUDRATE);
    Serial.systemDebugOutput(false);
}
