wsilverio/tcc/documentos/tcc/dados/algoritmos/application.cpp

/////////////////////////////////////////////////////////////////
// bibliotecas
/////////////////////////////////////////////////////////////////
// nativas
#include <SmingCore/SmingCore.h>
// usuário
#include <user_config.h>
#include <plomodefs.h>
#include <hardware.h>
#include <uart.h>
#include <sensors.h>
#include <matrix.h>
/////////////////////////////////////////////////////////////////
// definições
/////////////////////////////////////////////////////////////////

/////////////////////////////////////////////////////////////////
// dados personalizados, enumerações
/////////////////////////////////////////////////////////////////

/////////////////////////////////////////////////////////////////
// variáveis privadas do módulo
/////////////////////////////////////////////////////////////////
Timer debounceTimer;
/////////////////////////////////////////////////////////////////
// variáveis globais
/////////////////////////////////////////////////////////////////

/////////////////////////////////////////////////////////////////
// macros
/////////////////////////////////////////////////////////////////

/////////////////////////////////////////////////////////////////
// protótipo das funções públicas
/////////////////////////////////////////////////////////////////

/**
* @brief Inicialização do sistema.
* @param None.
* @return None.
*/
void init()
{
    // Inicialização das portas.
    init_gpio();

    // Inicializa a UART.
    init_uart();

    // Inicializa o módulo ARTNET.
    //init_artnet();

    // Inicialização dos sensores / SPI.
    init_sensors();

    // Inicializa a máquina dos LEDs.
    init_matrix();

    /////////////////////////////////
    // Tarefas periódicas.

    // Sensores
    debounceTimer.initializeMs(SENSOR_TASK_TIME_IN_MS, sensor_task).start();
}
