wsilverio/tcc/documentos/tcc/dados/algoritmos/matrix.cpp

/////////////////////////////////////////////////////////////////
// bibliotecas
/////////////////////////////////////////////////////////////////
// nativas
#include <Adafruit_NeoPixel/Adafruit_NeoPixel.h>
// usuário
#include <matrix.h>
#include <hardware.h>
/////////////////////////////////////////////////////////////////
// definições
/////////////////////////////////////////////////////////////////
#define LED_TYPE (NEO_GRB + NEO_KHZ800)
/////////////////////////////////////////////////////////////////
// dados personalizados, enumerações
/////////////////////////////////////////////////////////////////

/////////////////////////////////////////////////////////////////
// variáveis globais
/////////////////////////////////////////////////////////////////

/////////////////////////////////////////////////////////////////
// variáveis privadas do módulo
/////////////////////////////////////////////////////////////////
Adafruit_NeoPixel matrix = Adafruit_NeoPixel(NUM_PIXELS, GPIO_LEDS_DOUT, LED_TYPE);
/////////////////////////////////////////////////////////////////
// macros
/////////////////////////////////////////////////////////////////

/////////////////////////////////////////////////////////////////
// protótipo das funções privadas
/////////////////////////////////////////////////////////////////

/////////////////////////////////////////////////////////////////
// implementação do módulo
/////////////////////////////////////////////////////////////////

/**
 * @brief Inicialização dos LEDs WS2812.
 * @param None.
 * @return None.
 */
void init_matrix()
{
    // Inicialmente apagados.
    matrix.begin();
    matrix.clear();
    matrix.show();
}
