wsilverio/tcc/documentos/tcc/dados/algoritmos/matrix.h

#ifndef MESA_MATRIX_H
#define MESA_MATRIX_H

/////////////////////////////////////////////////////////////////
// bibliotecas
/////////////////////////////////////////////////////////////////
// nativas
// usuário
#include <plomodefs.h>
#include <sensors.h>
/////////////////////////////////////////////////////////////////
// definições
/////////////////////////////////////////////////////////////////
// A mesa é composta por 128 pares sensor/led
// Porém, o botão "power" possui 1 led a mais.
#define NUM_PIXELS (NUM_SENSORS+1)
/////////////////////////////////////////////////////////////////
// dados personalizados, enumerações
/////////////////////////////////////////////////////////////////

/////////////////////////////////////////////////////////////////
// variáveis globais
/////////////////////////////////////////////////////////////////

/////////////////////////////////////////////////////////////////
// macros
/////////////////////////////////////////////////////////////////

/////////////////////////////////////////////////////////////////
// protótipo das funções públicas
/////////////////////////////////////////////////////////////////

void init_matrix();

#endif //MESA_MATRIX_H
