wsilverio/tcc/documentos/tcc/dados/algoritmos/tabmask8.h

#ifndef MESA_TABMASK_H
#define MESA_TABMASK_H
/////////////////////////////////////////////////////////////////
// bibliotecas
/////////////////////////////////////////////////////////////////
// nativas
#include <cstdint>
// usuário
#include <plomodefs.h>
/////////////////////////////////////////////////////////////////
// definições
/////////////////////////////////////////////////////////////////

/////////////////////////////////////////////////////////////////
// dados personalizados, enumerações
/////////////////////////////////////////////////////////////////

/////////////////////////////////////////////////////////////////
// variáveis globais
/////////////////////////////////////////////////////////////////
const uint8_t TABMASK_8[8] = {0x01, 0x02, 0x04, 0x08, 0x10, 0x20, 0x40, 0x80};
/////////////////////////////////////////////////////////////////
// macros
/////////////////////////////////////////////////////////////////

/////////////////////////////////////////////////////////////////
// protótipo das funções públicas
/////////////////////////////////////////////////////////////////

#endif //MESA_TABMASK_H
